copperheadhq/copperhead/manual-tests/real-designs/examples/cm5_minima/render/drawn.png

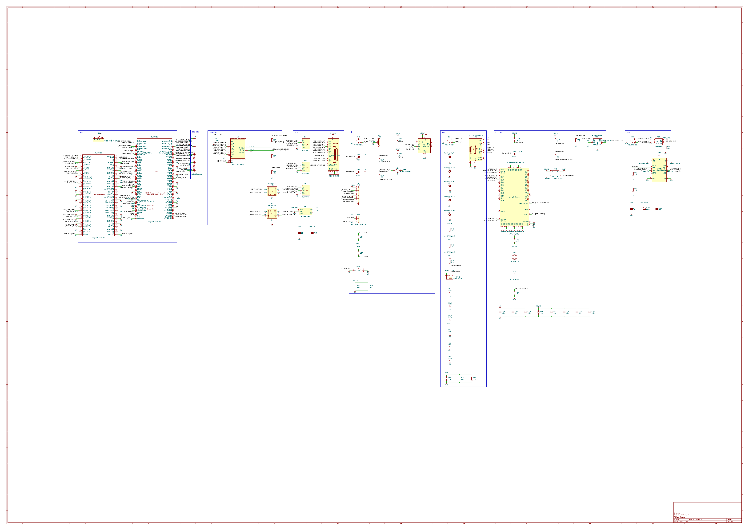
manual-tests/real-designs/examples/cm5_minima/render/drawn.png
