copperheadhq/copperhead/manual-tests/real-designs/examples/cm5_minima/render/original-CM5_MINIMA_3-HDMI.png

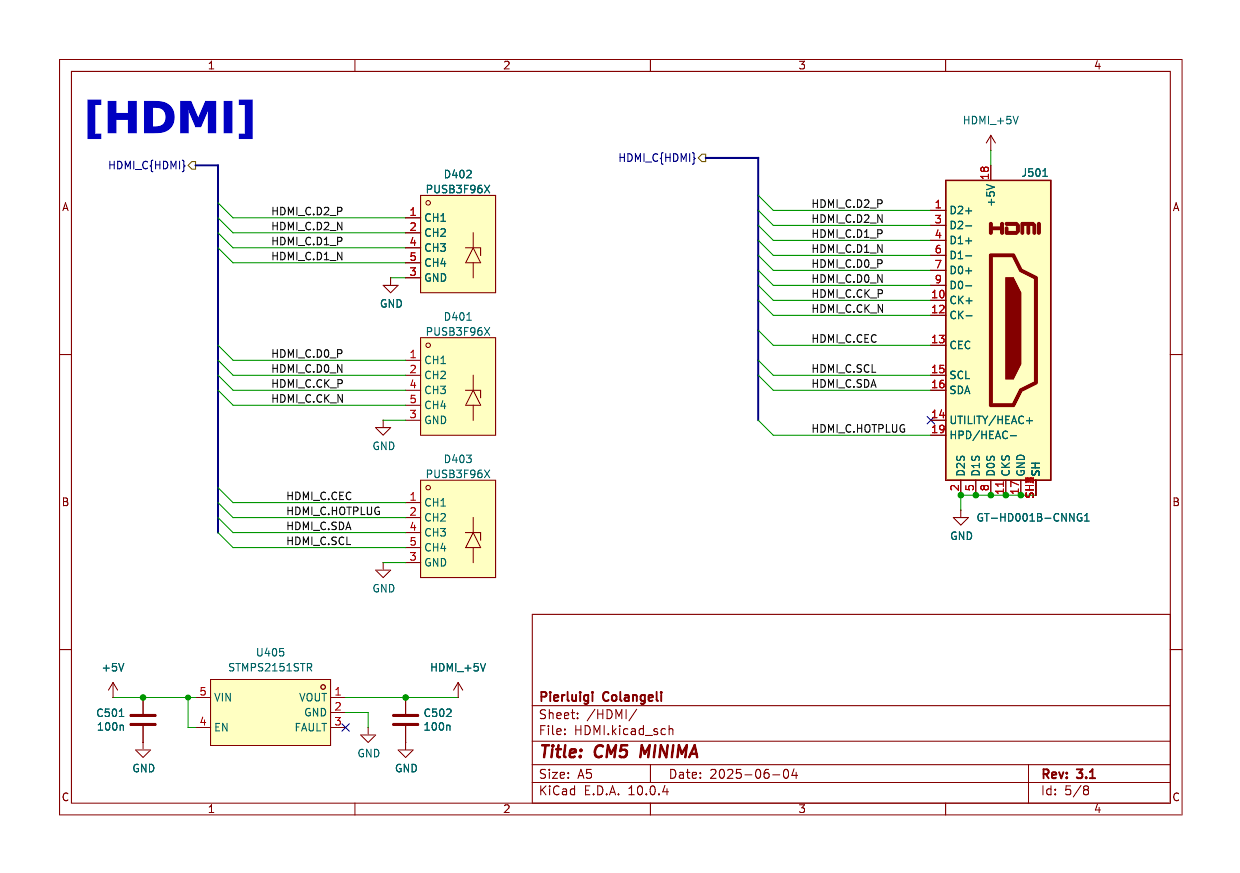
manual-tests/real-designs/examples/cm5_minima/render/original-CM5_MINIMA_3-HDMI.png
