copperheadhq/copperhead/manual-tests/real-designs/examples/complex_hierarchy/render/original-complex_hierarchy-ampli_ht_horizontal.png

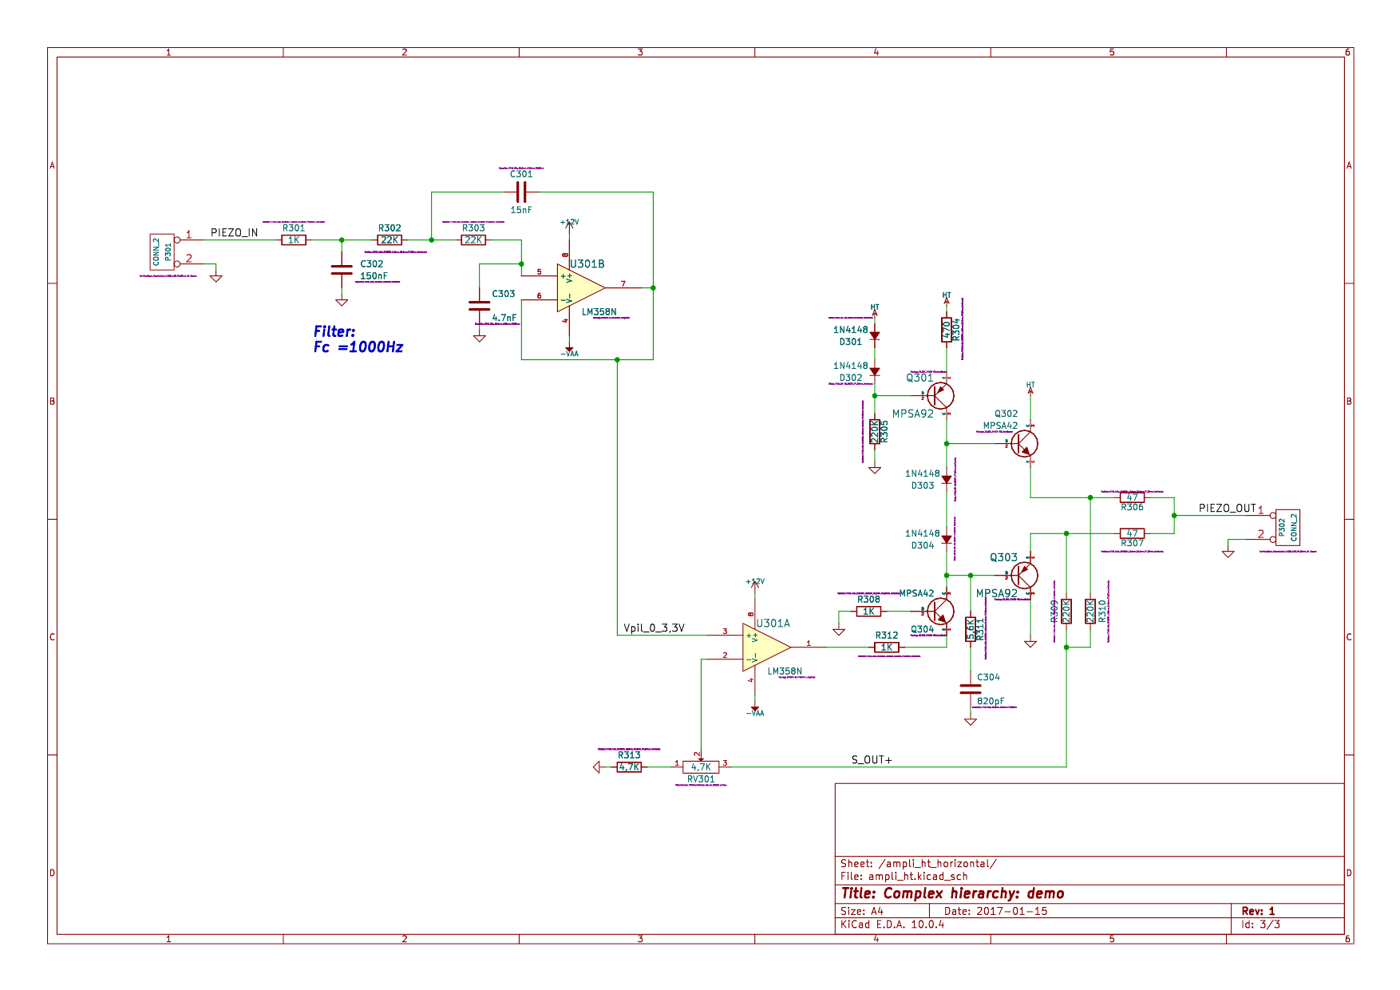
manual-tests/real-designs/examples/complex_hierarchy/render/original-complex_hierarchy-ampli_ht_horizontal.png
