copperheadhq/copperhead/manual-tests/real-designs/examples/complex_hierarchy/render/original-complex_hierarchy.png

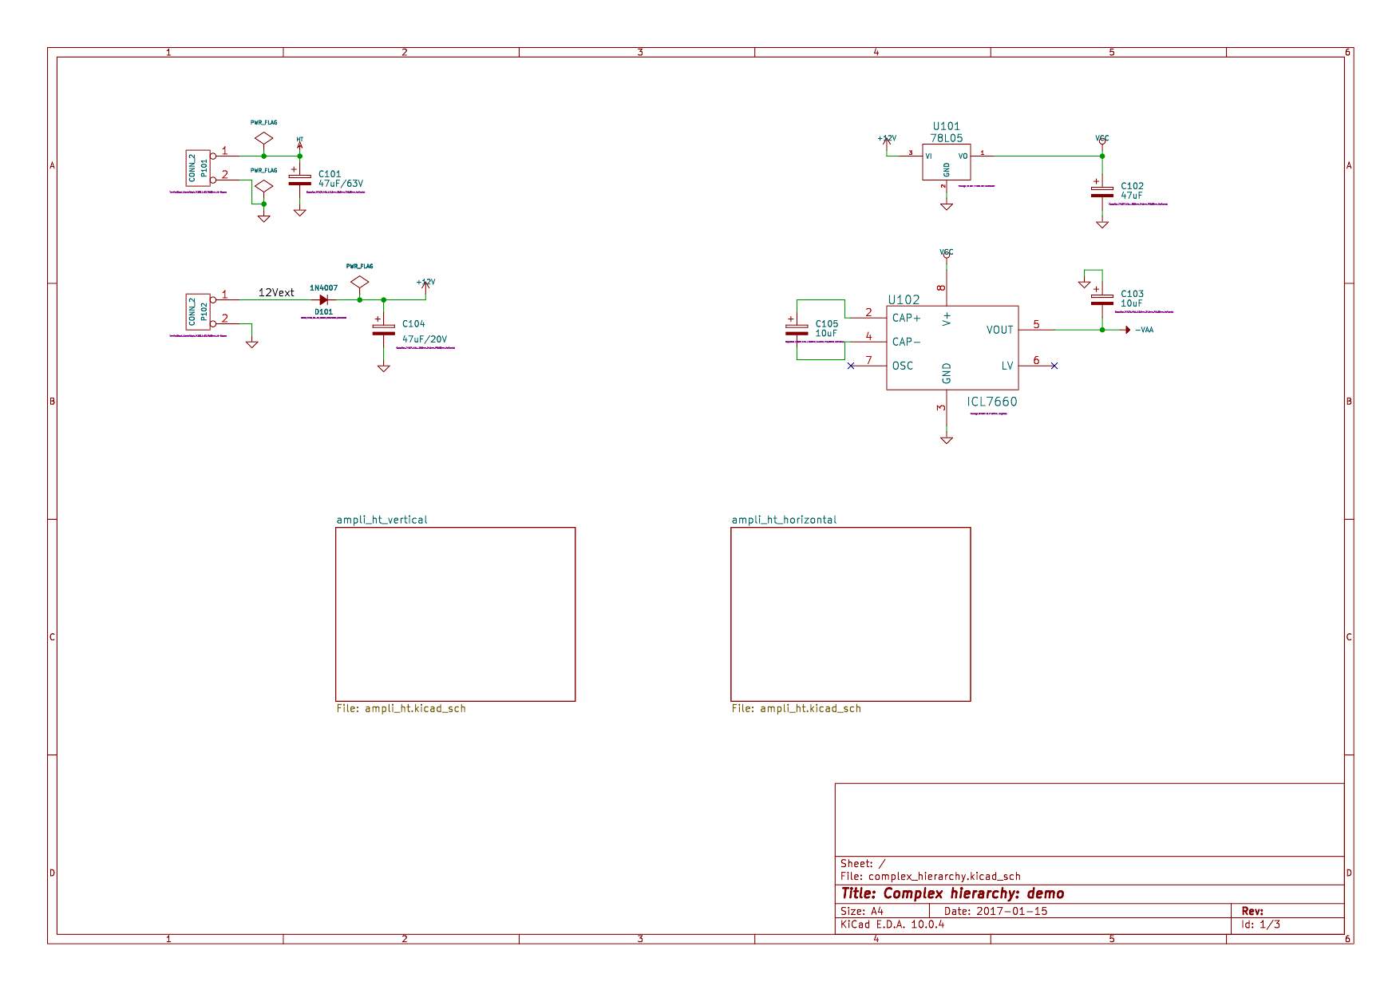
manual-tests/real-designs/examples/complex_hierarchy/render/original-complex_hierarchy.png
