copperheadhq/copperhead/manual-tests/real-designs/examples/ecc83/render/drawn.png

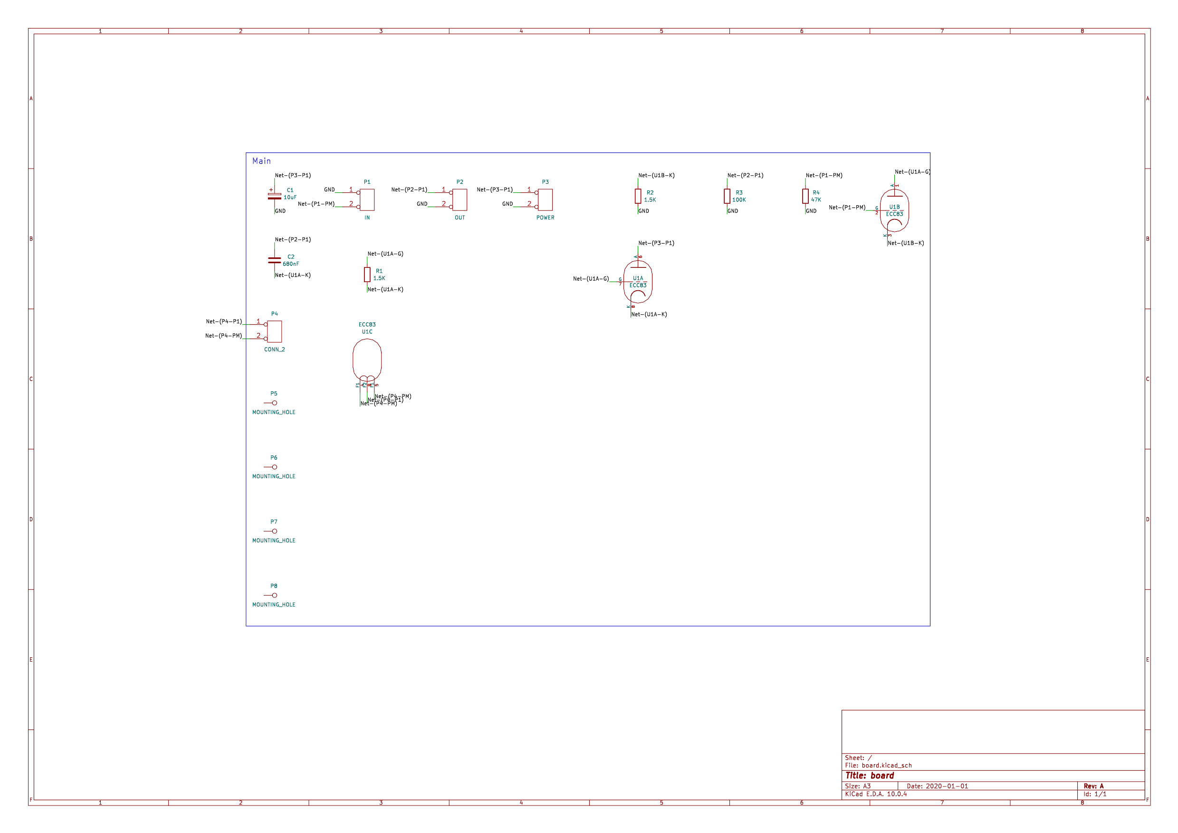
manual-tests/real-designs/examples/ecc83/render/drawn.png
