copperheadhq/copperhead/manual-tests/real-designs/examples/ecc83/render/original.png

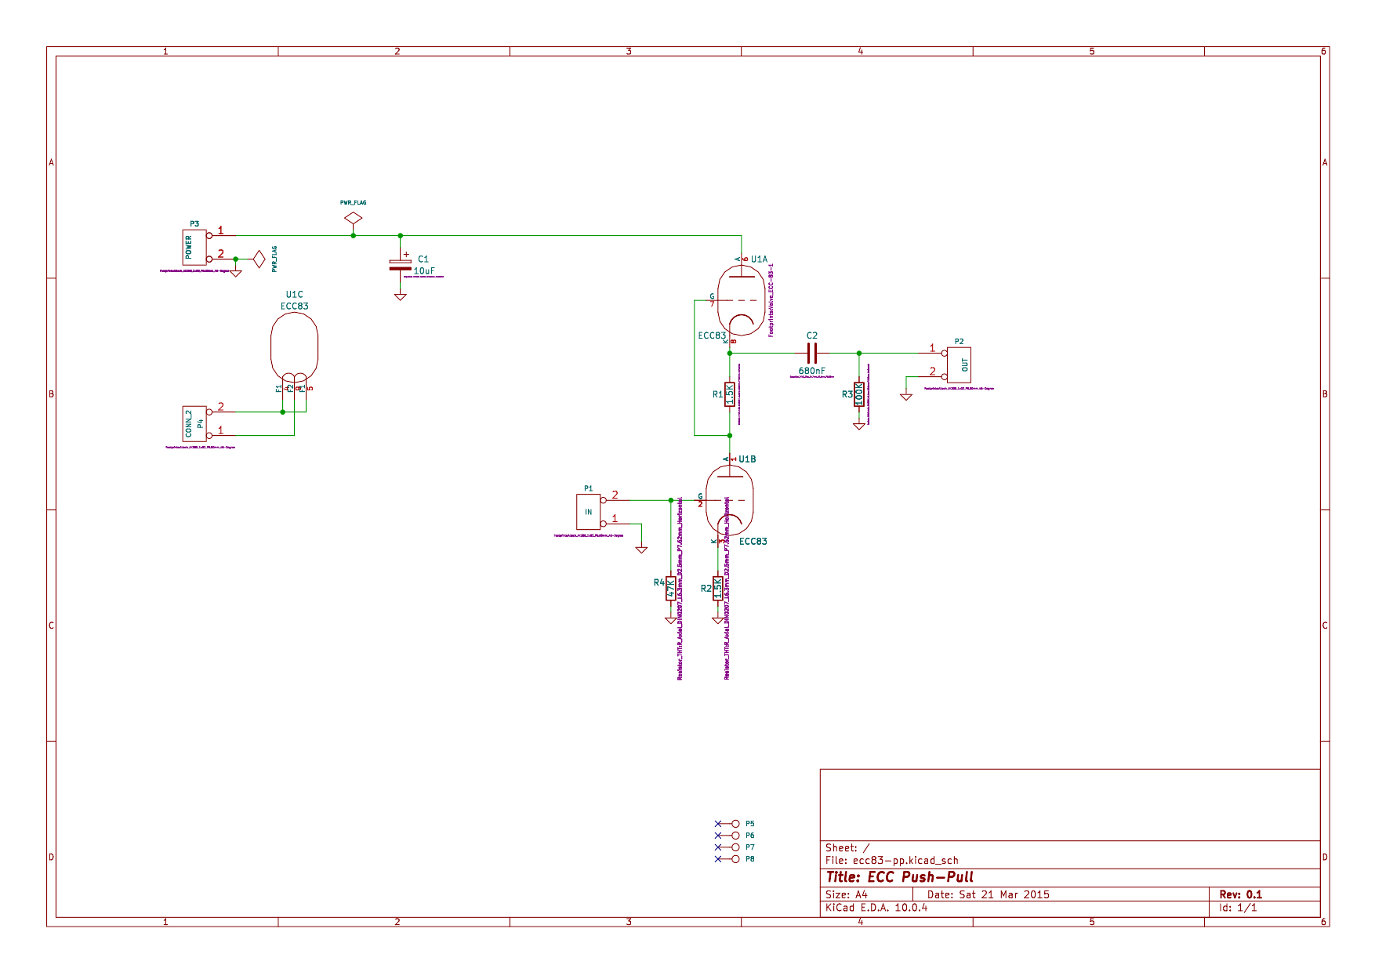
manual-tests/real-designs/examples/ecc83/render/original.png
