copperheadhq/copperhead/manual-tests/real-designs/examples/interf_u/render/drawn.png

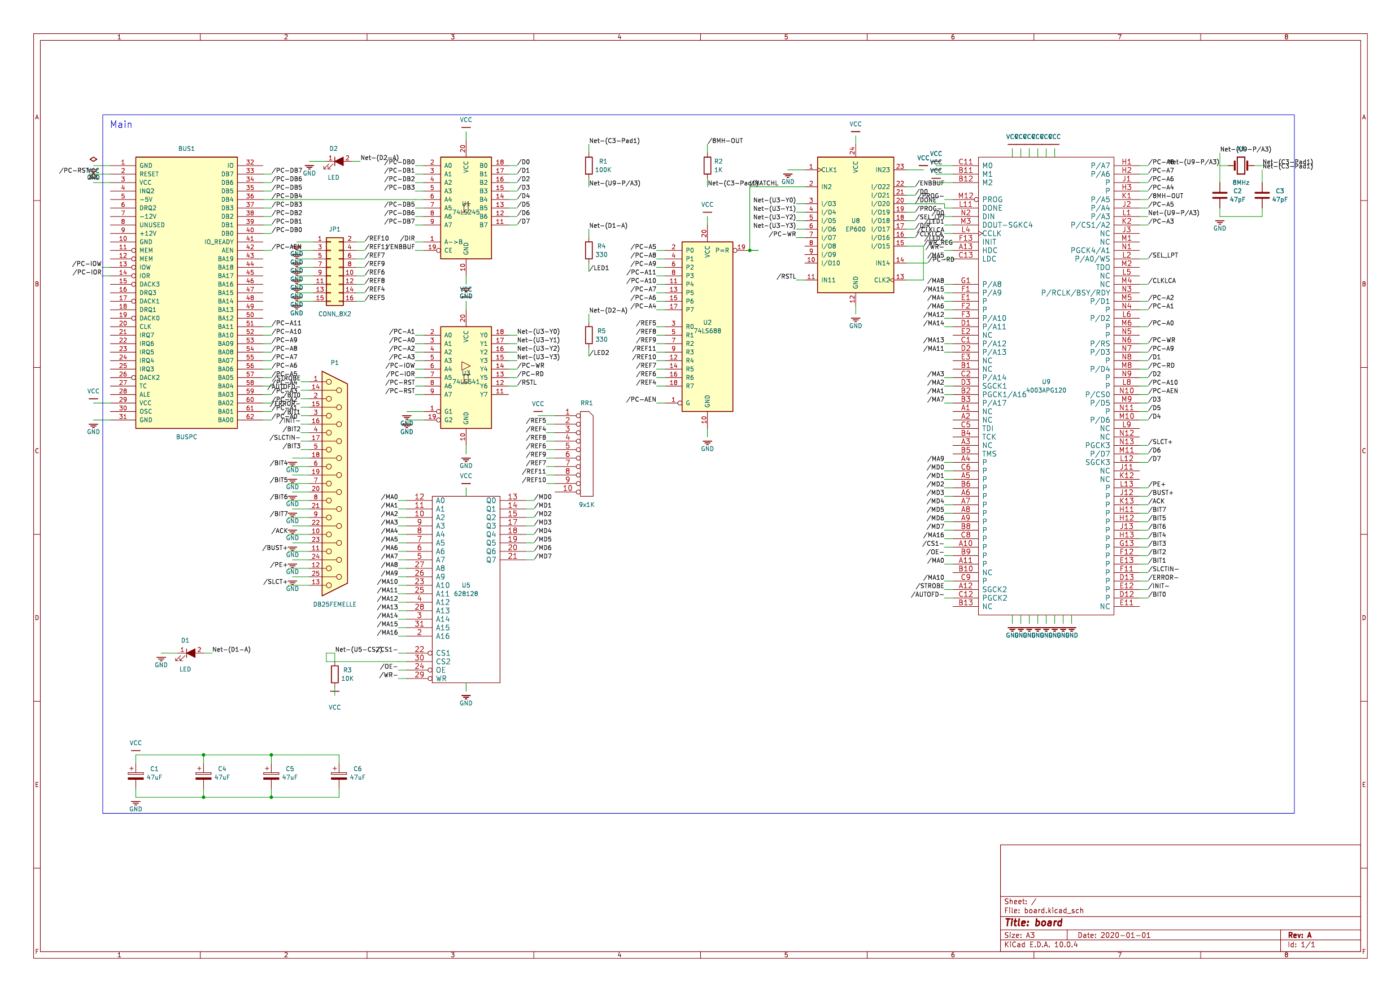
manual-tests/real-designs/examples/interf_u/render/drawn.png
