copperheadhq/copperhead/manual-tests/real-designs/examples/interf_u/render/original.png

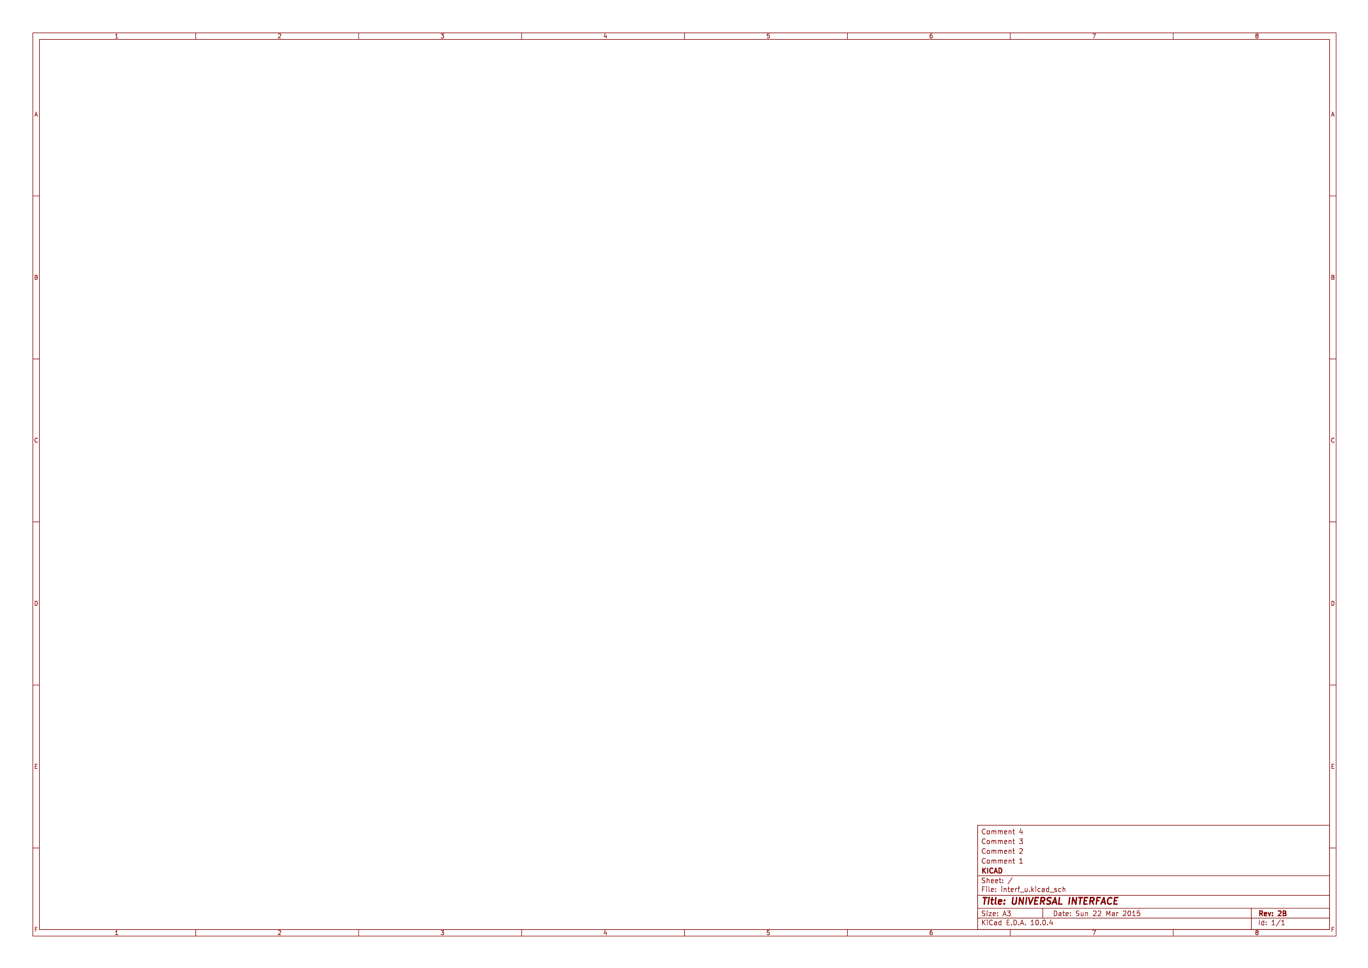
manual-tests/real-designs/examples/interf_u/render/original.png
