copperheadhq/copperhead/manual-tests/real-designs/examples/kit-dev-coldfire-xilinx_5213/render/original-kit-dev-coldfire-xilinx_5213.png

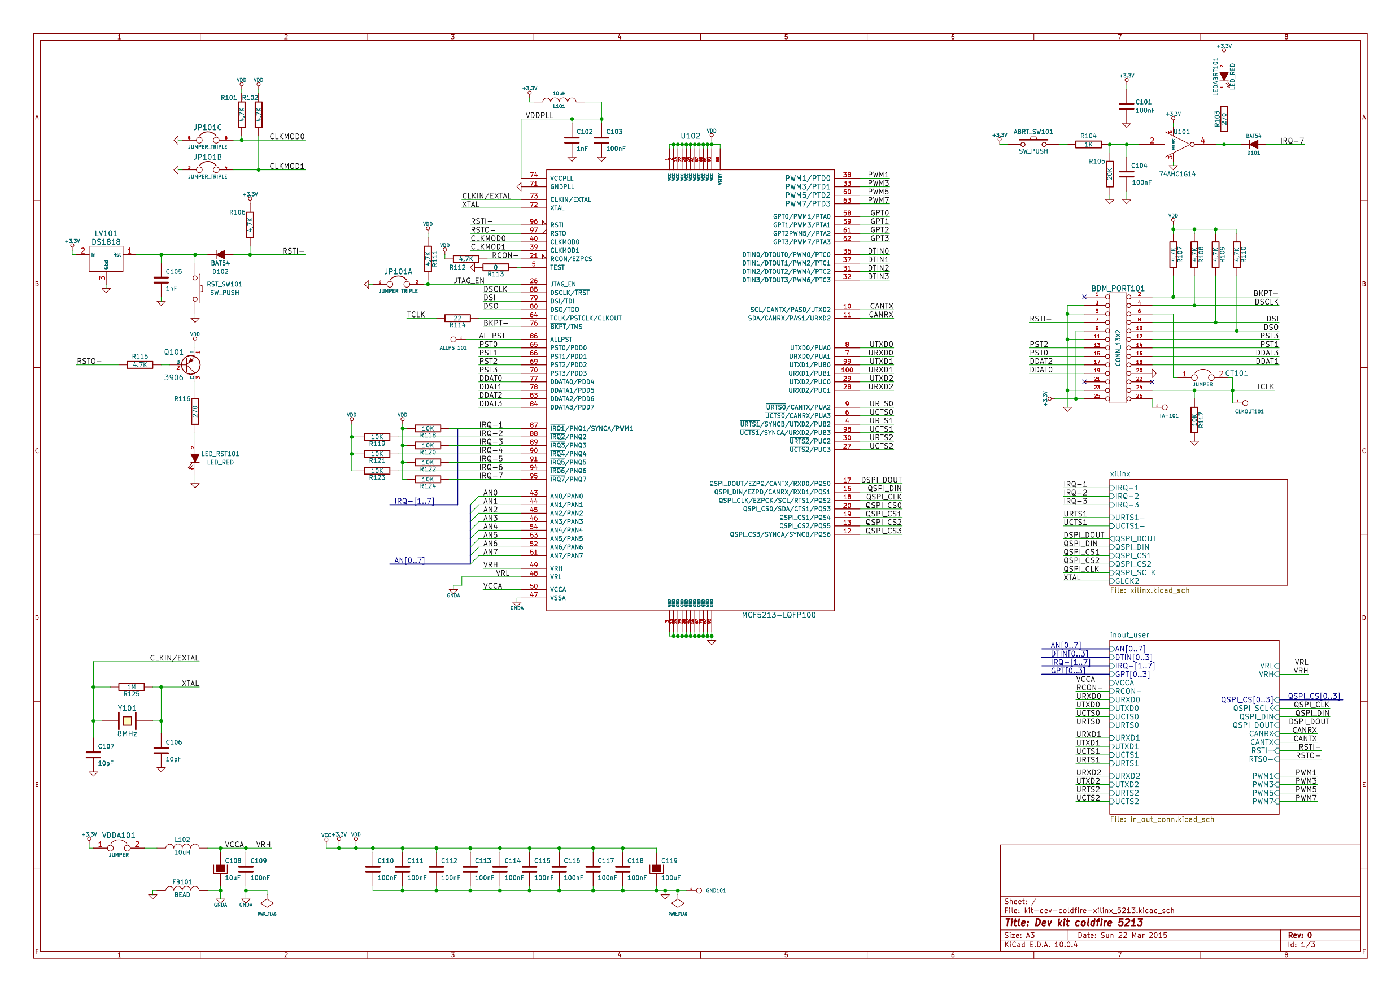
manual-tests/real-designs/examples/kit-dev-coldfire-xilinx_5213/render/original-kit-dev-coldfire-xilinx_5213.png
