copperheadhq/copperhead/manual-tests/real-designs/examples/multichannel/render/original-multichannel_mixer-CH1.png

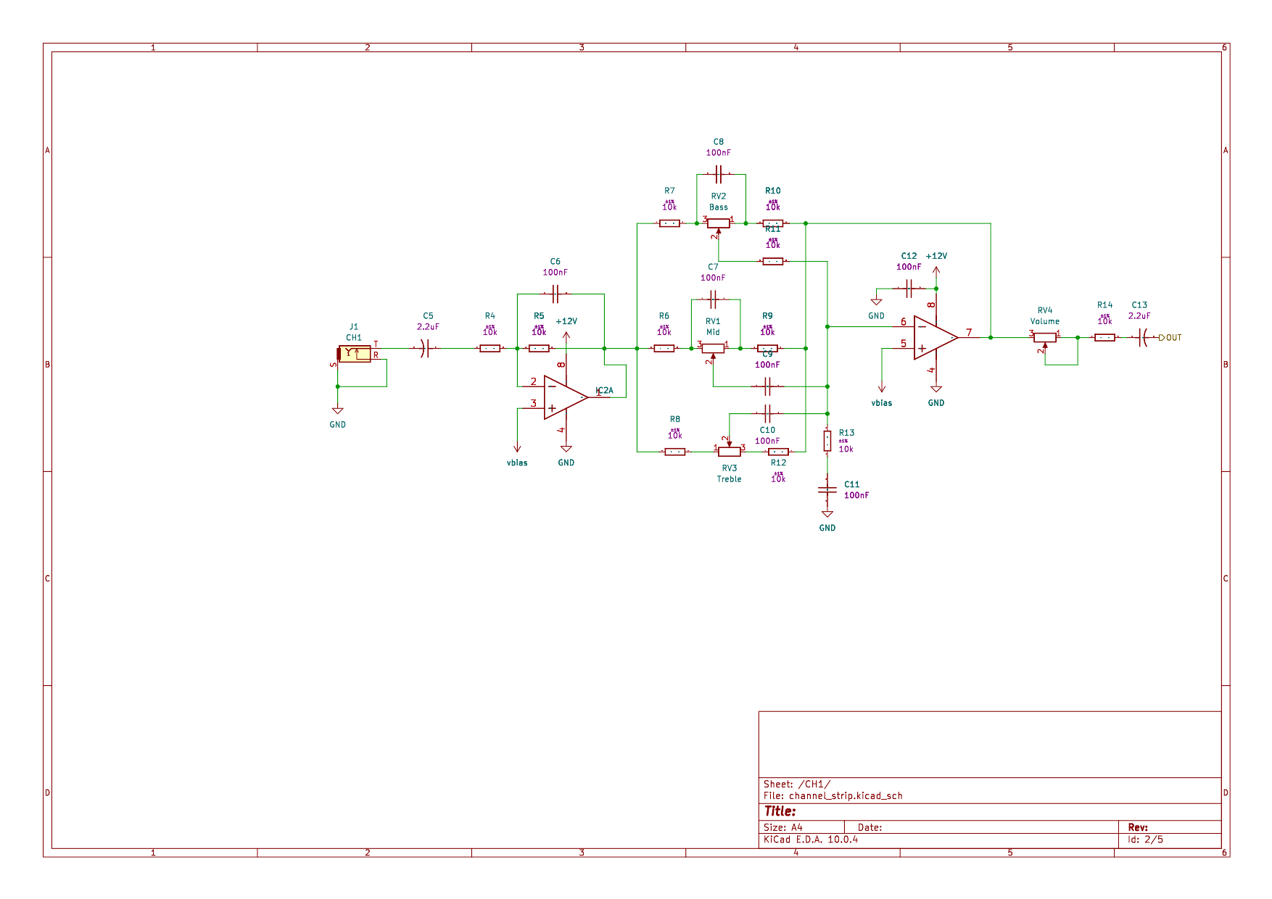
manual-tests/real-designs/examples/multichannel/render/original-multichannel_mixer-CH1.png
