copperheadhq/copperhead/manual-tests/real-designs/examples/multichannel/render/original-multichannel_mixer.png

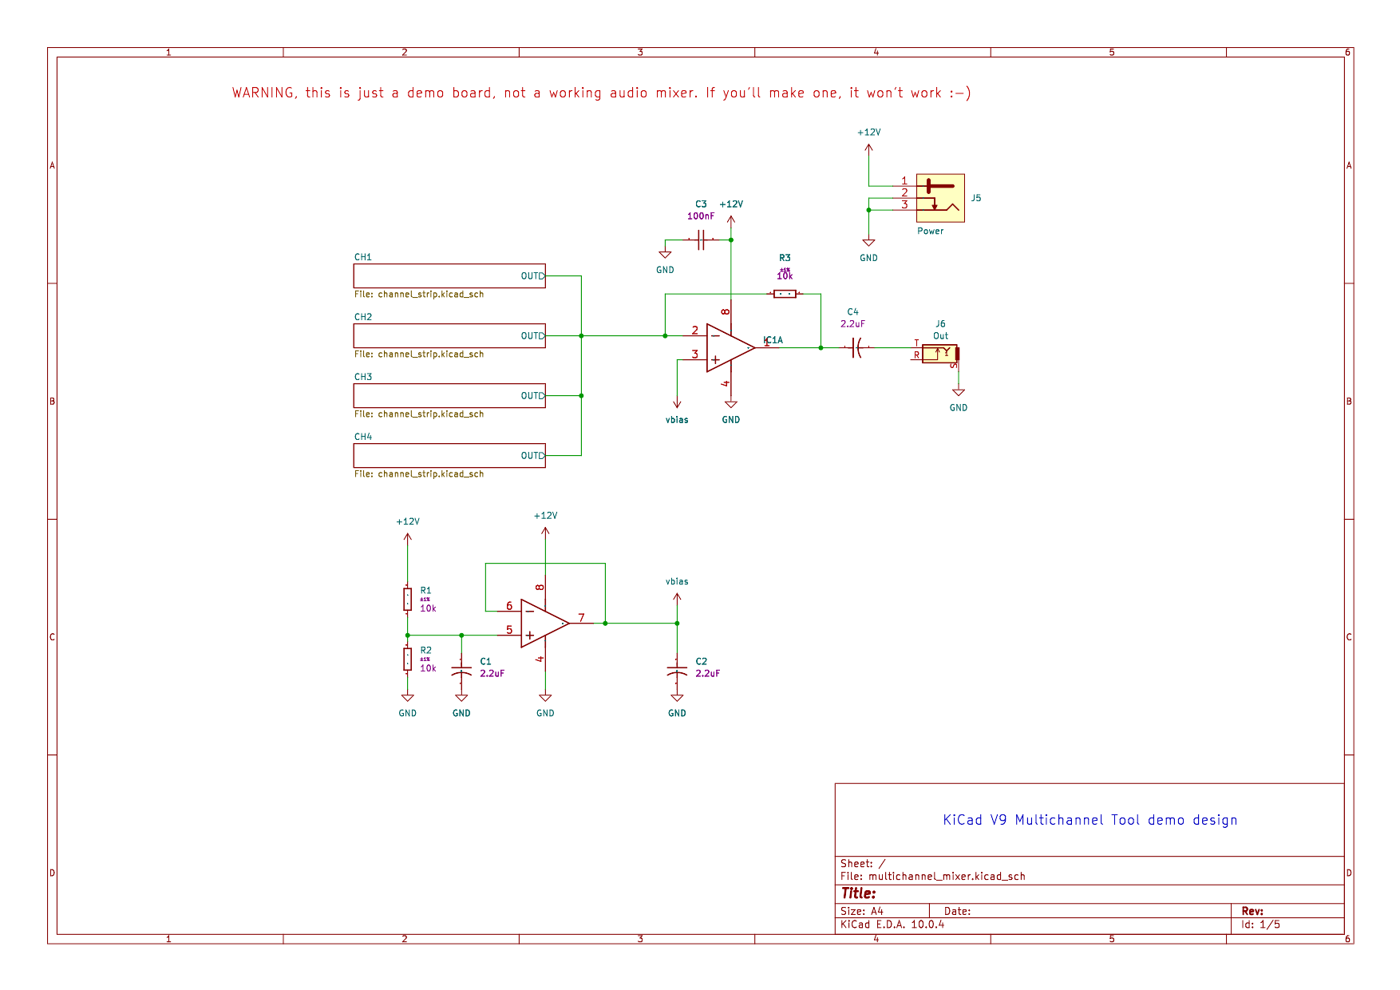
manual-tests/real-designs/examples/multichannel/render/original-multichannel_mixer.png
