copperheadhq/copperhead/manual-tests/real-designs/examples/pic_programmer/render/original-pic_programmer.png

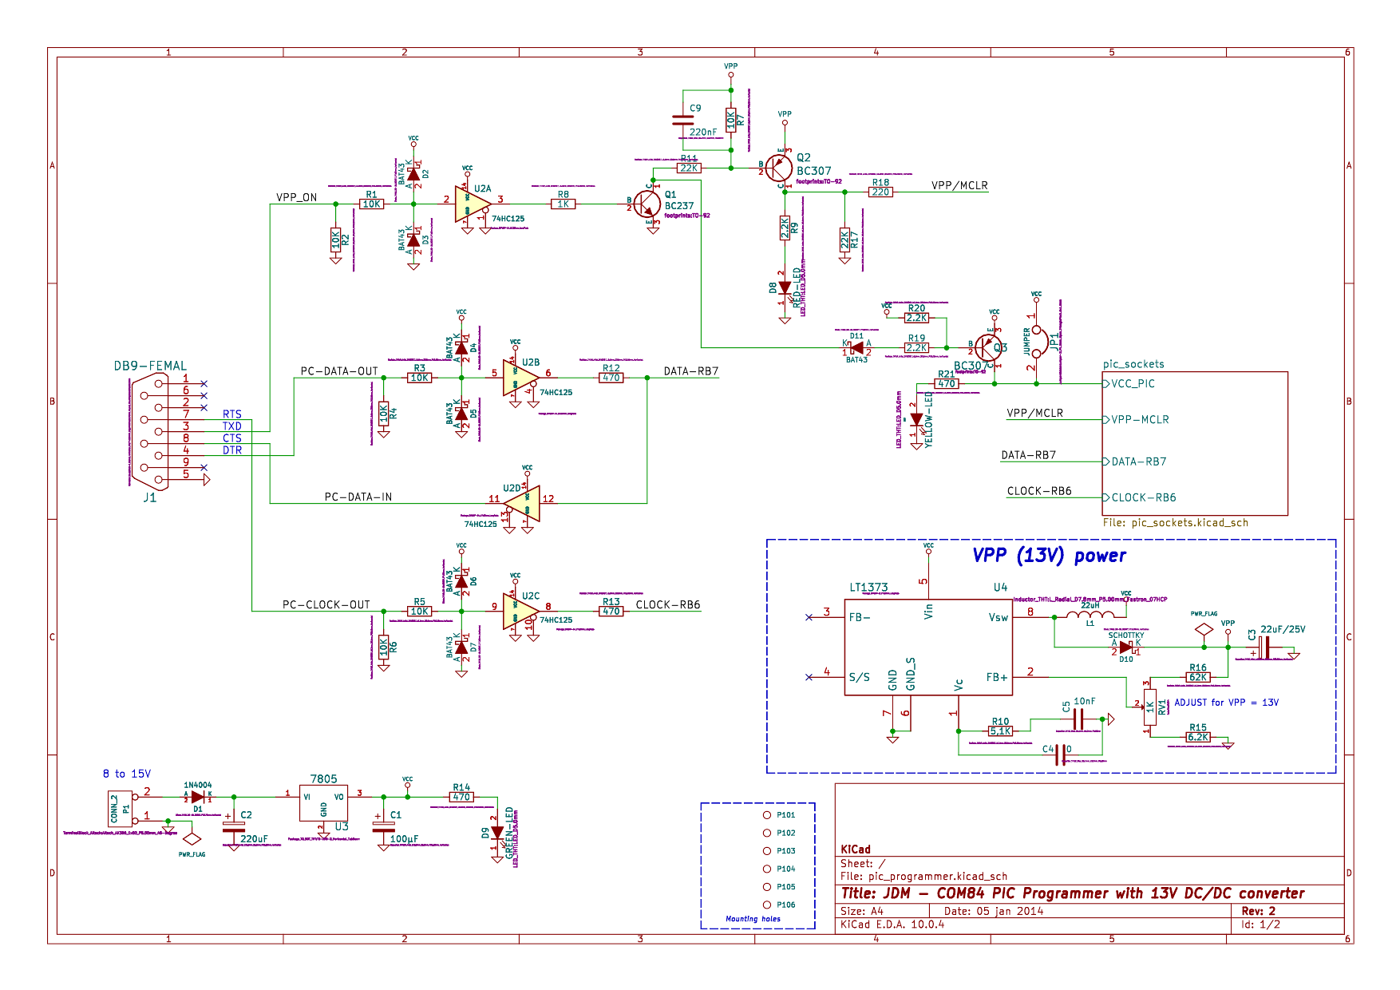
manual-tests/real-designs/examples/pic_programmer/render/original-pic_programmer.png
