copperheadhq/copperhead/manual-tests/real-designs/examples/royalblue54L_feather/render/original-RoyalBlue54L-Feather-nRF54L15.png

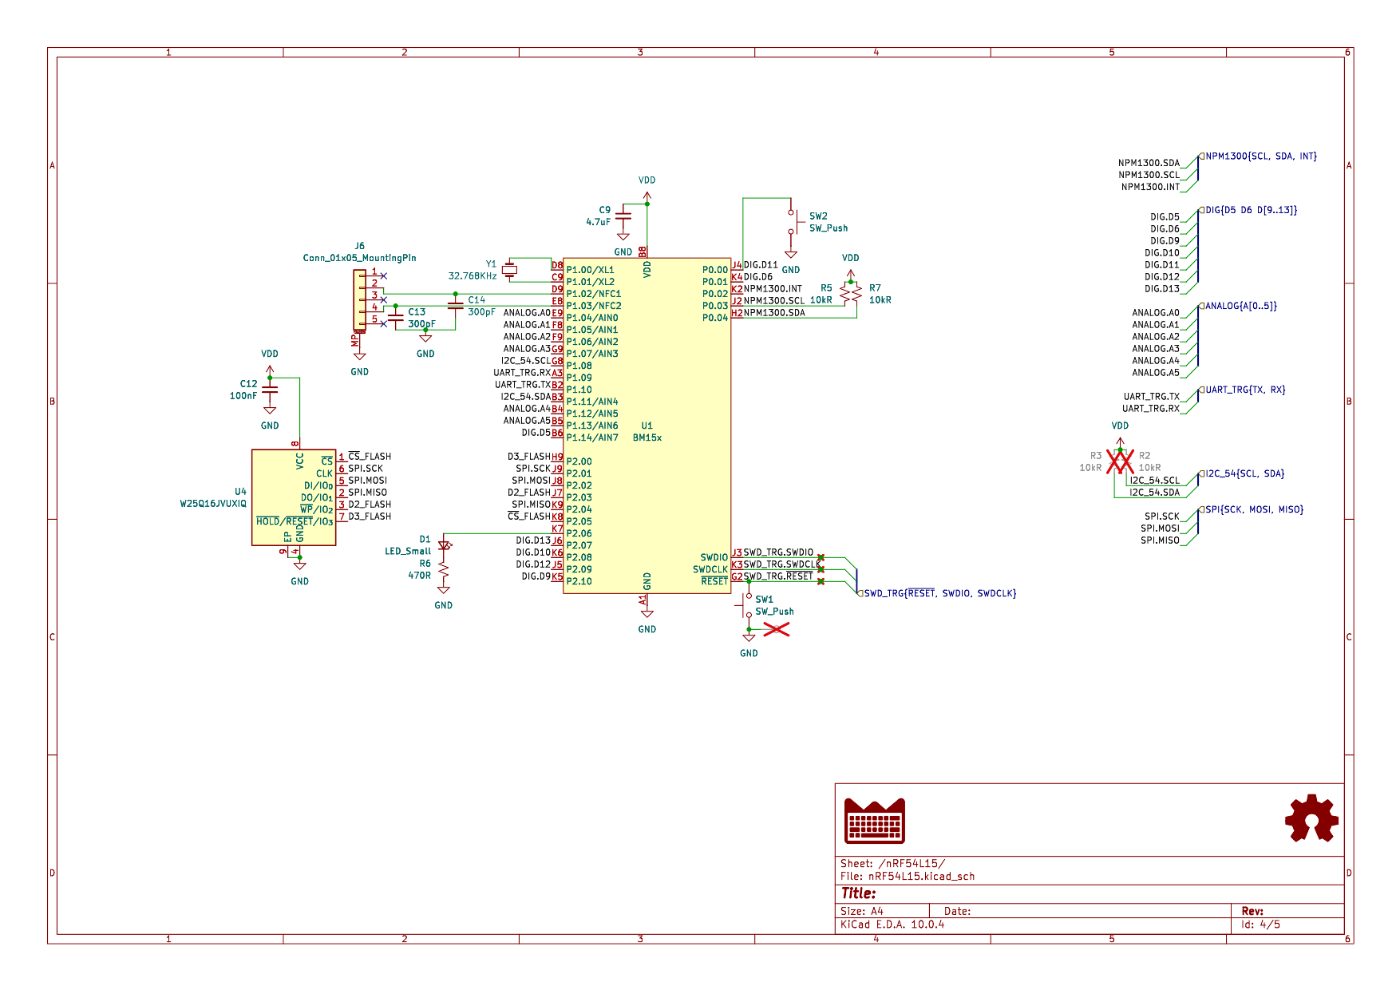
manual-tests/real-designs/examples/royalblue54L_feather/render/original-RoyalBlue54L-Feather-nRF54L15.png
