copperheadhq/copperhead/manual-tests/real-designs/examples/royalblue54L_feather/render/original-RoyalBlue54L-Feather.png

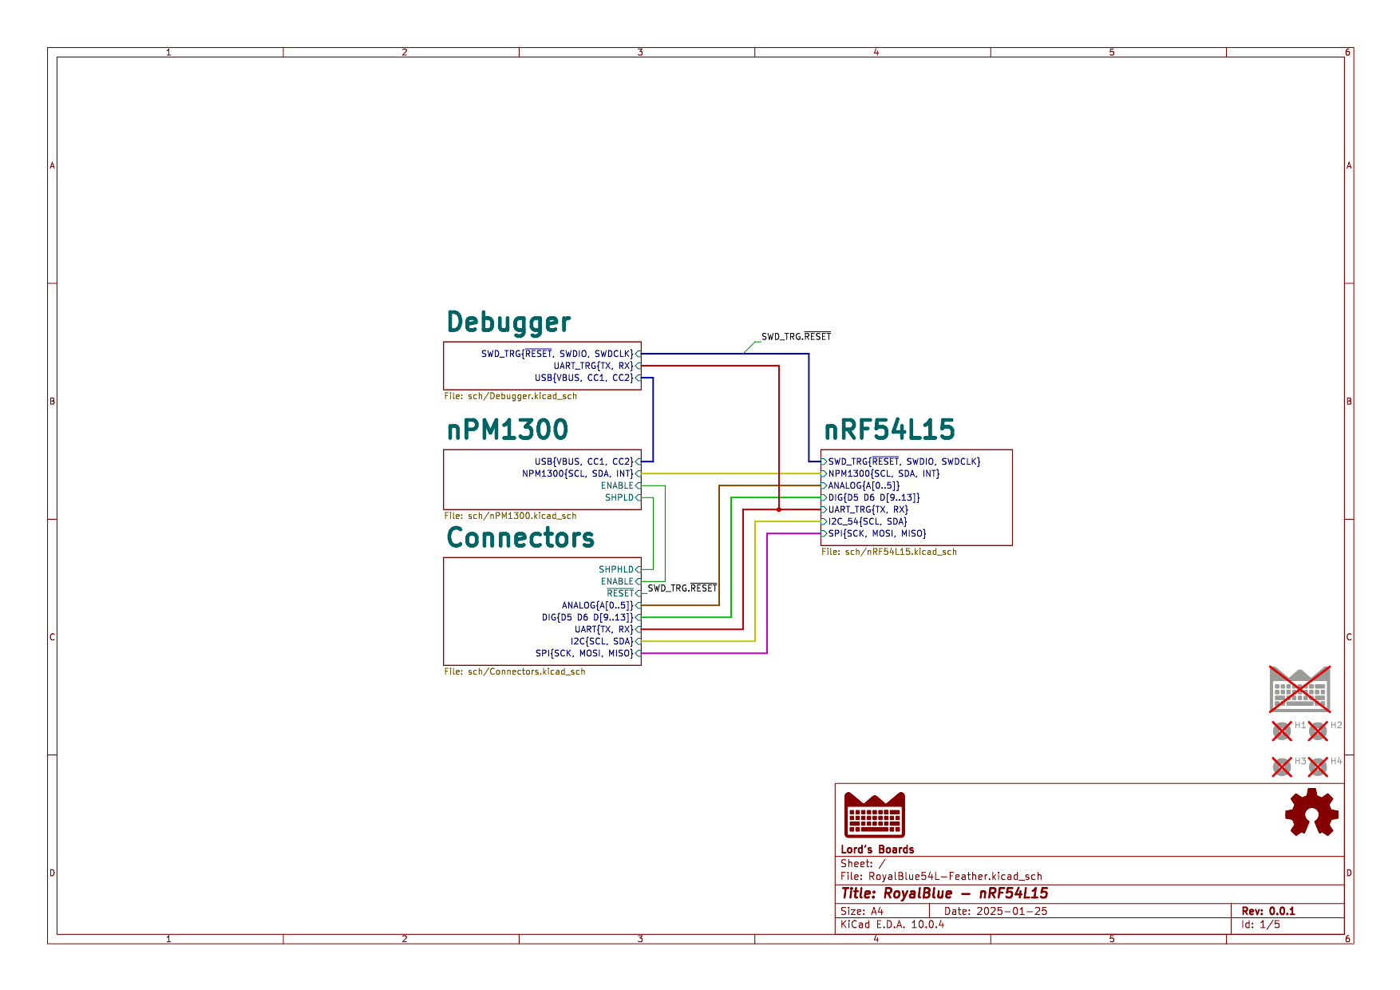
manual-tests/real-designs/examples/royalblue54L_feather/render/original-RoyalBlue54L-Feather.png
