copperheadhq/copperhead/manual-tests/real-designs/examples/sonde xilinx/render/drawn.png

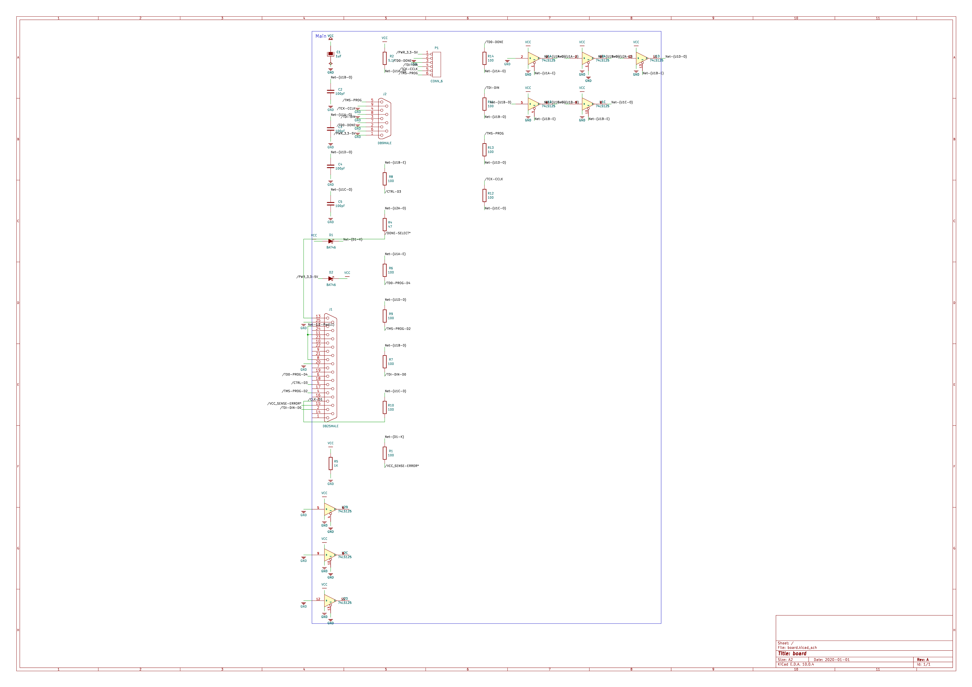
manual-tests/real-designs/examples/sonde xilinx/render/drawn.png
