copperheadhq/copperhead/manual-tests/real-designs/examples/sonde xilinx/render/original.png

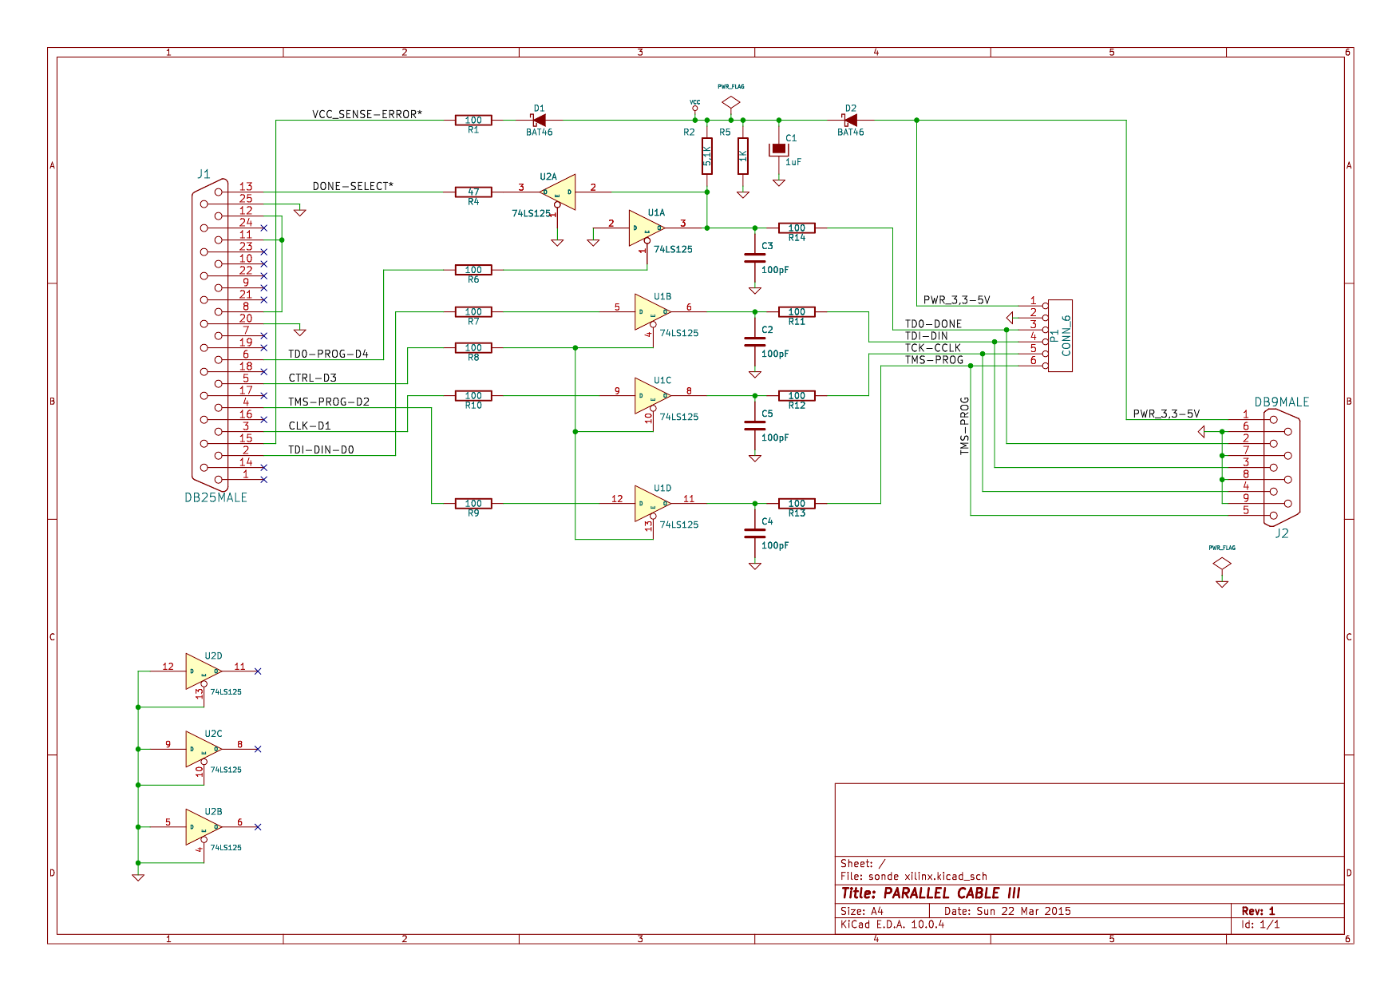
manual-tests/real-designs/examples/sonde xilinx/render/original.png
