copperheadhq/copperhead/manual-tests/real-designs/examples/tiny_tapeout/render/original-tinytapeout-demo-RP2040.png

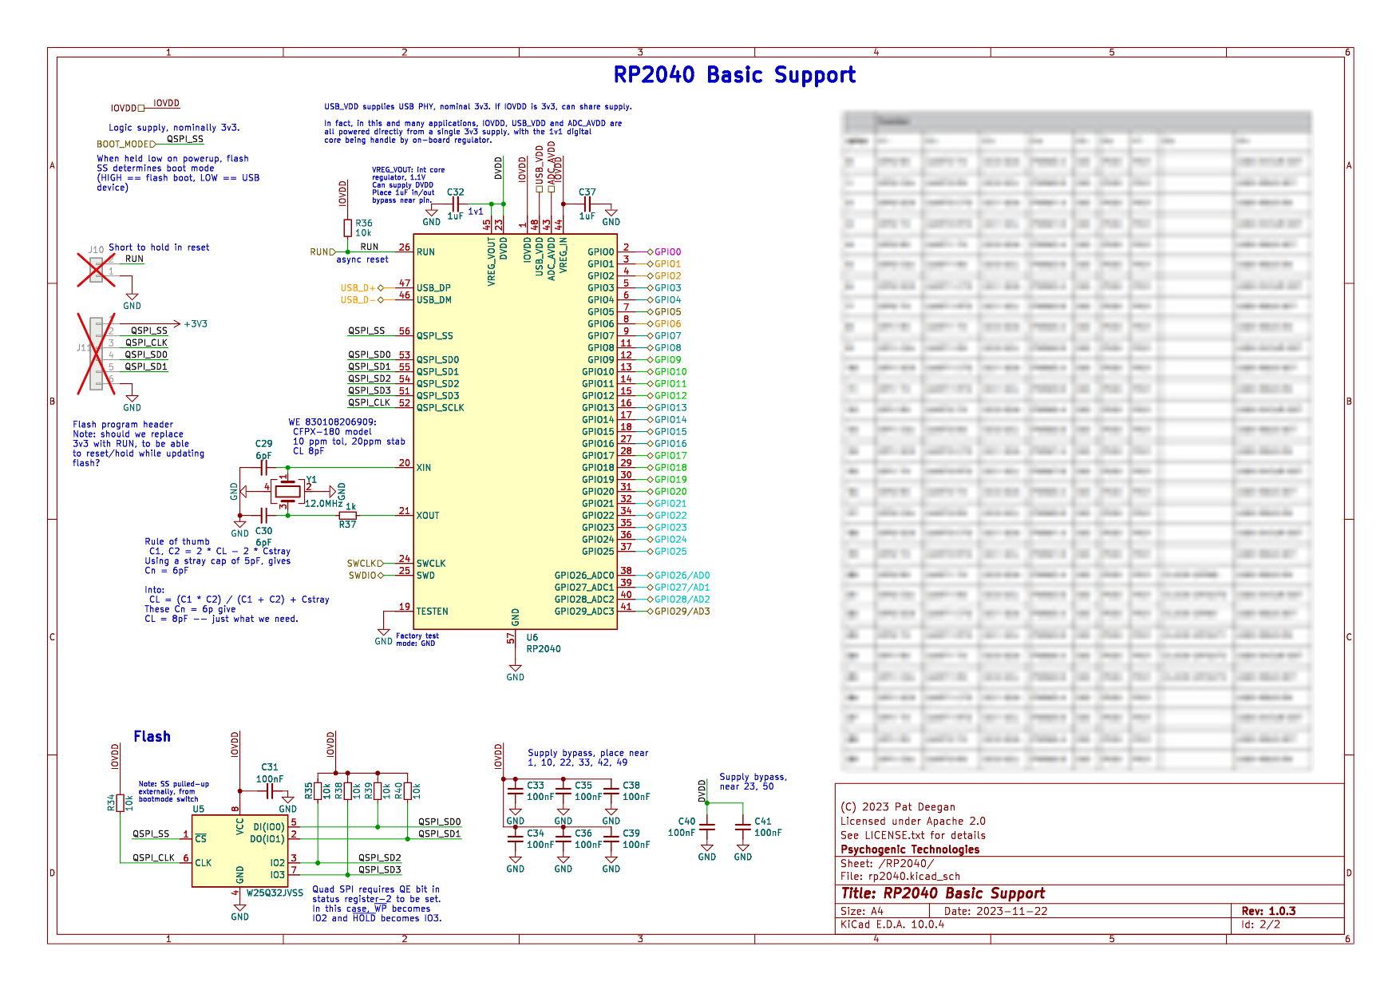
manual-tests/real-designs/examples/tiny_tapeout/render/original-tinytapeout-demo-RP2040.png
