copperheadhq/copperhead/manual-tests/reference-boards/buck-12v-5v/reference/buck-12v-5v.png

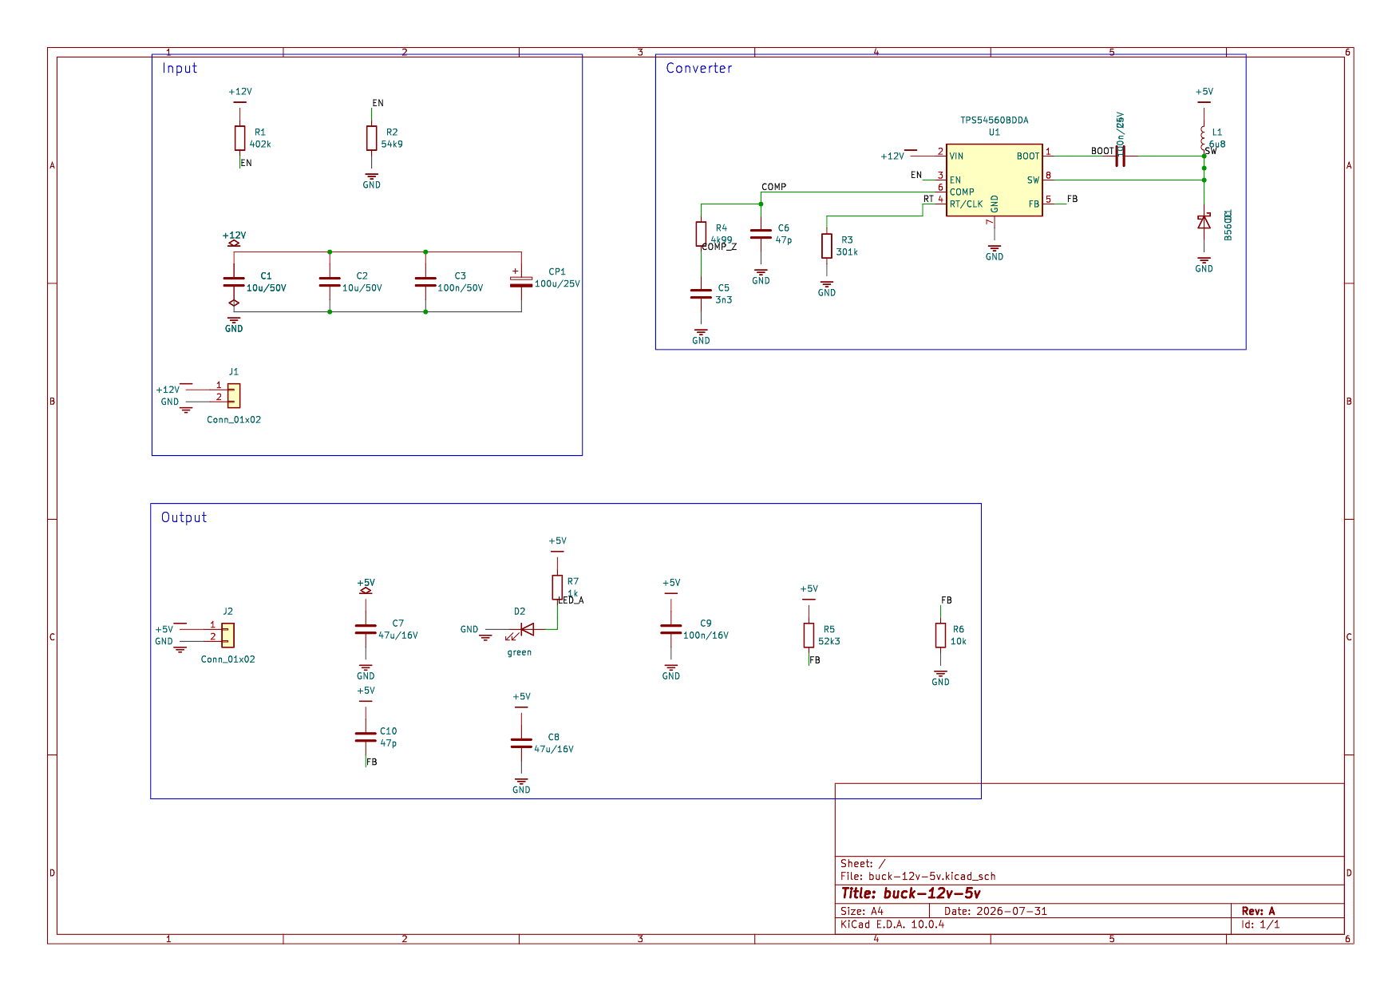
manual-tests/reference-boards/buck-12v-5v/reference/buck-12v-5v.png
