copperheadhq/copperhead/manual-tests/reference-boards/ldo-demo/reference/ldo-demo.png

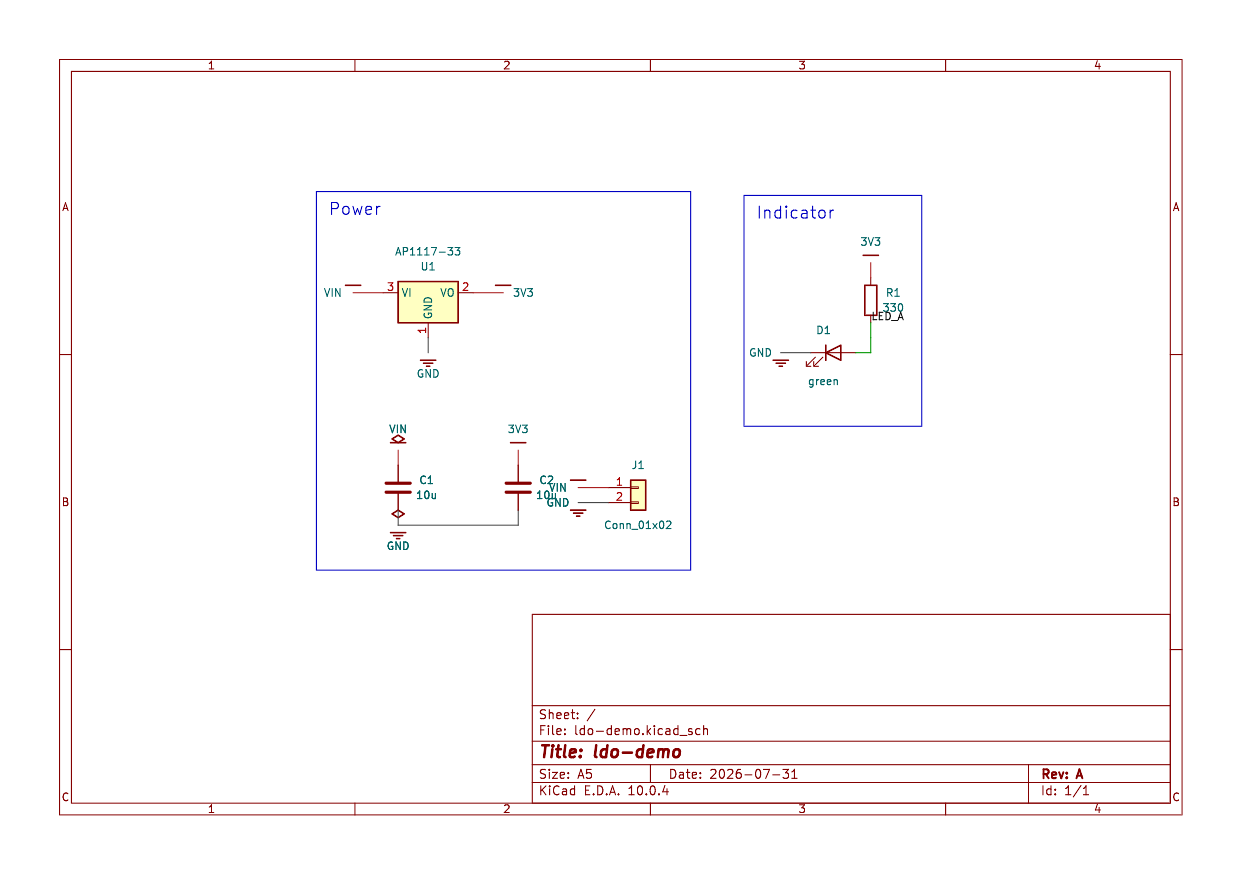
manual-tests/reference-boards/ldo-demo/reference/ldo-demo.png
