copperheadhq/copperhead/manual-tests/reference-boards/npn-switch/reference/npn-switch.png

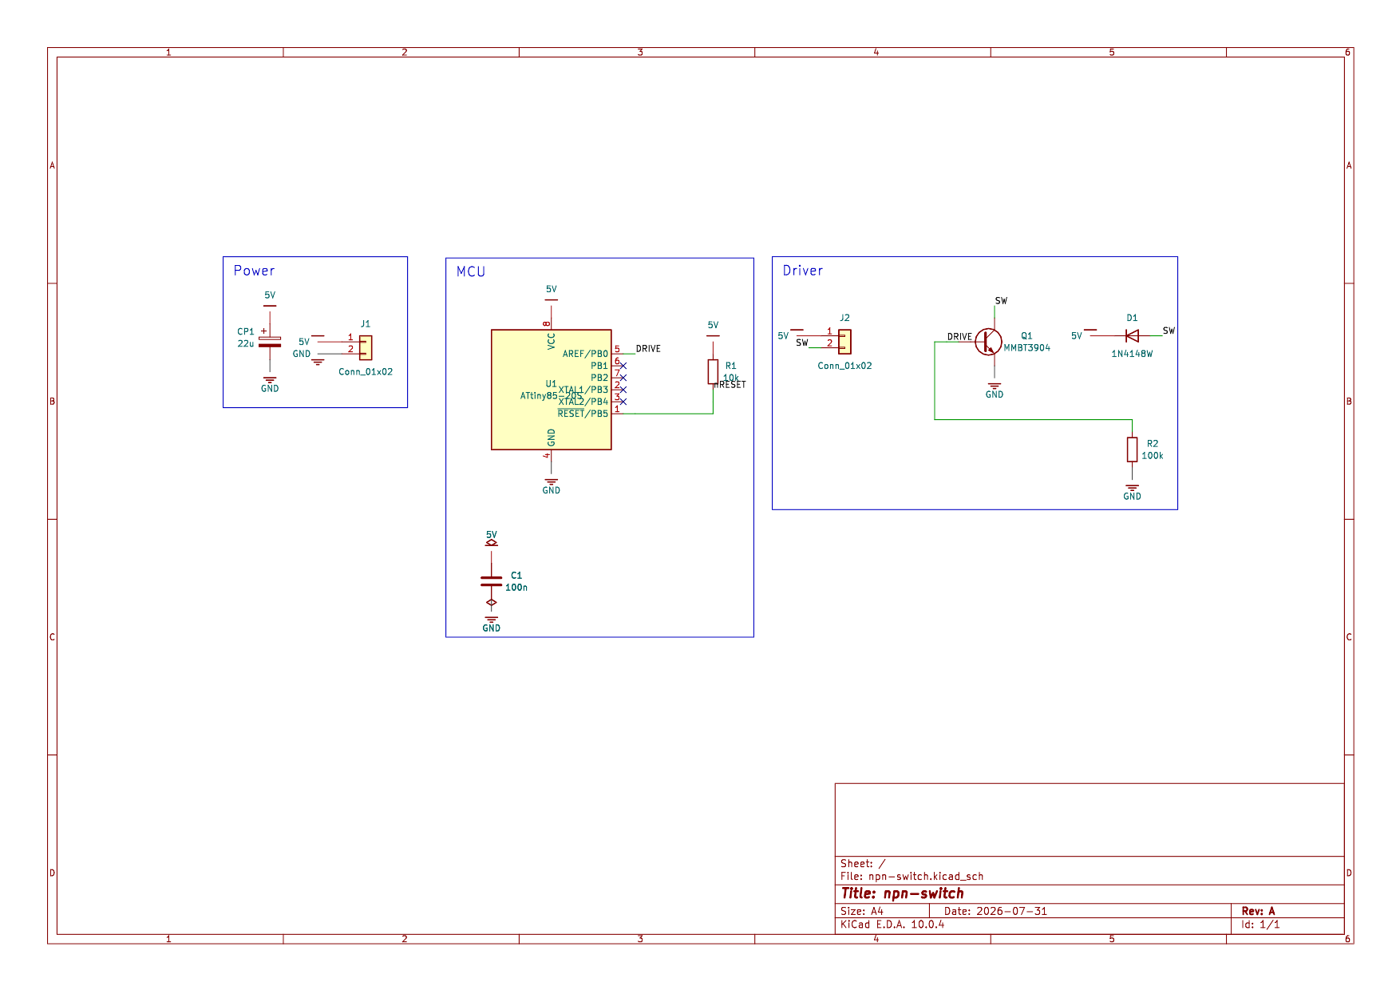
manual-tests/reference-boards/npn-switch/reference/npn-switch.png
