copperheadhq/copperhead/manual-tests/reference-boards/usb-atmega-node/reference/usb-atmega-node.png

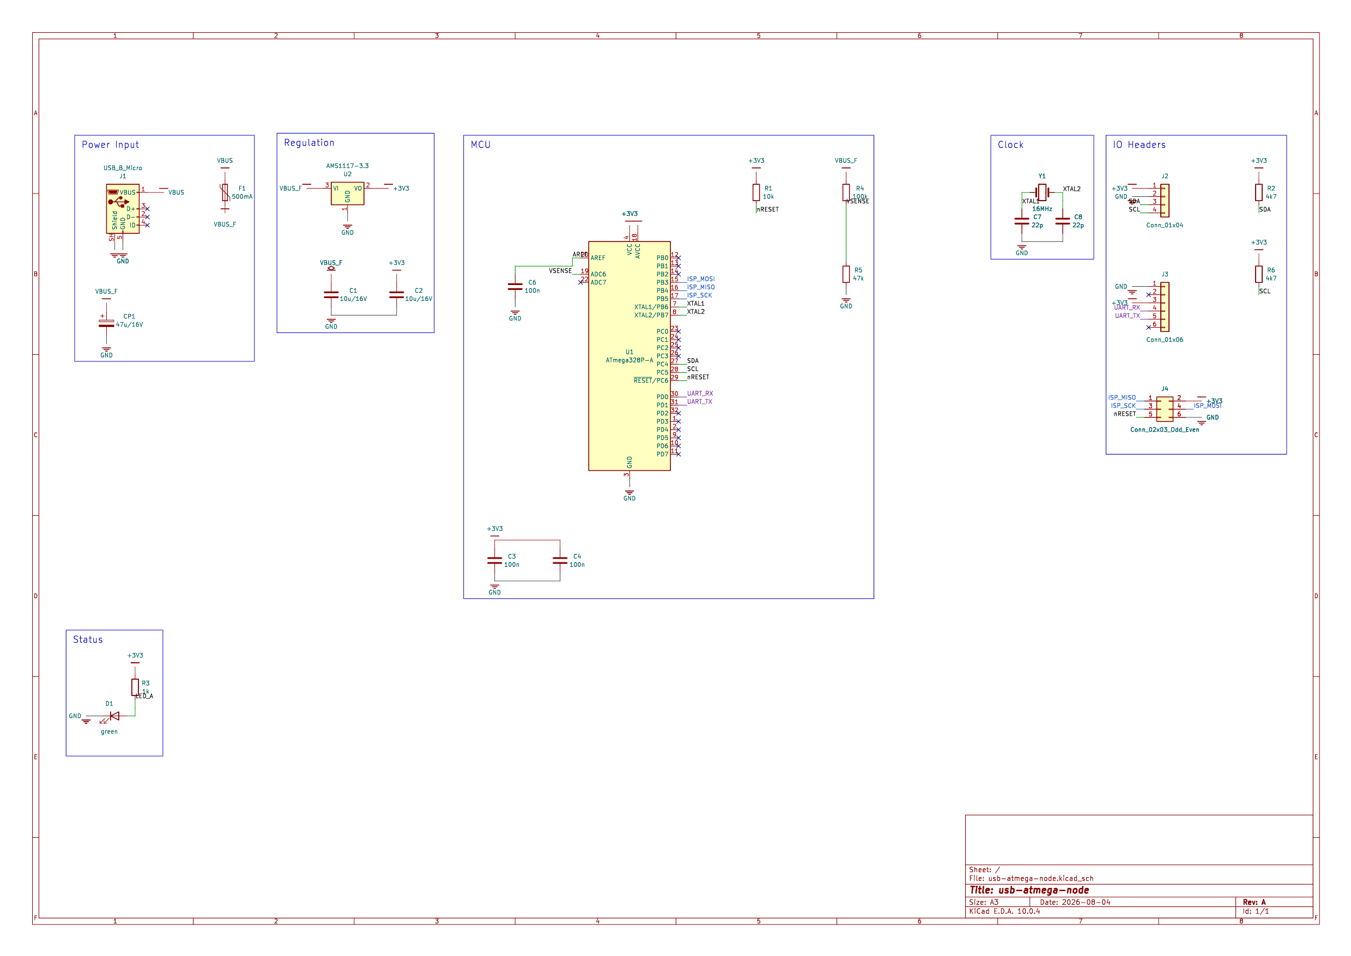
manual-tests/reference-boards/usb-atmega-node/reference/usb-atmega-node.png
