copperheadhq/copperhead/test/fixtures/golden/tierC-board.kicad_sch

## KiCad design test/fixtures/golden/tierC-board.kicad_sch (2026-09-05)

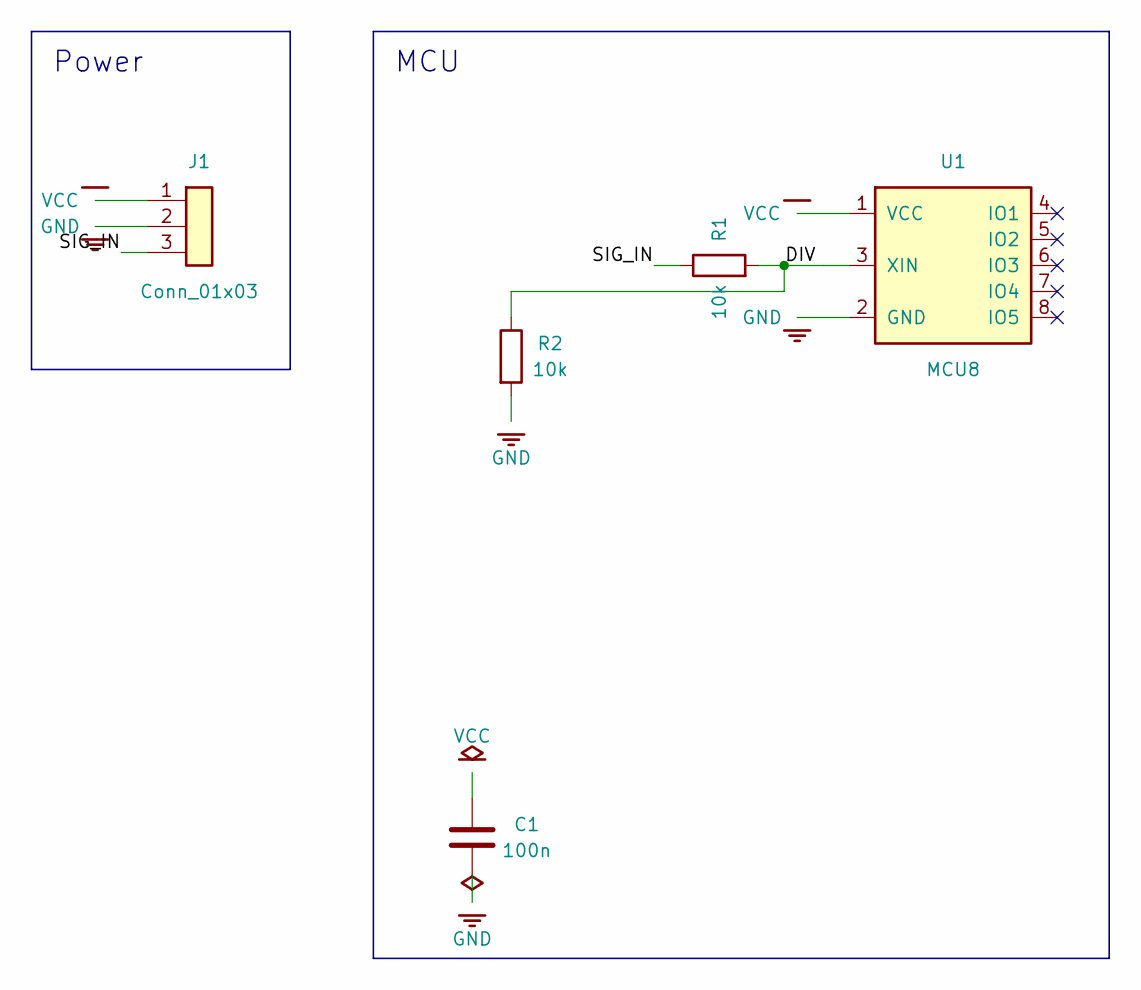
[picture p41: schematic tierC-board.kicad_sch]

Parts:
C1: 100n; C_0402_1005Metric
J1: Conn_01x03; PinHeader_1x03_P2.54mm_Vertical
R1, R2: 10k; R_0603_1608Metric
U1: MCU8; SOIC-8_3.9x4.9mm_P1.27mm

Connections:
DIV: R1.2, R2.1, U1.3 (XIN)
GND: C1.2, J1.2, R2.2, U1.2 (GND)
SIG_IN: J1.3, R1.1
VCC: C1.1, J1.1, U1.1 (VCC)

Notes on the sheet:
MCU
Power
