copperheadhq/copperhead/manual-tests/reference-boards/buck-12v-5v/reference/buck-12v-5v.kicad_sch

## KiCad design manual-tests/reference-boards/buck-12v-5v/reference/buck-12v-5v.kicad_sch (2026-09-05)

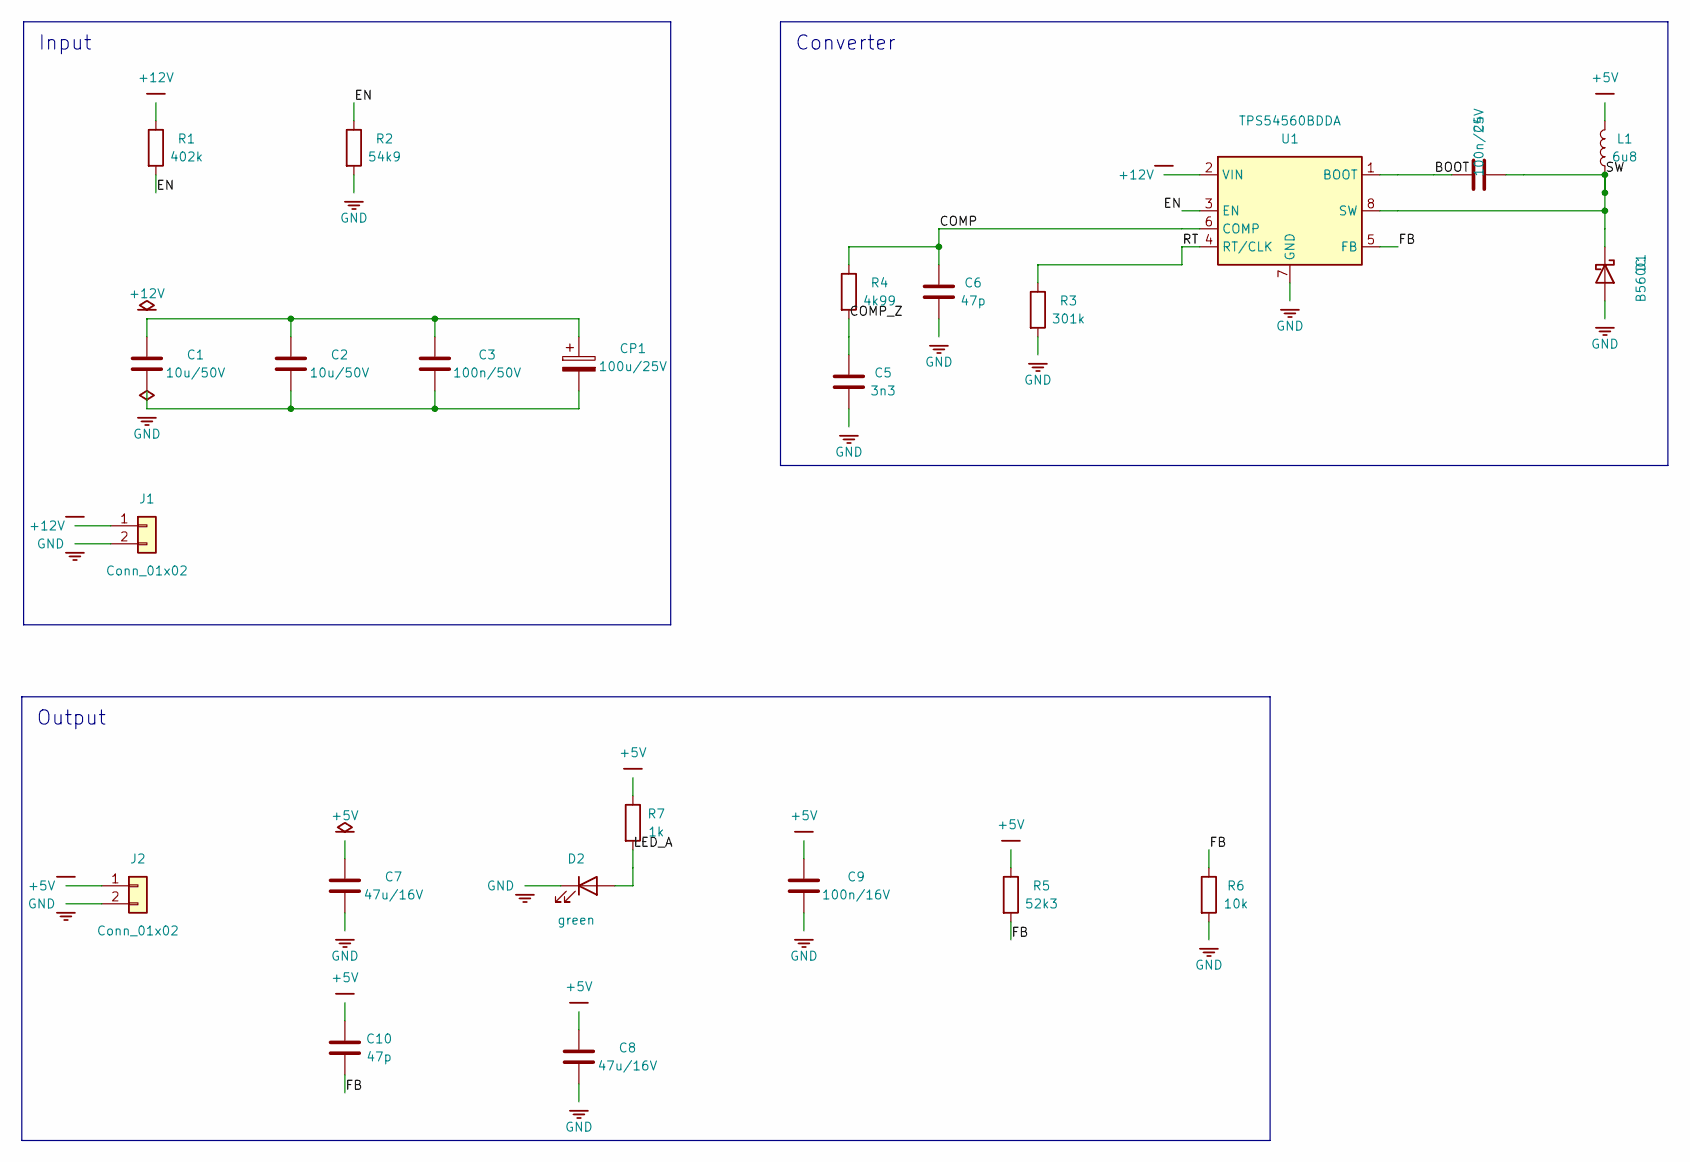
[picture p42: schematic buck-12v-5v.kicad_sch]

Parts:
C1, C2: 10u/50V; C_1210_3225Metric
C3: 100n/50V; C_0603_1608Metric
C4: 100n/25V; C_0603_1608Metric
C5: 3n3; C_0603_1608Metric
C6, C10: 47p; C_0603_1608Metric
C7, C8: 47u/16V; C_1210_3225Metric
C9: 100n/16V; C_0603_1608Metric
CP1: 100u/25V; CP_Elec_8x10.5
D1: B560C; D_SMC
D2: green; LED_0603_1608Metric
J1, J2: Conn_01x02; TerminalBlock_Phoenix_MKDS-1,5-2-5.08_1x02_P5.08mm_Horizont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
L1: 6u8; L_Bourns_SRP1245A
R1: 402k; R_0603_1608Metric
R2: 54k9; R_0603_1608Metric
R3: 301k; R_0603_1608Metric
R4: 4k99; R_0603_1608Metric
R5: 52k3; R_0603_1608Metric
R6: 10k; R_0603_1608Metric
R7: 1k; R_0603_1608Metric
U1: TPS54560BDDA; Texas_R-PDSO-G8_EP2.95x4.9mm_Mask2.4x3.1mm_ThermalVias

Connections:
+5V: C7.1, C8.1, C9.1, C10.1, J2.1, L1.2, R5.1, R7.1
+12V: C1.1, C2.1, C3.1, CP1.1, J1.1, R1.1, U1.2 (VIN)
BOOT: C4.1, U1.1 (BOOT)
COMP: C6.1, R4.1, U1.6 (COMP)
COMP_Z: C5.1, R4.2
EN: R1.2, R2.1, U1.3 (EN)
FB: C10.2, R5.2, R6.1, U1.5 (FB)
GND: C1.2, C2.2, C3.2, C5.2, C6.2, C7.2, C8.2, C9.2, CP1.2, D1.2 (A), D2.1 (K), J1.2, J2.2, R2.2, R3.2, R6.2, U1.7 (GND), U1.9 (GND)
LED_A: D2.2 (A), R7.2
RT: R3.1, U1.4 (RT/CLK)
SW: C4.2, D1.1 (K), L1.1, U1.8 (SW)

Notes on the sheet:
Converter
Input
Output
