copperheadhq/copperhead/manual-tests/reference-boards/ldo-demo/reference/ldo-demo.kicad_sch

## KiCad design manual-tests/reference-boards/ldo-demo/reference/ldo-demo.kicad_sch (2026-09-05)

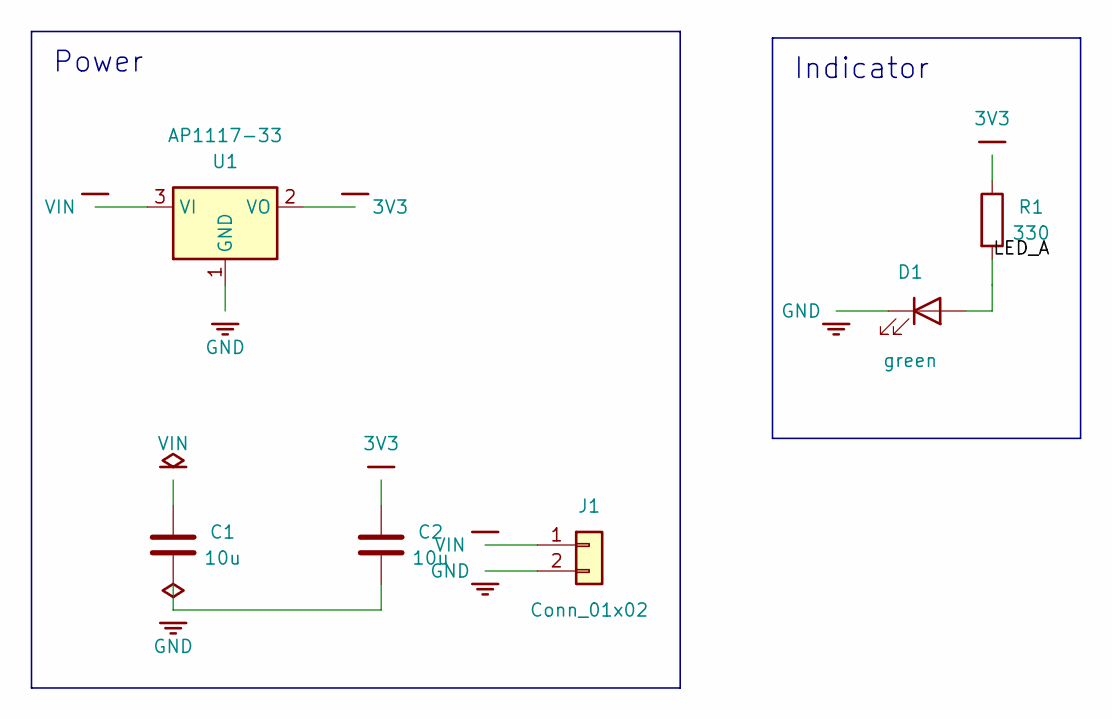
[picture p43: schematic ldo-demo.kicad_sch]

Parts:
C1, C2: 10u; C_0805_2012Metric
D1: green; LED_0603_1608Metric
J1: Conn_01x02; PinHeader_1x02_P2.54mm_Vertical
R1: 330; R_0603_1608Metric
U1: AP1117-33; SOT-223-3_TabPin2

Connections:
3V3: C2.1, R1.1, U1.2 (VO)
GND: C1.2, C2.2, D1.1 (K), J1.2, U1.1 (GND)
LED_A: D1.2 (A), R1.2
VIN: C1.1, J1.1, U1.3 (VI)

Notes on the sheet:
Indicator
Power
