copperheadhq/copperhead/manual-tests/reference-boards/npn-switch/reference/npn-switch.kicad_sch

## KiCad design manual-tests/reference-boards/npn-switch/reference/npn-switch.kicad_sch (2026-09-05)

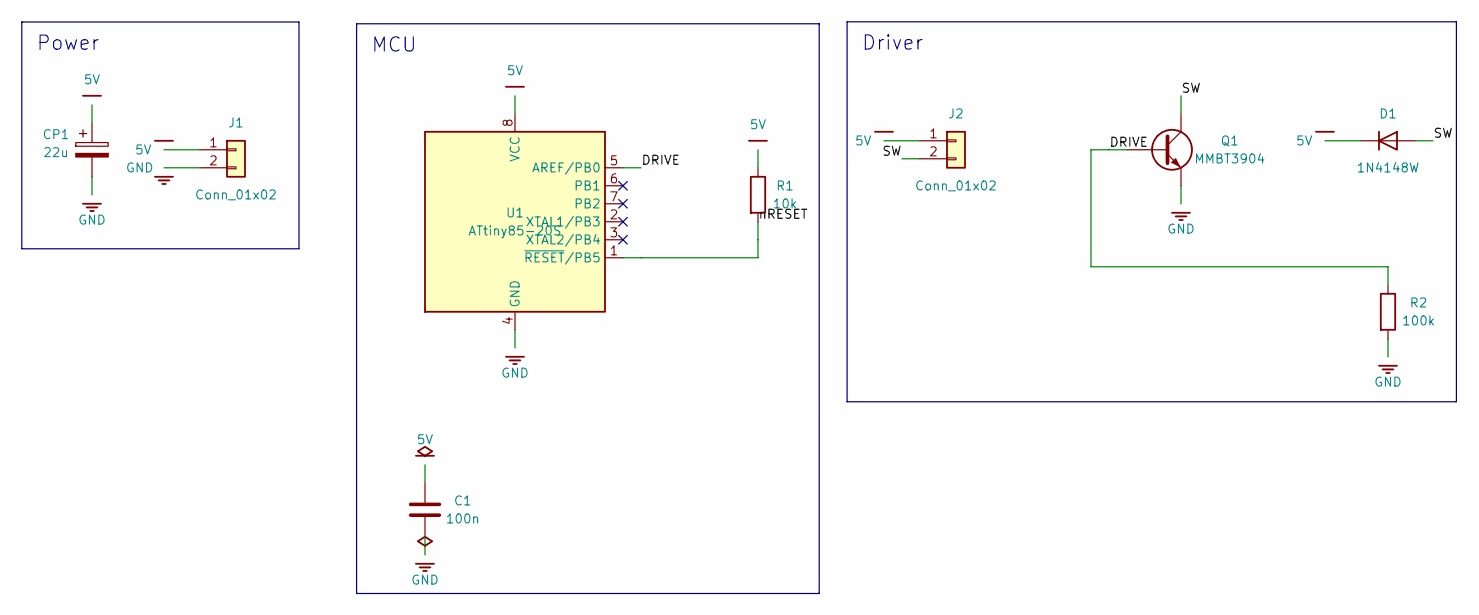
[picture p44: schematic npn-switch.kicad_sch]

Parts:
C1: 100n; C_0603_1608Metric
CP1: 22u; CP_Elec_4x4.5
D1: 1N4148W; D_SOD-123
J1, J2: Conn_01x02; PinHeader_1x02_P2.54mm_Vertical
Q1: MMBT3904; SOT-23
R1: 10k; R_0603_1608Metric
R2: 100k; R_0603_1608Metric
U1: ATtiny85-20S; SOIC-8_3.9x4.9mm_P1.27mm

Connections:
5V: C1.1, CP1.1, D1.1 (K), J1.1, J2.1, R1.1, U1.8 (VCC)
DRIVE: Q1.B, R2.1, U1.5 (AREF/PB0)
GND: C1.2, CP1.2, J1.2, Q1.E, R2.2, U1.4 (GND)
SW: D1.2 (A), J2.2, Q1.C
nRESET: R1.2, U1.1 (~RESET/PB5)

Notes on the sheet:
Driver
MCU
Power
