copperheadhq/copperhead/manual-tests/reference-boards/usb-atmega-node/reference/usb-atmega-node.kicad_sch

## KiCad design manual-tests/reference-boards/usb-atmega-node/reference/usb-atmega-node.kicad_sch (2026-09-05)

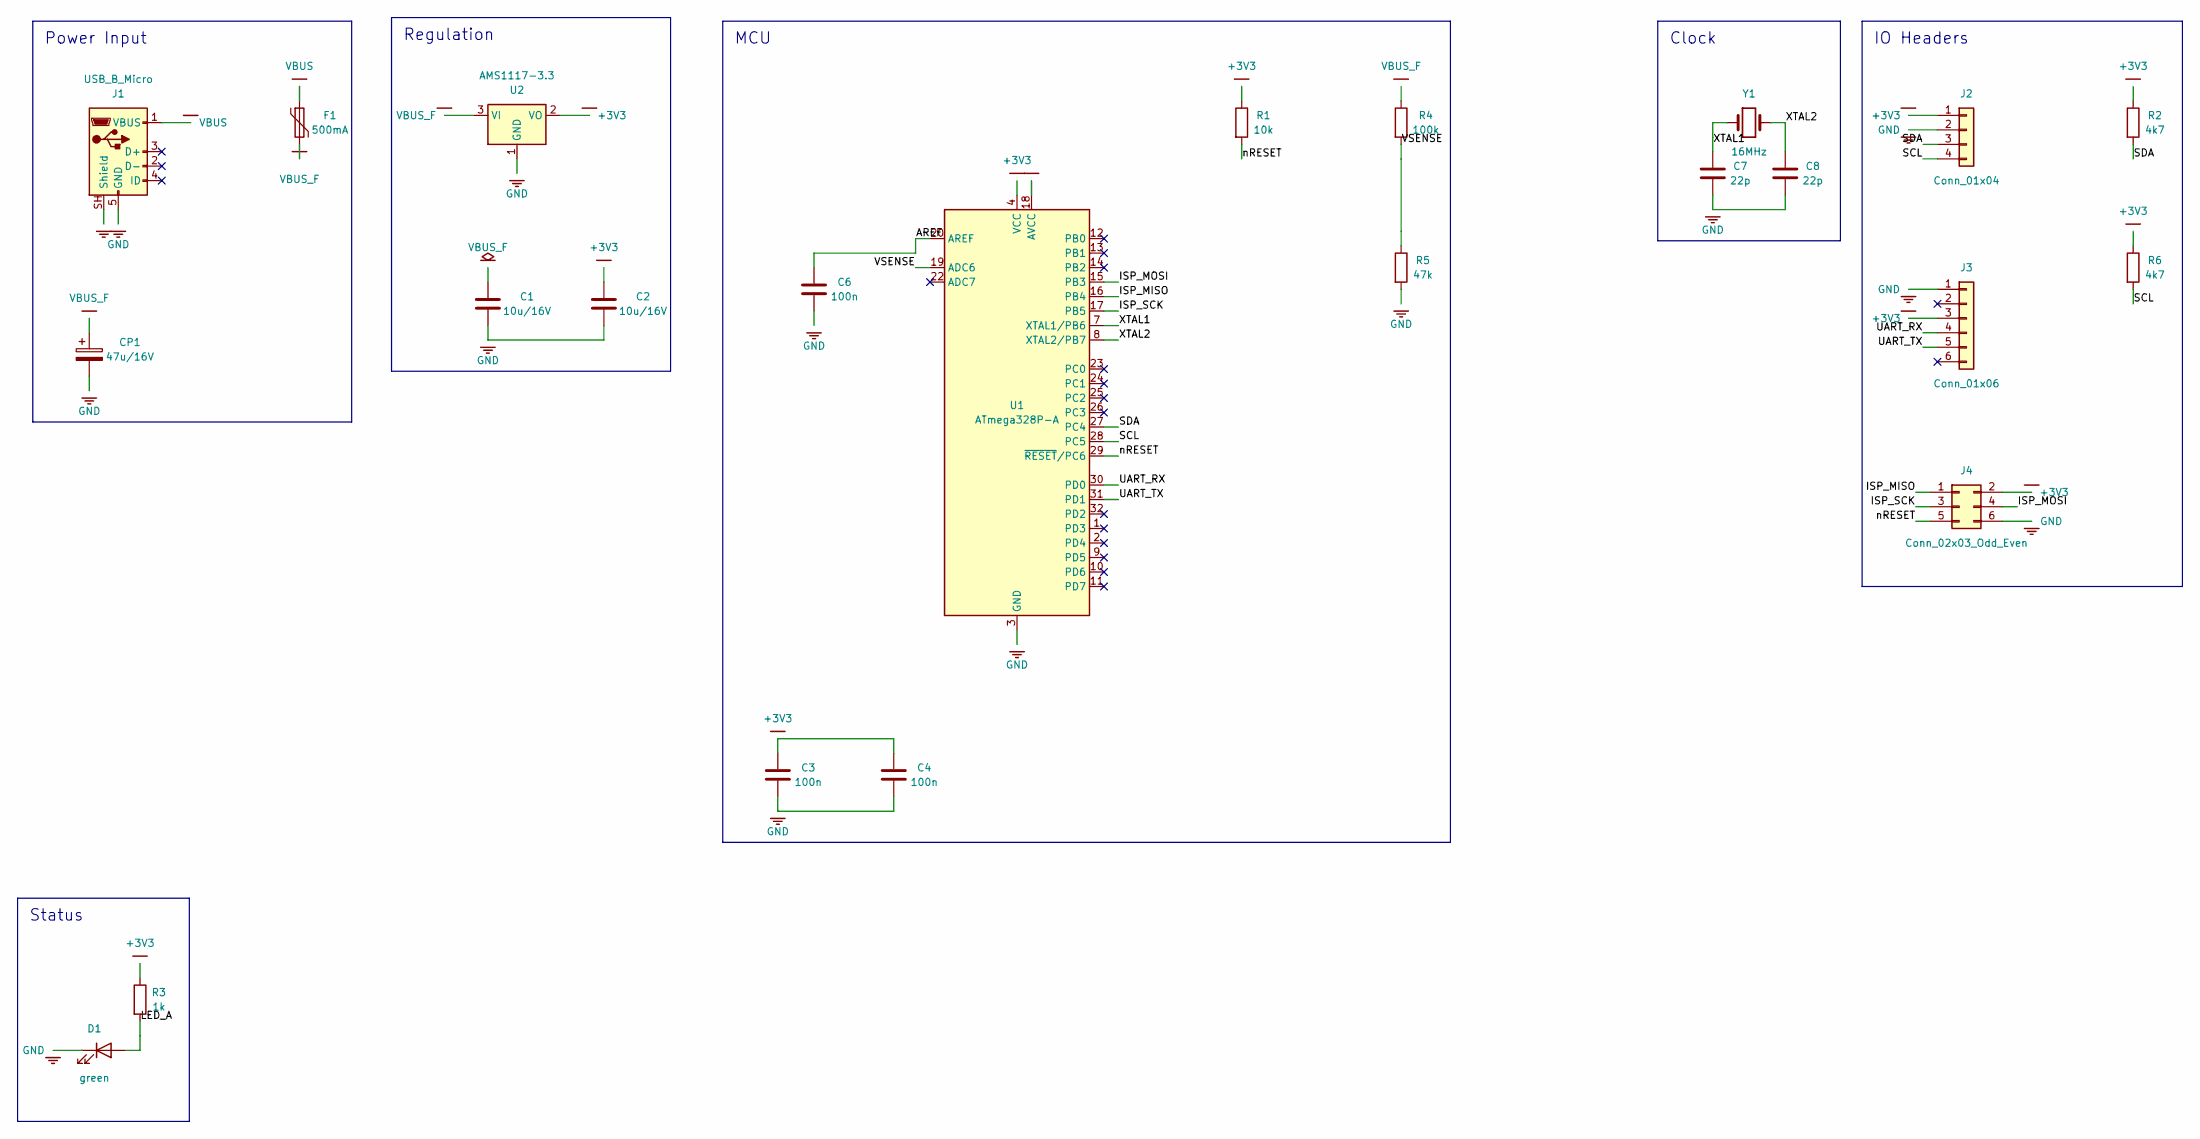
[picture p45: schematic usb-atmega-node.kicad_sch]

Parts:
C1, C2: 10u/16V; C_0805_2012Metric
C3, C4, C6: 100n; C_0603_1608Metric
C7, C8: 22p; C_0603_1608Metric
CP1: 47u/16V; CP_Elec_6.3x7.7
D1: green; LED_0603_1608Metric
F1: 500mA; Fuse_1206_3216Metric
J1: USB_B_Micro; USB_Micro-B_Amphenol_10118193-0001LF_Horizontal
J2: Conn_01x04; PinHeader_1x04_P2.54mm_Vertical
J3: Conn_01x06; PinHeader_1x06_P2.54mm_Vertical
J4: Conn_02x03_Odd_Even; PinHeader_2x03_P2.54mm_Vertical
R1: 10k; R_0603_1608Metric
R2, R6: 4k7; R_0603_1608Metric
R3: 1k; R_0603_1608Metric
R4: 100k; R_0603_1608Metric
R5: 47k; R_0603_1608Metric
U1: ATmega328P-A; TQFP-32_7x7mm_P0.8mm
U2: AMS1117-3.3; SOT-223-3_TabPin2
Y1: 16MHz; Crystal_SMD_HC49-SD

Connections:
+3V3: C2.1, C3.1, C4.1, J2.1, J3.3, J4.2, R1.1, R2.1, R3.1, R6.1, U1.4 (VCC), U1.6 (VCC), U1.18 (AVCC), U2.2 (VO)
AREF: C6.1, U1.20 (AREF)
GND: C1.2, C2.2, C3.2, C4.2, C6.2, C7.2, C8.2, CP1.2, D1.1 (K), J1.5 (GND), J1.SH (Shield), J2.2, J3.1, J4.6, R5.2, U1.3 (GND), U1.5 (GND), U1.21 (GND), U2.1 (GND)
ISP_MISO: J4.1, U1.16 (PB4)
ISP_MOSI: J4.4, U1.15 (PB3)
ISP_SCK: J4.3, U1.17 (PB5)
LED_A: D1.2 (A), R3.2
SCL: J2.4, R6.2, U1.28 (PC5)
SDA: J2.3, R2.2, U1.27 (PC4)
UART_RX: J3.4, U1.30 (PD0)
UART_TX: J3.5, U1.31 (PD1)
VBUS: F1.1, J1.1 (VBUS)
VBUS_F: C1.1, CP1.1, F1.2, R4.1, U2.3 (VI)
VSENSE: R4.2, R5.1, U1.19 (ADC6)
XTAL1: C7.1, U1.7 (XTAL1/PB6), Y1.1
XTAL2: C8.1, U1.8 (XTAL2/PB7), Y1.2
nRESET: J4.5, R1.2, U1.29 (~RESET/PC6)

Notes on the sheet:
Clock
IO Headers
MCU
Power Input
Regulation
Status
