copperheadhq/copperhead/manual-tests/real-designs/examples/cm5_minima/drawn/board.kicad_sch

## KiCad design manual-tests/real-designs/examples/cm5_minima/drawn/board.kicad_sch (2026-08-09)

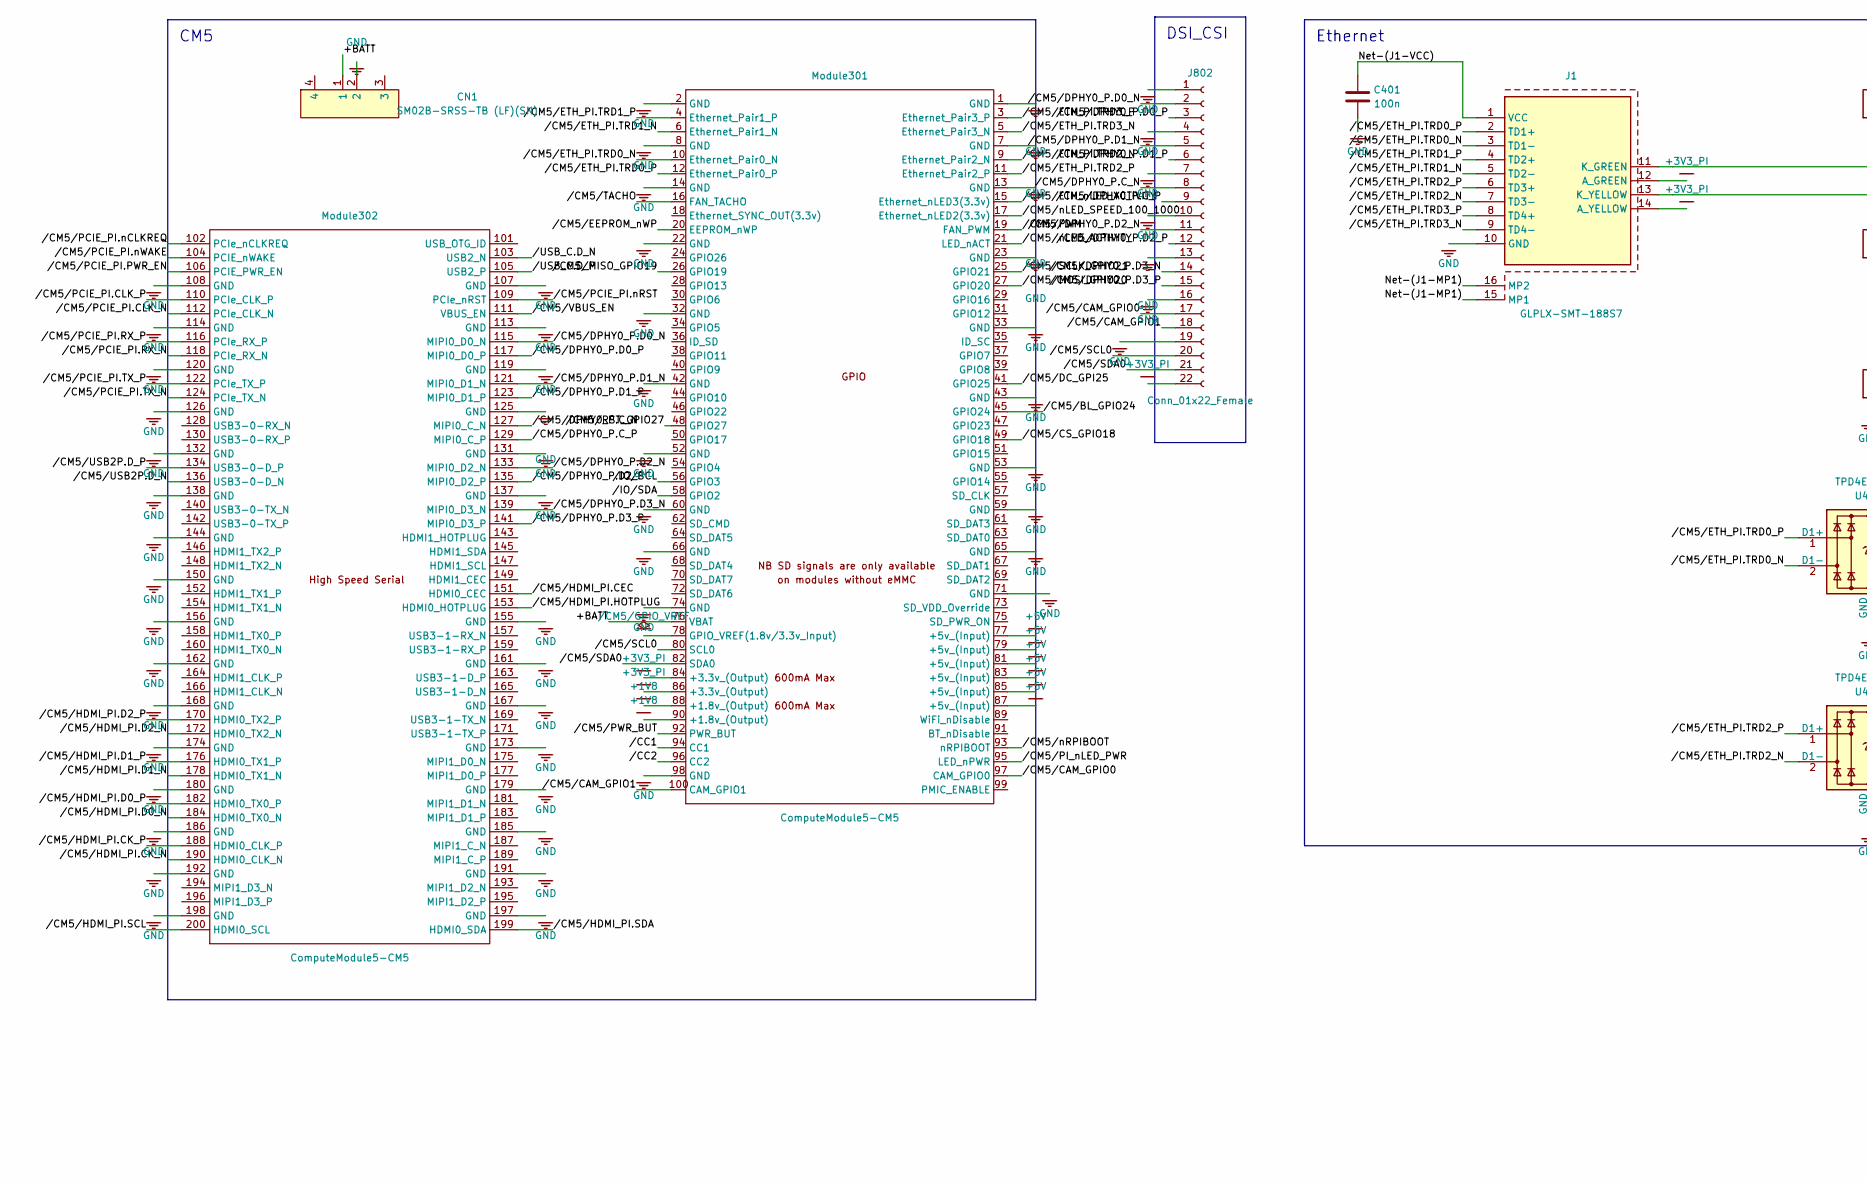
[picture p46: schematic board.kicad_sch, part in row 1, column 1]

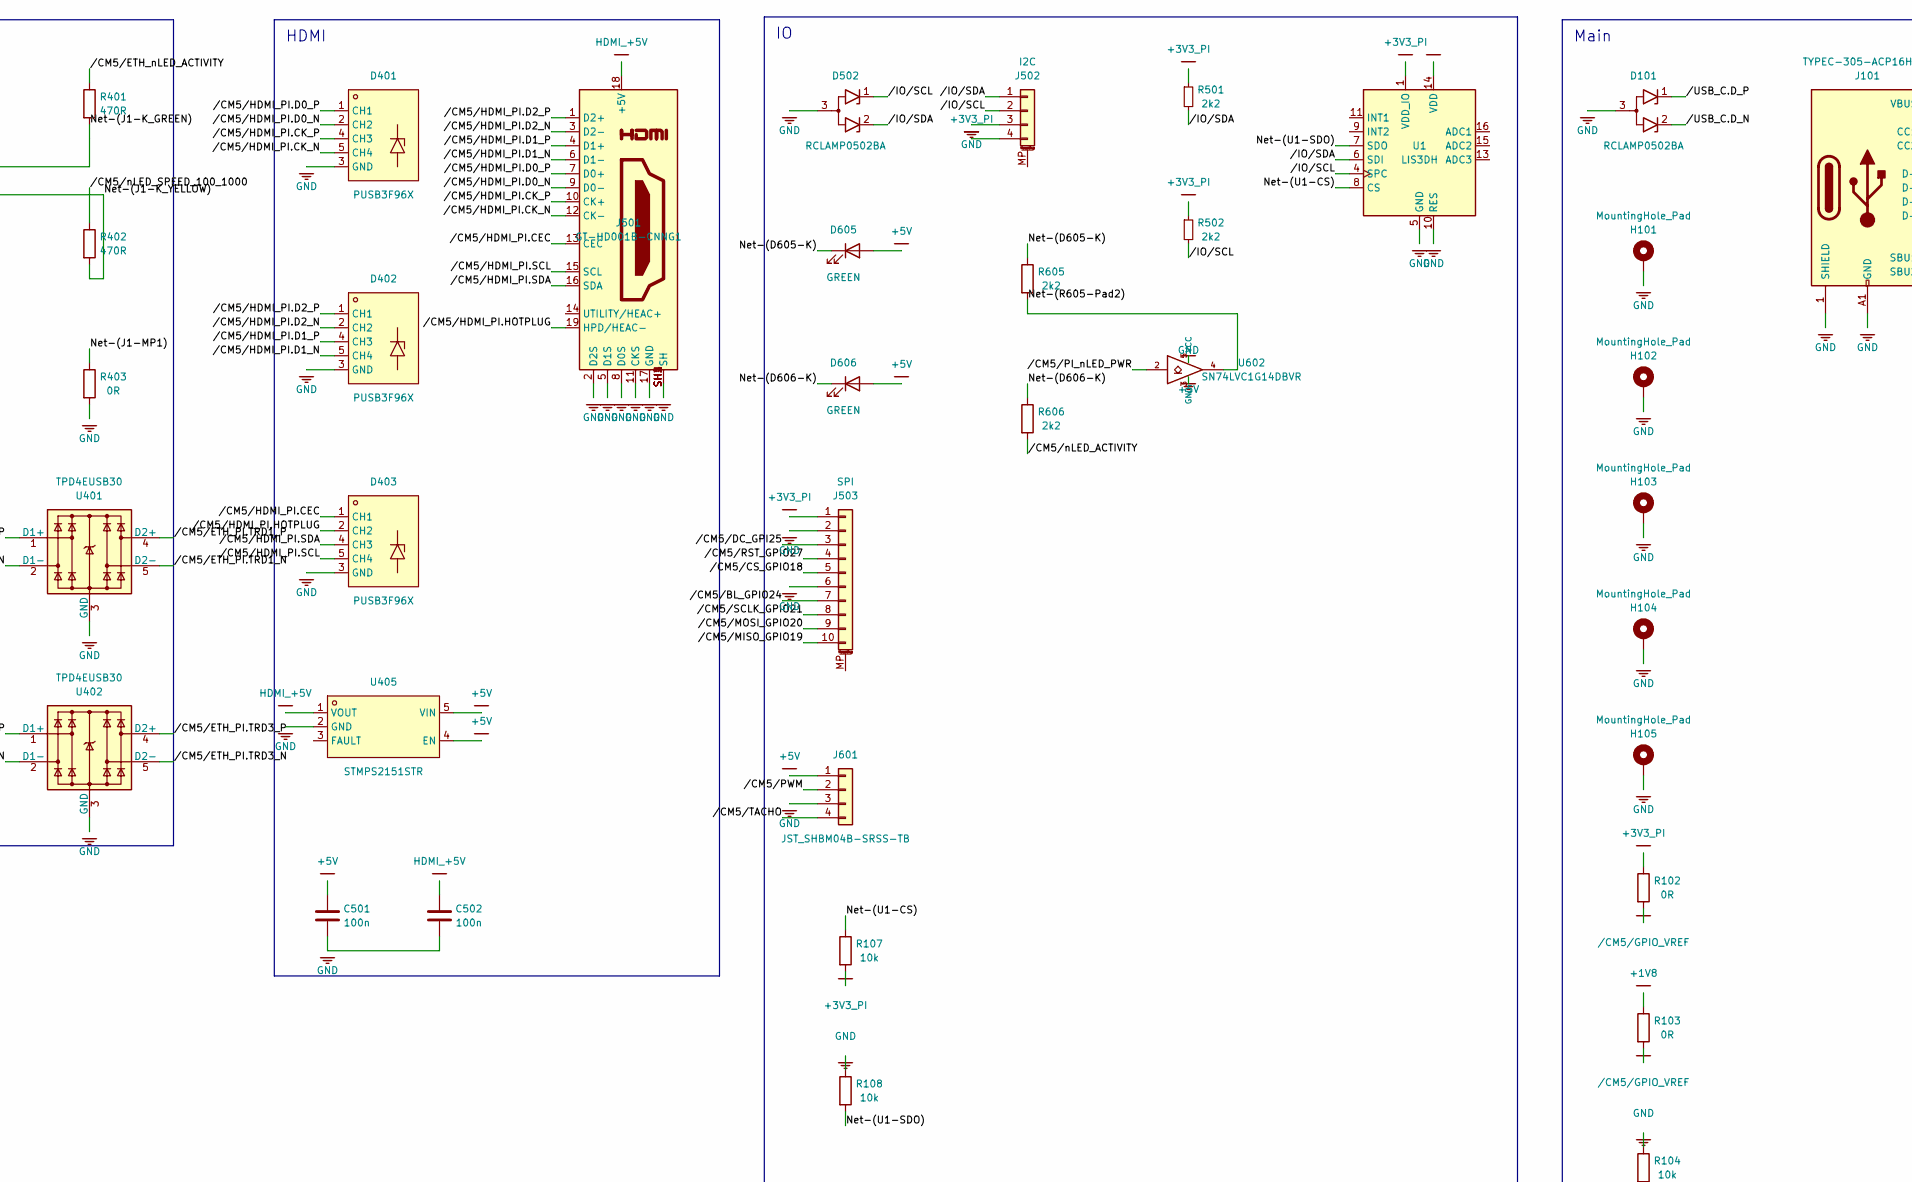
[picture p47: schematic board.kicad_sch, part in row 1, column 2]

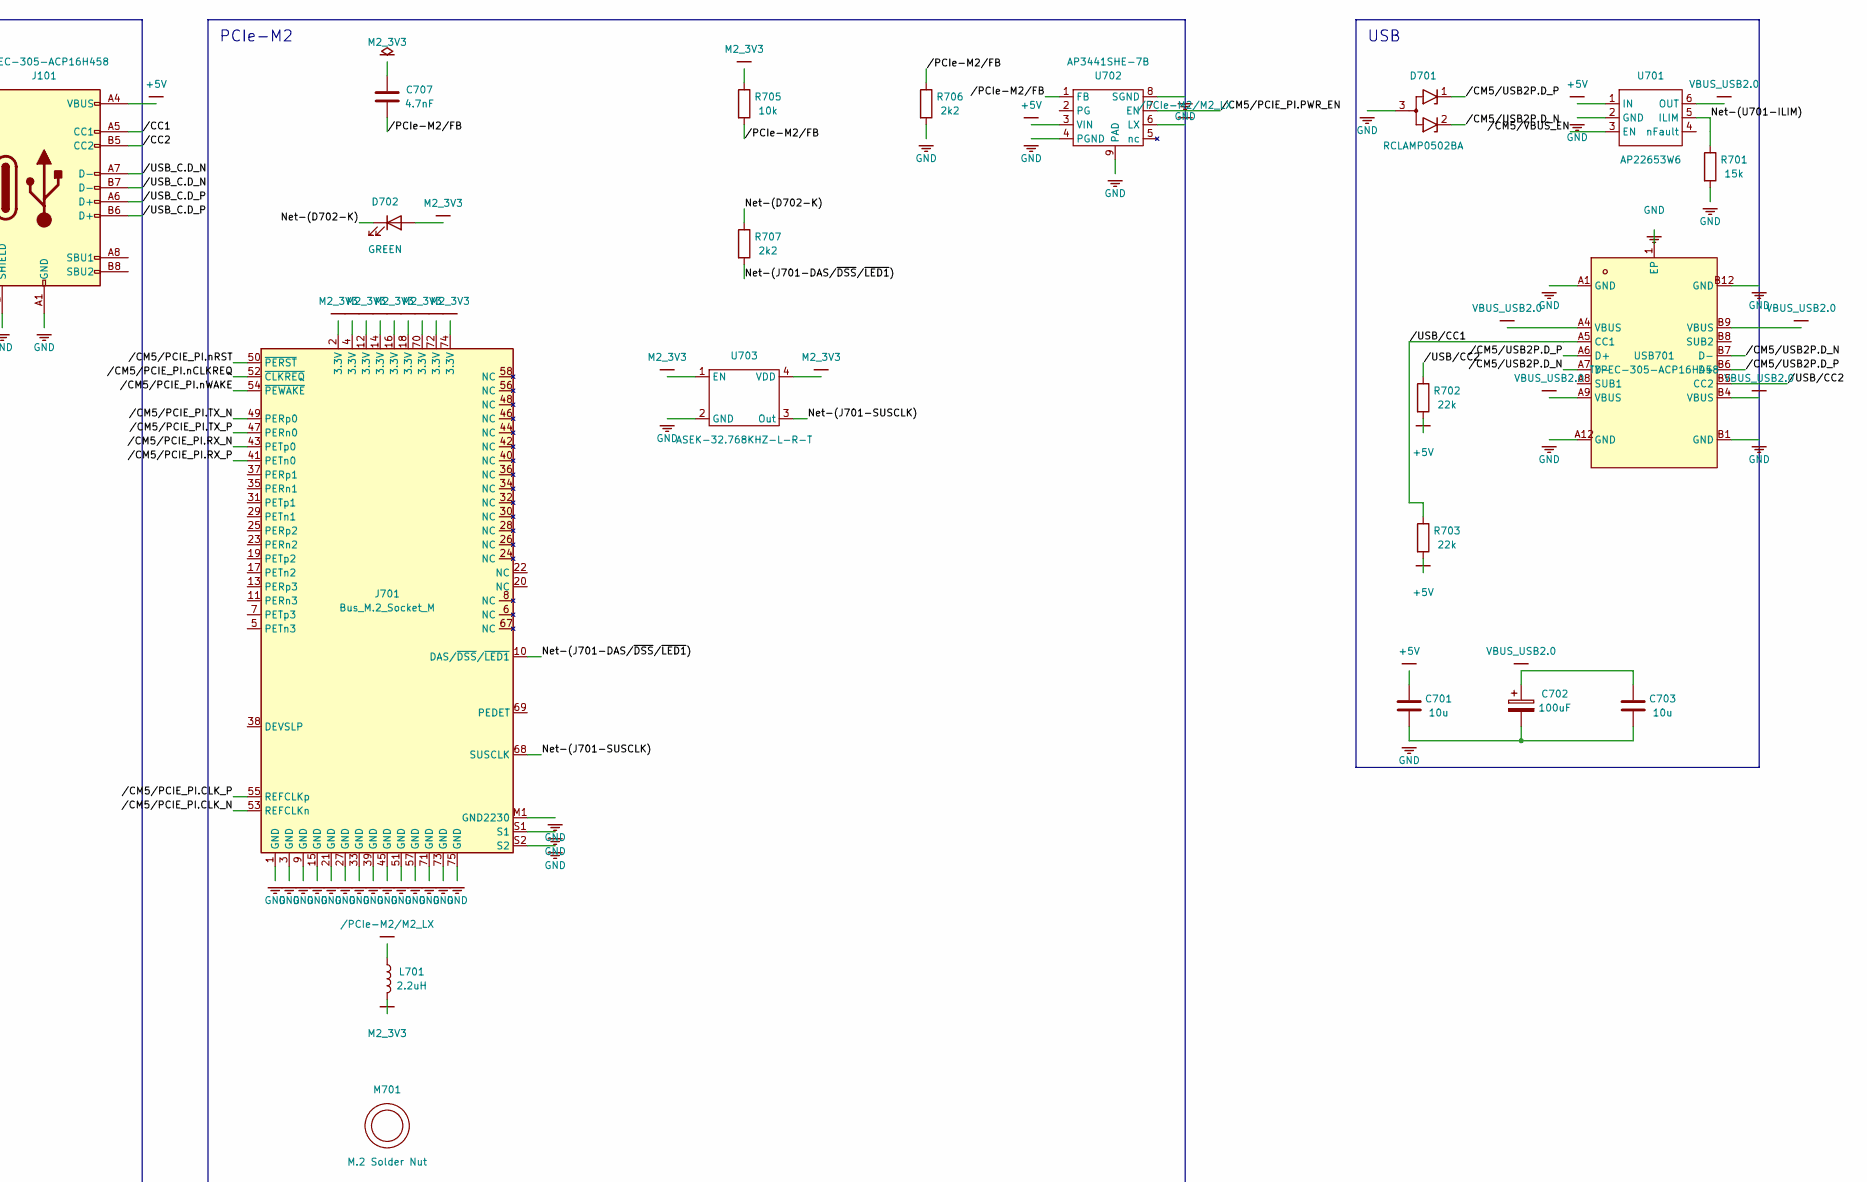
[picture p48: schematic board.kicad_sch, part in row 1, column 3]

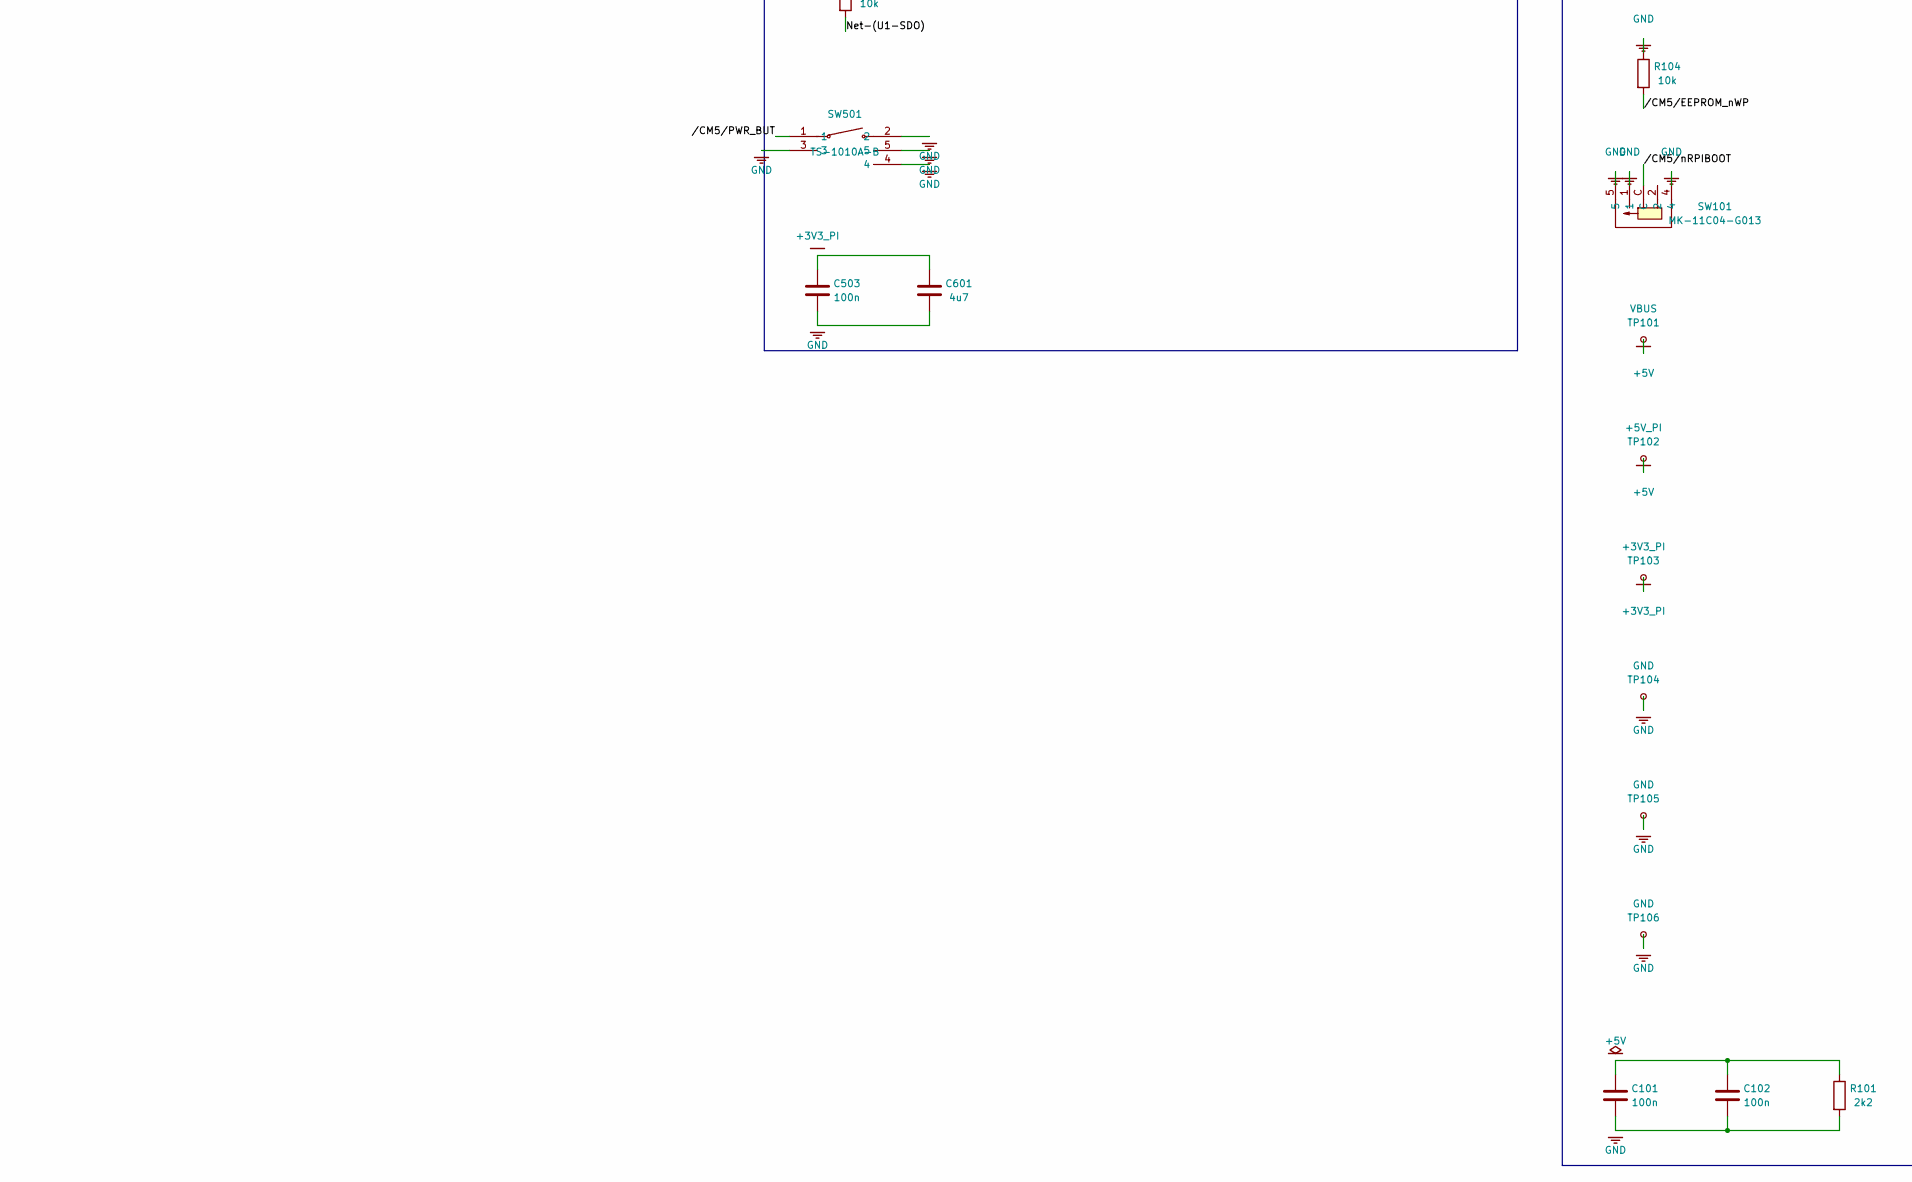
[picture p49: schematic board.kicad_sch, part in row 2, column 2]

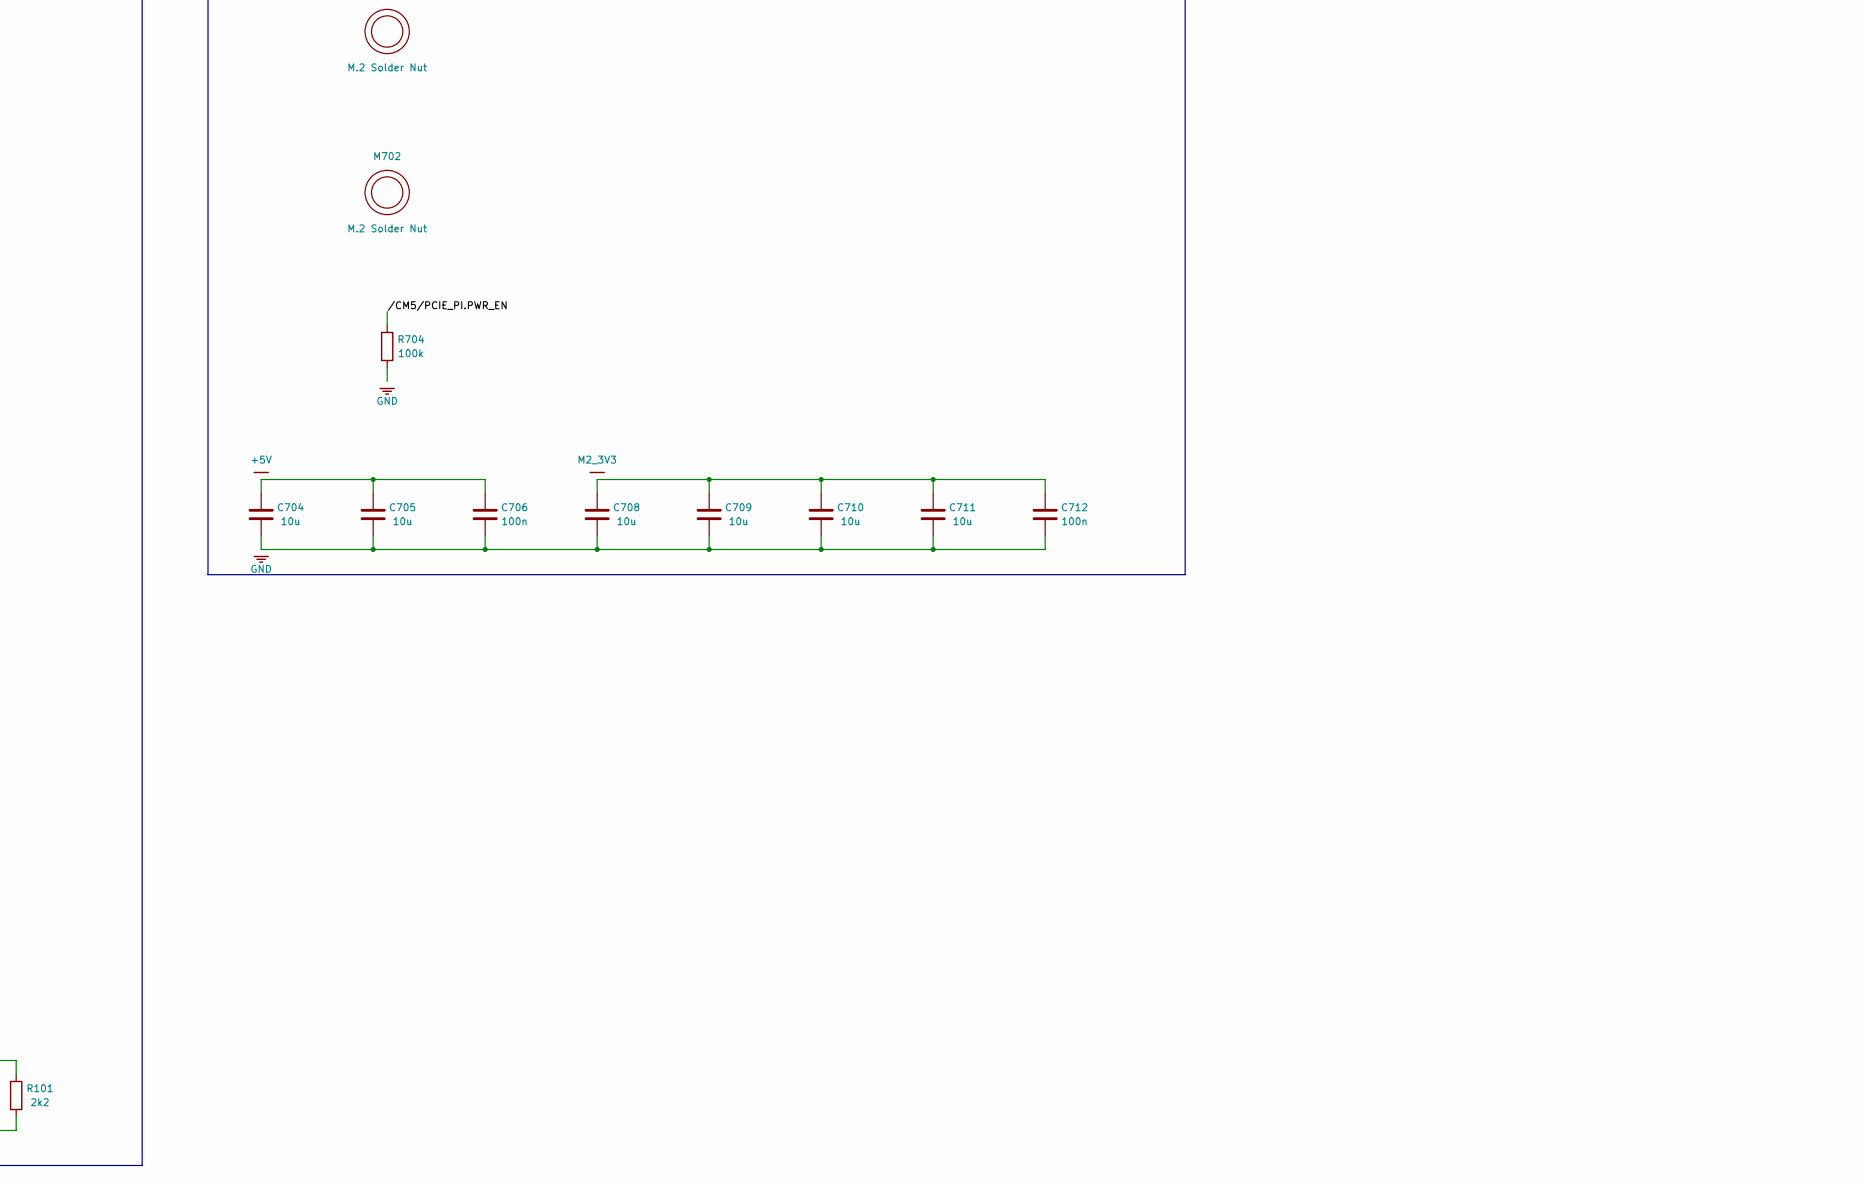
[picture p50: schematic board.kicad_sch, part in row 2, column 3]

Parts:
C101, C102, C401, C501, C502, C503, C706, C712: 100n; C_0402_1005Metric
C601: 4u7; C_0805_2012Metric
C701, C703, C704, C705, C708, C709, C710, C711: 10u; C_0805_2012Metric
C702: 100uF; CP_EIA-3528-21_Kemet-B
C707: 4.7nF; C_0402_1005Metric
CN1: SM02B-SRSS-TB (LF)(SN); CONN-SMD_2P-P1.00_SM02B-SRSS-TB-LF-SN
D101, D502, D701: RCLAMP0502BA; SOT-416
D401, D402, D403: PUSB3F96X; DFN2510A-10_L2.5-W1.0-P0.50-BL
D605, D606, D702: GREEN; LED-SMD_L1.7-W0.6-RD
H101: MountingHole_Pad; MountingHole_2.2mm_M2_DIN965_Pad_TopBottom
H102, H103, H104, H105: MountingHole_Pad; MountingHole_2.7mm_Pad
J1: GLPLX-SMT-188S7; GLPLXSMT188S7QQYG
J101: TYPEC-305-ACP16H458; USB-C-SMD_TYPEC-305-ACP16H458
J501: GT-HD001B-CNNG1; EDAC 690-019-298-412
J502: I2C; JST_SH_BM04B-SRSS-TB_1x04-1MP_P1.00mm_Vertical
J503: SPI; JST_SUR_BM10B-SURS-TF_1x10-1MP_P0.80mm_Vertical
J601: JST_SHBM04B-SRSS-TB; JST_SH_BM04B-SRSS-TB_1x04-1MP_P1.00mm_Vertical
J701: Bus_M.2_Socket_M; M.2 M Key socket_2230_2242
J802: Conn_01x22_Female; Hirose_FH12-22S-0.5SH_1x22-1MP_P0.50mm_Horizontal
L701: 2.2uH; L_Coilcraft_XAL5030-XXX
M701, M702: M.2 Solder Nut; MountingHole_3mm_Pad
Module301: ComputeModule5-CM5; Raspberry-Pi-5-Compute-Module_GPIO
Module302: ComputeModule5-CM5; Raspberry-Pi-5-Compute-Module_HSS
R101, R501, R502, R605, R606, R706, R707: 2k2; R_0402_1005Metric
R102, R103, R403: 0R; R_0402_1005Metric
R104, R107, R108, R705: 10k; R_0402_1005Metric
R401, R402: 470R; R_0402_1005Metric
R701: 15k; R_0402_1005Metric
R702, R703: 22k; R_0402_1005Metric
R704: 100k; R_0402_1005Metric
SW101: MK-11C04-G013; SW-SMD_MK-11C04-G013
SW501: TS-1010A-B; SW-SMD_TS-1010A-B
TP101: VBUS; TestPoint_Pad_D1.0mm
TP102: +5V_PI; TestPoint_Pad_D1.0mm
TP103: +3V3_PI; TestPoint_Pad_D1.0mm
TP104, TP105, TP106: GND; TestPoint_THTPad_D1.0mm_Drill0.5mm
U1: LIS3DH; LGA-16_3x3mm_P0.5mm_LayoutBorder3x5y
U401, U402: TPD4EUSB30; USON-10_2.5x1.0mm_P0.5mm
U405: STMPS2151STR; SOT-23-5
U602: SN74LVC1G14DBVR; SOT-353_SC-70-5
U701: AP22653W6; SOT-23-6
U702: AP3441SHE-7B; DFN-8-1EP_2x2mm_P0.5mm_EP1.05x1.75mm
U703: ASEK-32.768KHZ-L-R-T; Crystal_SMD_3225-4Pin_3.2x2.5mm
USB701: TYPEC-305-ACP16H458; USB-C-SMD_TYPEC-305-ACP16H458

Connections:
+1V8: Module301.88 (+1.8v_(Output)), Module301.90 (+1.8v_(Output)), R103.1
+3V3_PI: C503.1, C601.1, J1.12 (A_GREEN), J1.14 (A_YELLOW), J502.4, J503.1, J802.22, Module301.84 (+3.3v_(Output)), Module301.86 (+3.3v_(Output)), R102.1, R107.2, R501.1, R502.1, TP103.1, U1.1 (VDD_IO), U1.14 (VDD)
+5V: C101.1, C102.1, C501.1, C701.1, C704.1, C705.1, C706.1, D605.2 (A), D606.2 (A), J101.A4 (VBUS), J101.A9 (VBUS), J101.B4 (VBUS), J101.B9 (VBUS), J601.1, Module301.77 (+5v_(Input)), Module301.79 (+5v_(Input)), Module301.81 (+5v_(Input)), Module301.83 (+5v_(Input)), Module301.85 (+5v_(Input)), Module301.87 (+5v_(Input)), R101.1, R702.2, R703.2, TP101.1, TP102.1, U405.4 (EN), U405.5 (VIN), U602.5 (VCC), U701.1 (IN), U702.3 (VIN)
+BATT: CN1.1, Module301.76 (VBAT)
/CC1: J101.A5 (CC1), Module301.94 (CC1)
/CC2: J101.B5 (CC2), Module301.96 (CC2)
/CM5/BL_GPIO24: J503.7, Module301.45 (GPIO24)
/CM5/CAM_GPIO0: J802.17, Module301.97 (CAM_GPIO0)
/CM5/CAM_GPIO1: J802.18, Module301.100 (CAM_GPIO1)
/CM5/CS_GPIO18: J503.5, Module301.49 (GPIO18)
/CM5/DC_GPI25: J503.3, Module301.41 (GPIO25)
/CM5/DPHY0_P.C_N: J802.8, Module302.127 (MIPI0_C_N)
/CM5/DPHY0_P.C_P: J802.9, Module302.129 (MIPI0_C_P)
/CM5/DPHY0_P.D0_N: J802.2, Module302.115 (MIPI0_D0_N)
/CM5/DPHY0_P.D0_P: J802.3, Module302.117 (MIPI0_D0_P)
/CM5/DPHY0_P.D1_N: J802.5, Module302.121 (MIPI0_D1_N)
/CM5/DPHY0_P.D1_P: J802.6, Module302.123 (MIPI0_D1_P)
/CM5/DPHY0_P.D2_N: J802.11, Module302.133 (MIPI0_D2_N)
/CM5/DPHY0_P.D2_P: J802.12, Module302.135 (MIPI0_D2_P)
/CM5/DPHY0_P.D3_N: J802.14, Module302.139 (MIPI0_D3_N)
/CM5/DPHY0_P.D3_P: J802.15, Module302.141 (MIPI0_D3_P)
/CM5/EEPROM_nWP: Module301.20 (EEPROM_nWP), R104.2
/CM5/ETH_PI.TRD0_N: J1.3 (TD1-), Module301.10 (Ethernet_Pair0_N), U401.2 (D1-), U401.9
/CM5/ETH_PI.TRD0_P: J1.2 (TD1+), Module301.12 (Ethernet_Pair0_P), U401.1 (D1+), U401.10
/CM5/ETH_PI.TRD1_N: J1.5 (TD2-), Module301.6 (Ethernet_Pair1_N), U401.5 (D2-), U401.6
/CM5/ETH_PI.TRD1_P: J1.4 (TD2+), Module301.4 (Ethernet_Pair1_P), U401.4 (D2+), U401.7
/CM5/ETH_PI.TRD2_N: J1.7 (TD3-), Module301.9 (Ethernet_Pair2_N), U402.2 (D1-), U402.9
/CM5/ETH_PI.TRD2_P: J1.6 (TD3+), Module301.11 (Ethernet_Pair2_P), U402.1 (D1+), U402.10
/CM5/ETH_PI.TRD3_N: J1.9 (TD4-), Module301.5 (Ethernet_Pair3_N), U402.5 (D2-), U402.6
/CM5/ETH_PI.TRD3_P: J1.8 (TD4+), Module301.3 (Ethernet_Pair3_P), U402.4 (D2+), U402.7
/CM5/ETH_nLED_ACTIVITY: Module301.15 (Ethernet_nLED3(3.3v)), R401.1
/CM5/GPIO_VREF: Module301.78 (GPIO_VREF(1.8v/3.3v_Input)), R102.2, R103.2
/CM5/HDMI_PI.CEC: D403.1 (CH1), D403.10 (NC), J501.13 (CEC), Module302.151 (HDMI0_CEC)
/CM5/HDMI_PI.CK_N: D401.5 (CH4), D401.6 (NC), J501.12 (CK-), Module302.190 (HDMI0_CLK_N)
/CM5/HDMI_PI.CK_P: D401.4 (CH3), D401.7 (NC), J501.10 (CK+), Module302.188 (HDMI0_CLK_P)
/CM5/HDMI_PI.D0_N: D401.2 (CH2), D401.9 (NC), J501.9 (D0-), Module302.184 (HDMI0_TX0_N)
/CM5/HDMI_PI.D0_P: D401.1 (CH1), D401.10 (NC), J501.7 (D0+), Module302.182 (HDMI0_TX0_P)
/CM5/HDMI_PI.D1_N: D402.5 (CH4), D402.6 (NC), J501.6 (D1-), Module302.178 (HDMI0_TX1_N)
/CM5/HDMI_PI.D1_P: D402.4 (CH3), D402.7 (NC), J501.4 (D1+), Module302.176 (HDMI0_TX1_P)
/CM5/HDMI_PI.D2_N: D402.2 (CH2), D402.9 (NC), J501.3 (D2-), Module302.172 (HDMI0_TX2_N)
/CM5/HDMI_PI.D2_P: D402.1 (CH1), D402.10 (NC), J501.1 (D2+), Module302.170 (HDMI0_TX2_P)
/CM5/HDMI_PI.HOTPLUG: D403.2 (CH2), D403.9 (NC), J501.19 (HPD/HEAC-), Module302.153 (HDMI0_HOTPLUG)
/CM5/HDMI_PI.SCL: D403.5 (CH4), D403.6 (NC), J501.15 (SCL), Module302.200 (HDMI0_SCL)
/CM5/HDMI_PI.SDA: D403.4 (CH3), D403.7 (NC), J501.16 (SDA), Module302.199 (HDMI0_SDA)
/CM5/MISO_GPIO19: J503.10, Module301.26 (GPIO19)
/CM5/MOSI_GPIO20: J503.9, Module301.27 (GPIO20)
/CM5/PCIE_PI.CLK_N: J701.53 (REFCLKn), Module302.112 (PCIe_CLK_N)
/CM5/PCIE_PI.CLK_P: J701.55 (REFCLKp), Module302.110 (PCIe_CLK_P)
/CM5/PCIE_PI.PWR_EN: Module302.106 (PCIE_PWR_EN), R704.1, U702.7 (EN)
/CM5/PCIE_PI.RX_N: J701.43 (PETp0), Module302.118 (PCIe_RX_N)
/CM5/PCIE_PI.RX_P: J701.41 (PETn0), Module302.116 (PCIe_RX_P)
/CM5/PCIE_PI.TX_N: J701.49 (PERp0), Module302.124 (PCIe_TX_N)
/CM5/PCIE_PI.TX_P: J701.47 (PERn0), Module302.122 (PCIe_TX_P)
/CM5/PCIE_PI.nCLKREQ: J701.52 (~CLKREQ), Module302.102 (PCIe_nCLKREQ)
/CM5/PCIE_PI.nRST: J701.50 (~PERST), Module302.109 (PCIe_nRST)
/CM5/PCIE_PI.nWAKE: J701.54 (~PEWAKE), Module302.104 (PCIE_nWAKE)
/CM5/PI_nLED_PWR: Module301.95 (LED_nPWR), U602.2
/CM5/PWM: J601.2, Module301.19 (FAN_PWM)
/CM5/PWR_BUT: Module301.92 (PWR_BUT), SW501.1
/CM5/RST_GPIO27: J503.4, Module301.48 (GPIO27)
/CM5/SCL0: J802.20, Module301.80 (SCL0)
/CM5/SCLK_GPIO21: J503.8, Module301.25 (GPIO21)
/CM5/SDA0: J802.21, Module301.82 (SDA0)
/CM5/TACHO: J601.4, Module301.16 (FAN_TACHO)
/CM5/USB2P.D_N: D701.2 (K2), Module302.136 (USB3-0-D_N), USB701.A7 (D-), USB701.B7 (D-)
/CM5/USB2P.D_P: D701.1 (K1), Module302.134 (USB3-0-D_P), USB701.A6 (D+), USB701.B6 (D+)
/CM5/VBUS_EN: Module302.111 (VBUS_EN), U701.3 (EN)
/CM5/nLED_ACTIVITY: Module301.21 (LED_nACT), R606.2
/CM5/nLED_SPEED_100_1000: Module301.17 (Ethernet_nLED2(3.3v)), R402.1
/CM5/nRPIBOOT: Module301.93 (nRPIBOOT), SW101.C
/IO/SCL: D502.1 (K1), J502.2, Module301.56 (GPIO3), R502.2, U1.4 (SPC)
/IO/SDA: D502.2 (K2), J502.1, Module301.58 (GPIO2), R501.2, U1.6 (SDI)
/PCIe-M2/FB: C707.2, R705.2, R706.1, U702.1 (FB)
/PCIe-M2/M2_LX: L701.1, U702.6 (LX)
/USB/CC1: R703.1, USB701.A5 (CC1)
/USB/CC2: R702.1, USB701.B5 (CC2)
/USB_C.D_N: D101.2 (K2), J101.A7 (D-), J101.B7 (D-), Module302.103 (USB2_N)
/USB_C.D_P: D101.1 (K1), J101.A6 (D+), J101.B6 (D+), Module302.105 (USB2_P)
GND: C101.2, C102.2, C401.2, C501.2, C502.2, C503.2, C601.2, C701.2, C702.2, C703.2, C704.2, C705.2, C706.2, C708.2, C709.2, C710.2, C711.2, C712.2, CN1.2, D101.3 (A), D401.3 (GND), D401.8 (GND), D402.3 (GND), D402.8 (GND), D403.3 (GND), D403.8 (GND), D502.3 (A), D701.3 (A), H101.1, H102.1, H103.1, H104.1, H105.1, J1.10 (GND), J101.1 (SHIELD), J101.A1 (GND), J101.A12 (GND), J101.B1 (GND), J101.B12 (GND), J501.2 (D2S), J501.5 (D1S), J501.8 (D0S), J501.11 (CKS), J501.17 (GND), J501.SH1 (SH), J501.SH2 (SH), J501.SH3 (SH), J501.SH4 (SH), J502.3, J503.2, J503.6, J601.3, J701.1 (GND), J701.3 (GND), J701.9 (GND), J701.15 (GND), J701.21 (GND), J701.27 (GND), J701.33 (GND), J701.39 (GND), J701.45 (GND), J701.51 (GND), J701.57 (GND), J701.71 (GND), J701.73 (GND), J701.75 (GND), J701.M1 (GND2230), J701.S1, J701.S2, J802.1, J802.4, J802.7, J802.10, J802.13, J802.16, J802.19, Module301.1 (GND), Module301.2 (GND), Module301.7 (GND), Module301.8 (GND), Module301.13 (GND), Module301.14 (GND), Module301.22 (GND), Module301.23 (GND), Module301.32 (GND), Module301.33 (GND), Module301.42 (GND), Module301.43 (GND), Module301.52 (GND), Module301.53 (GND), Module301.59 (GND), Module301.60 (GND), Module301.65 (GND), Module301.66 (GND), Module301.71 (GND), Module301.74 (GND), Module301.98 (GND), Module302.107 (GND), Module302.108 (GND), Module302.113 (GND), Module302.114 (GND), Module302.119 (GND), Module302.120 (GND), Module302.125 (GND), Module302.126 (GND), Module302.131 (GND), Module302.132 (GND), Module302.137 (GND), Module302.138 (GND), Module302.144 (GND), Module302.150 (GND), Module302.155 (GND), Module302.156 (GND), Module302.161 (GND), Module302.162 (GND), Module302.167 (GND), Module302.168 (GND), Module302.173 (GND), Module302.174 (GND), Module302.179 (GND), Module302.180 (GND), Module302.185 (GND), Module302.186 (GND), Module302.191 (GND), Module302.192 (GND), Module302.197 (GND), Module302.198 (GND), R101.2, R104.1, R108.1, R403.2, R701.2, R704.2, R706.2, SW101.1, SW101.4, SW101.5, SW501.2, SW501.3, SW501.4, SW501.5, TP104.1, TP105.1, TP106.1, U1.5 (GND), U1.10 (RES), U1.12 (GND), U401.3 (GND), U401.8 (GND), U402.3 (GND), U402.8 (GND), U405.2 (GND), U602.3 (GND), U701.2 (GND), U702.4 (PGND), U702.8 (SGND), U702.9 (PAD), U703.2 (GND), USB701.1 (EP), USB701.A1 (GND), USB701.A12 (GND), USB701.B1 (GND), USB701.B12 (GND)
HDMI_+5V: C502.1, J501.18 (+5V), U405.1 (VOUT)
M2_3V3: C707.1, C708.1, C709.1, C710.1, C711.1, C712.1, D702.2 (A), J701.2 (3.3V), J701.4 (3.3V), J701.12 (3.3V), J701.14 (3.3V), J701.16 (3.3V), J701.18 (3.3V), J701.70 (3.3V), J701.72 (3.3V), J701.74 (3.3V), L701.2, R705.1, U703.1 (EN), U703.4 (VDD)
unnamed: D605.1 (K), R605.1
unnamed: D606.1 (K), R606.1
unnamed: D702.1 (K), R707.1
unnamed: J1.11 (K_GREEN), R401.2
unnamed: J1.13 (K_YELLOW), R402.2
unnamed: J1.15 (MP1), J1.16 (MP2), R403.1
unnamed: C401.1, J1.1 (VCC)
unnamed: J701.10 (DAS/~DSS/~LED1), R707.2
unnamed: J701.68 (SUSCLK), U703.3 (Out)
unnamed: R605.2, U602.4
unnamed: R107.1, U1.8 (CS)
unnamed: R108.2, U1.7 (SDO)
unnamed: R701.1, U701.5 (ILIM)
VBUS_USB2.0: C702.1, C703.1, U701.6 (OUT), USB701.A4 (VBUS), USB701.A9 (VBUS), USB701.B4 (VBUS), USB701.B9 (VBUS)

Notes on the sheet:
CM5
DSI_CSI
Ethernet
HDMI
Main
PCIe-M2
USB
