copperheadhq/copperhead/manual-tests/real-designs/examples/complex_hierarchy/drawn/board.kicad_sch

## KiCad design manual-tests/real-designs/examples/complex_hierarchy/drawn/board.kicad_sch (2026-08-26)

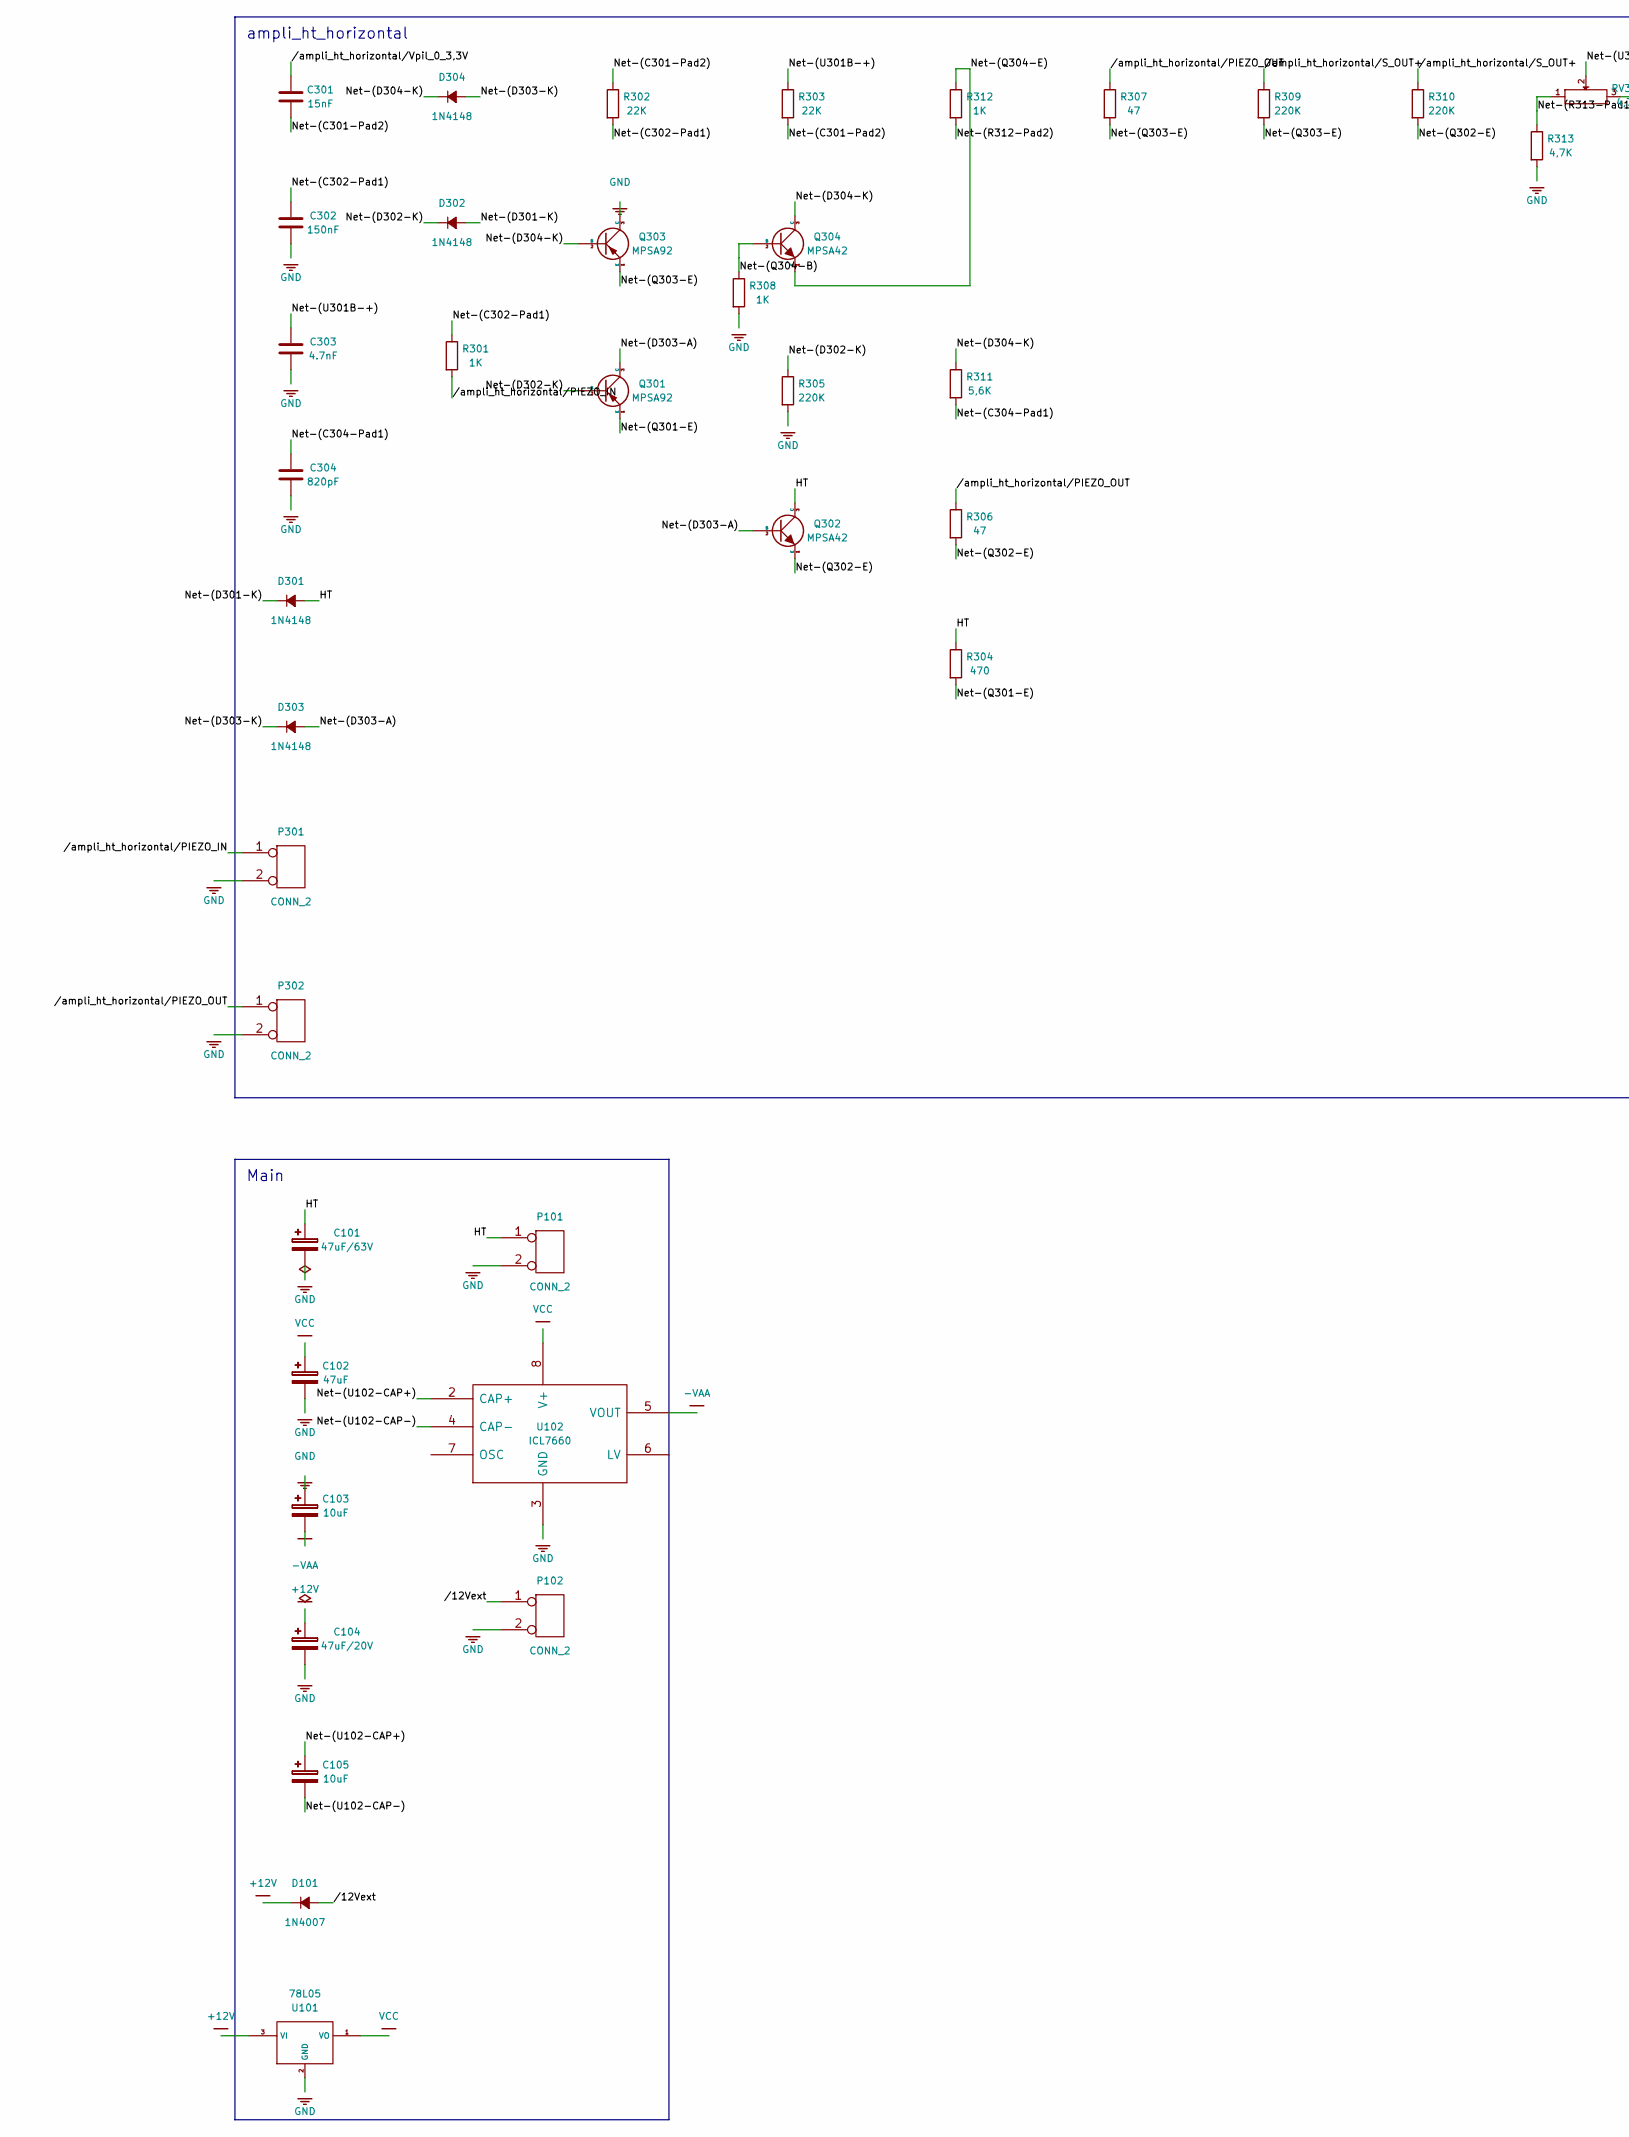
[picture p51: schematic board.kicad_sch, part in row 1, column 1]

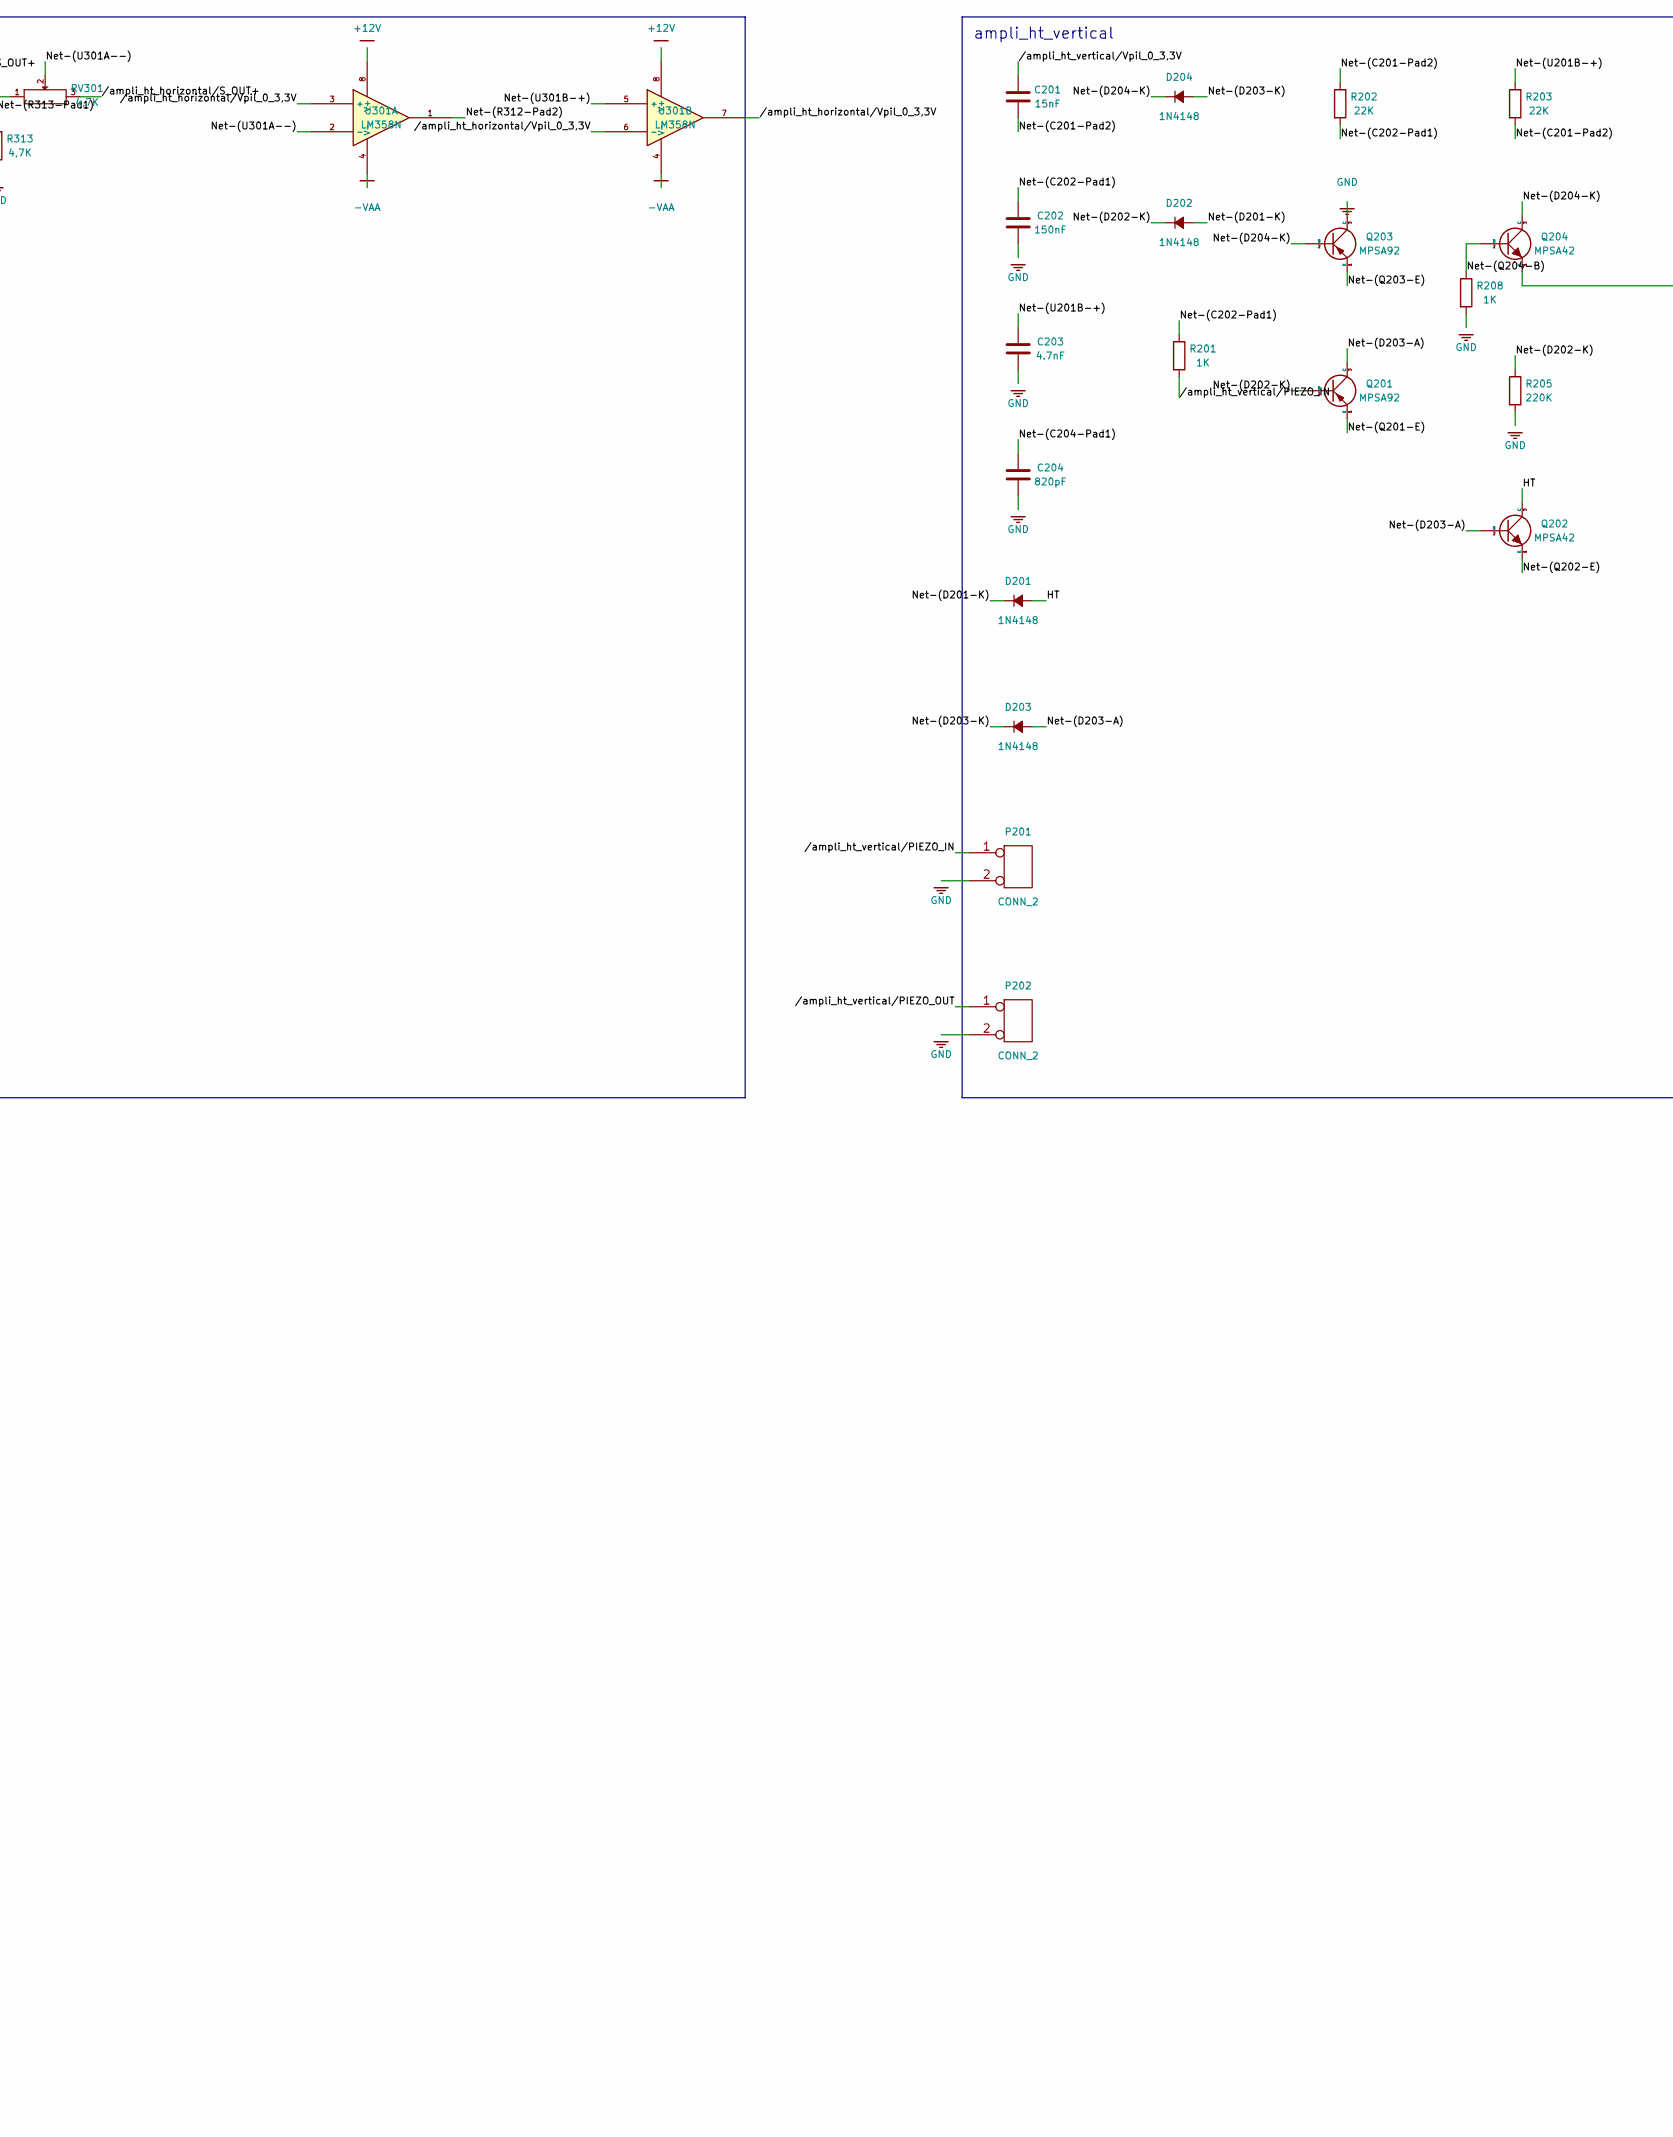
[picture p52: schematic board.kicad_sch, part in row 1, column 2]

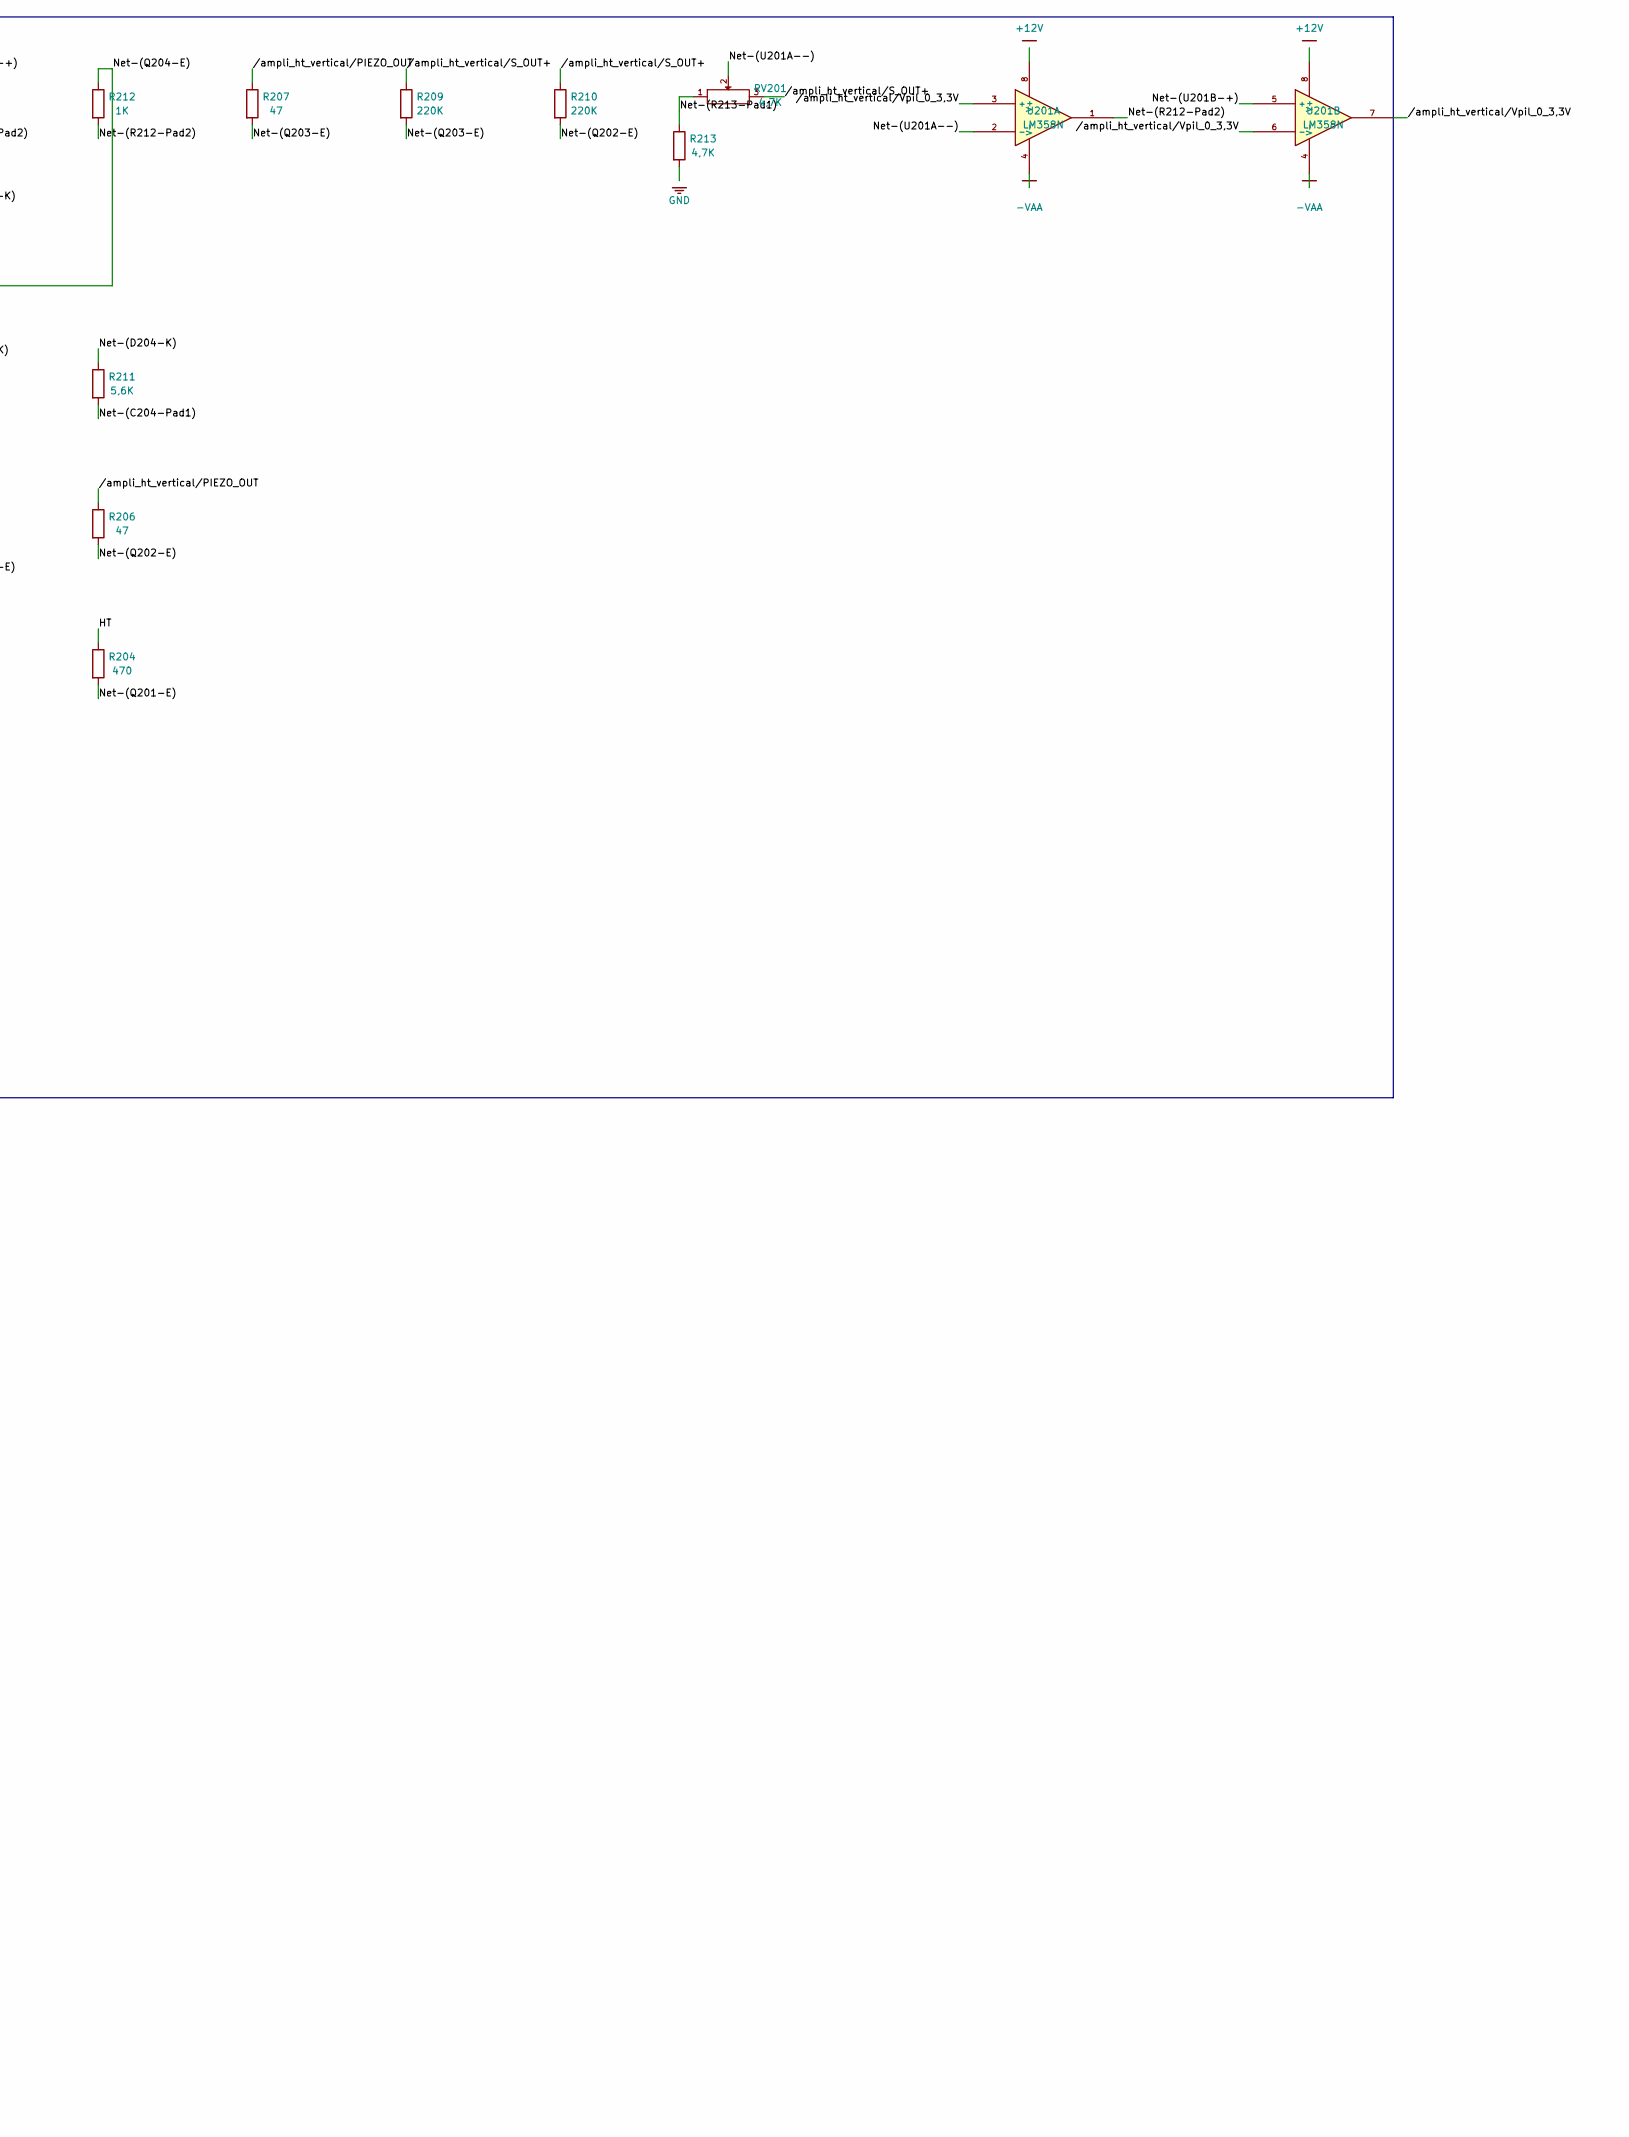
[picture p53: schematic board.kicad_sch, part in row 1, column 3]

Parts:
C101: 47uF/63V; CP_Axial_L11.0mm_D6.0mm_P18.00mm_Horizontal
C102: 47uF; CP_Axial_L10.0mm_D4.5mm_P15.00mm_Horizontal
C103, C105: 10uF; CP_Axial_L10.0mm_D4.5mm_P15.00mm_Horizontal
C104: 47uF/20V; CP_Axial_L10.0mm_D4.5mm_P15.00mm_Horizontal
C201, C301: 15nF; C_Disc_D5.0mm_W2.5mm_P5.00mm
C202, C302: 150nF; C_Disc_D5.0mm_W2.5mm_P5.00mm
C203, C303: 4.7nF; C_Disc_D5.0mm_W2.5mm_P5.00mm
C204, C304: 820pF; C_Disc_D5.0mm_W2.5mm_P5.00mm
D101: 1N4007; D_DO-41_SOD81_P12.70mm_Horizontal
D201, D202, D203, D204, D301, D302, D303, D304: 1N4148; D_DO-35_SOD27_P7.62mm_Horizontal
P101, P102, P201, P202, P301, P302: CONN_2; Altech_AK300_1x02_P5.00mm_45-Degree
Q201, Q203, Q301, Q303: MPSA92; TO-92_HandSolder
Q202, Q204, Q302, Q304: MPSA42; TO-92_HandSolder
R201, R208, R212, R301, R308, R312: 1K; R_Axial_DIN0204_L3.6mm_D1.6mm_P7.62mm_Horizontal
R202, R203, R302, R303: 22K; R_Axial_DIN0204_L3.6mm_D1.6mm_P7.62mm_Horizontal
R204, R304: 470; R_Axial_DIN0204_L3.6mm_D1.6mm_P7.62mm_Horizontal
R205, R209, R210, R305, R309, R310: 220K; R_Axial_DIN0204_L3.6mm_D1.6mm_P7.62mm_Horizontal
R206, R207, R306, R307: 47; R_Axial_DIN0204_L3.6mm_D1.6mm_P7.62mm_Horizontal
R211, R311: 5,6K; R_Axial_DIN0204_L3.6mm_D1.6mm_P7.62mm_Horizontal
R213, R313: 4,7K; R_Axial_DIN0204_L3.6mm_D1.6mm_P7.62mm_Horizontal
RV201, RV301: 4,7K; Potentiometer_Bourns_3266W_Vertical
U101: 78L05; TO-92_HandSolder
U102: ICL7660; DIP-8_W7.62mm_LongPads
U201, U301: LM358N; DIP-8_W7.62mm_LongPads

Connections:
+12V: C104.1, D101.1 (K), U101.3 (VI), U201.8 (V+), U301.8 (V+)
-VAA: C103.2, U102.5 (VOUT), U201.4 (V-), U301.4 (V-)
/12Vext: D101.2 (A), P102.1
/ampli_ht_horizontal/PIEZO_IN: P301.1, R301.2
/ampli_ht_horizontal/PIEZO_OUT: P302.1, R306.1, R307.1
/ampli_ht_horizontal/S_OUT+: R309.1, R310.1, RV301.3
/ampli_ht_horizontal/Vpil_0_3,3V: C301.1, U301.3 (+), U301.6 (-), U301.7
/ampli_ht_vertical/PIEZO_IN: P201.1, R201.2
/ampli_ht_vertical/PIEZO_OUT: P202.1, R206.1, R207.1
/ampli_ht_vertical/S_OUT+: R209.1, R210.1, RV201.3
/ampli_ht_vertical/Vpil_0_3,3V: C201.1, U201.3 (+), U201.6 (-), U201.7
GND: C101.2, C102.2, C103.1, C104.2, C202.2, C203.2, C204.2, C302.2, C303.2, C304.2, P101.2 (PM), P102.2 (PM), P201.2 (PM), P202.2 (PM), P301.2 (PM), P302.2 (PM), Q203.3 (C), Q303.3 (C), R205.2, R208.2, R213.2, R305.2, R308.2, R313.2, U101.2 (GND), U102.3 (GND)
HT: C101.1, D201.2 (A), D301.2 (A), P101.1, Q202.3 (C), Q302.3 (C), R204.1, R304.1
unnamed: C201.2, R202.1, R203.2
unnamed: C202.1, R201.1, R202.2
unnamed: C204.1, R211.2
unnamed: C301.2, R302.1, R303.2
unnamed: C302.1, R301.1, R302.2
unnamed: C304.1, R311.2
unnamed: D201.1 (K), D202.2 (A)
unnamed: D202.1 (K), Q201.2 (B), R205.1
unnamed: D203.2 (A), Q201.3 (C), Q202.2 (B)
unnamed: D203.1 (K), D204.2 (A)
unnamed: D204.1 (K), Q203.2 (B), Q204.3 (C), R211.1
unnamed: D301.1 (K), D302.2 (A)
unnamed: D302.1 (K), Q301.2 (B), R305.1
unnamed: D303.2 (A), Q301.3 (C), Q302.2 (B)
unnamed: D303.1 (K), D304.2 (A)
unnamed: D304.1 (K), Q303.2 (B), Q304.3 (C), R311.1
unnamed: Q201.1 (E), R204.2
unnamed: Q202.1 (E), R206.2, R210.2
unnamed: Q203.1 (E), R207.2, R209.2
unnamed: Q204.2 (B), R208.1
unnamed: Q204.1 (E), R212.1
unnamed: Q301.1 (E), R304.2
unnamed: Q302.1 (E), R306.2, R310.2
unnamed: Q303.1 (E), R307.2, R309.2
unnamed: Q304.2 (B), R308.1
unnamed: Q304.1 (E), R312.1
unnamed: R212.2, U201.1
unnamed: R213.1, RV201.1
unnamed: R312.2, U301.1
unnamed: R313.1, RV301.1
unnamed: C105.1, U102.2 (CAP+)
unnamed: C105.2, U102.4 (CAP-)
unnamed: RV201.2, U201.2 (-)
unnamed: C203.1, R203.1, U201.5 (+)
unnamed: RV301.2, U301.2 (-)
unnamed: C303.1, R303.1, U301.5 (+)
VCC: C102.1, U101.1 (VO), U102.8 (V+)

Notes on the sheet:
ampli_ht_horizontal
ampli_ht_vertical
Main
