copperheadhq/copperhead/manual-tests/real-designs/examples/ecc83/drawn/board.kicad_sch

## KiCad design manual-tests/real-designs/examples/ecc83/drawn/board.kicad_sch (2026-08-26)

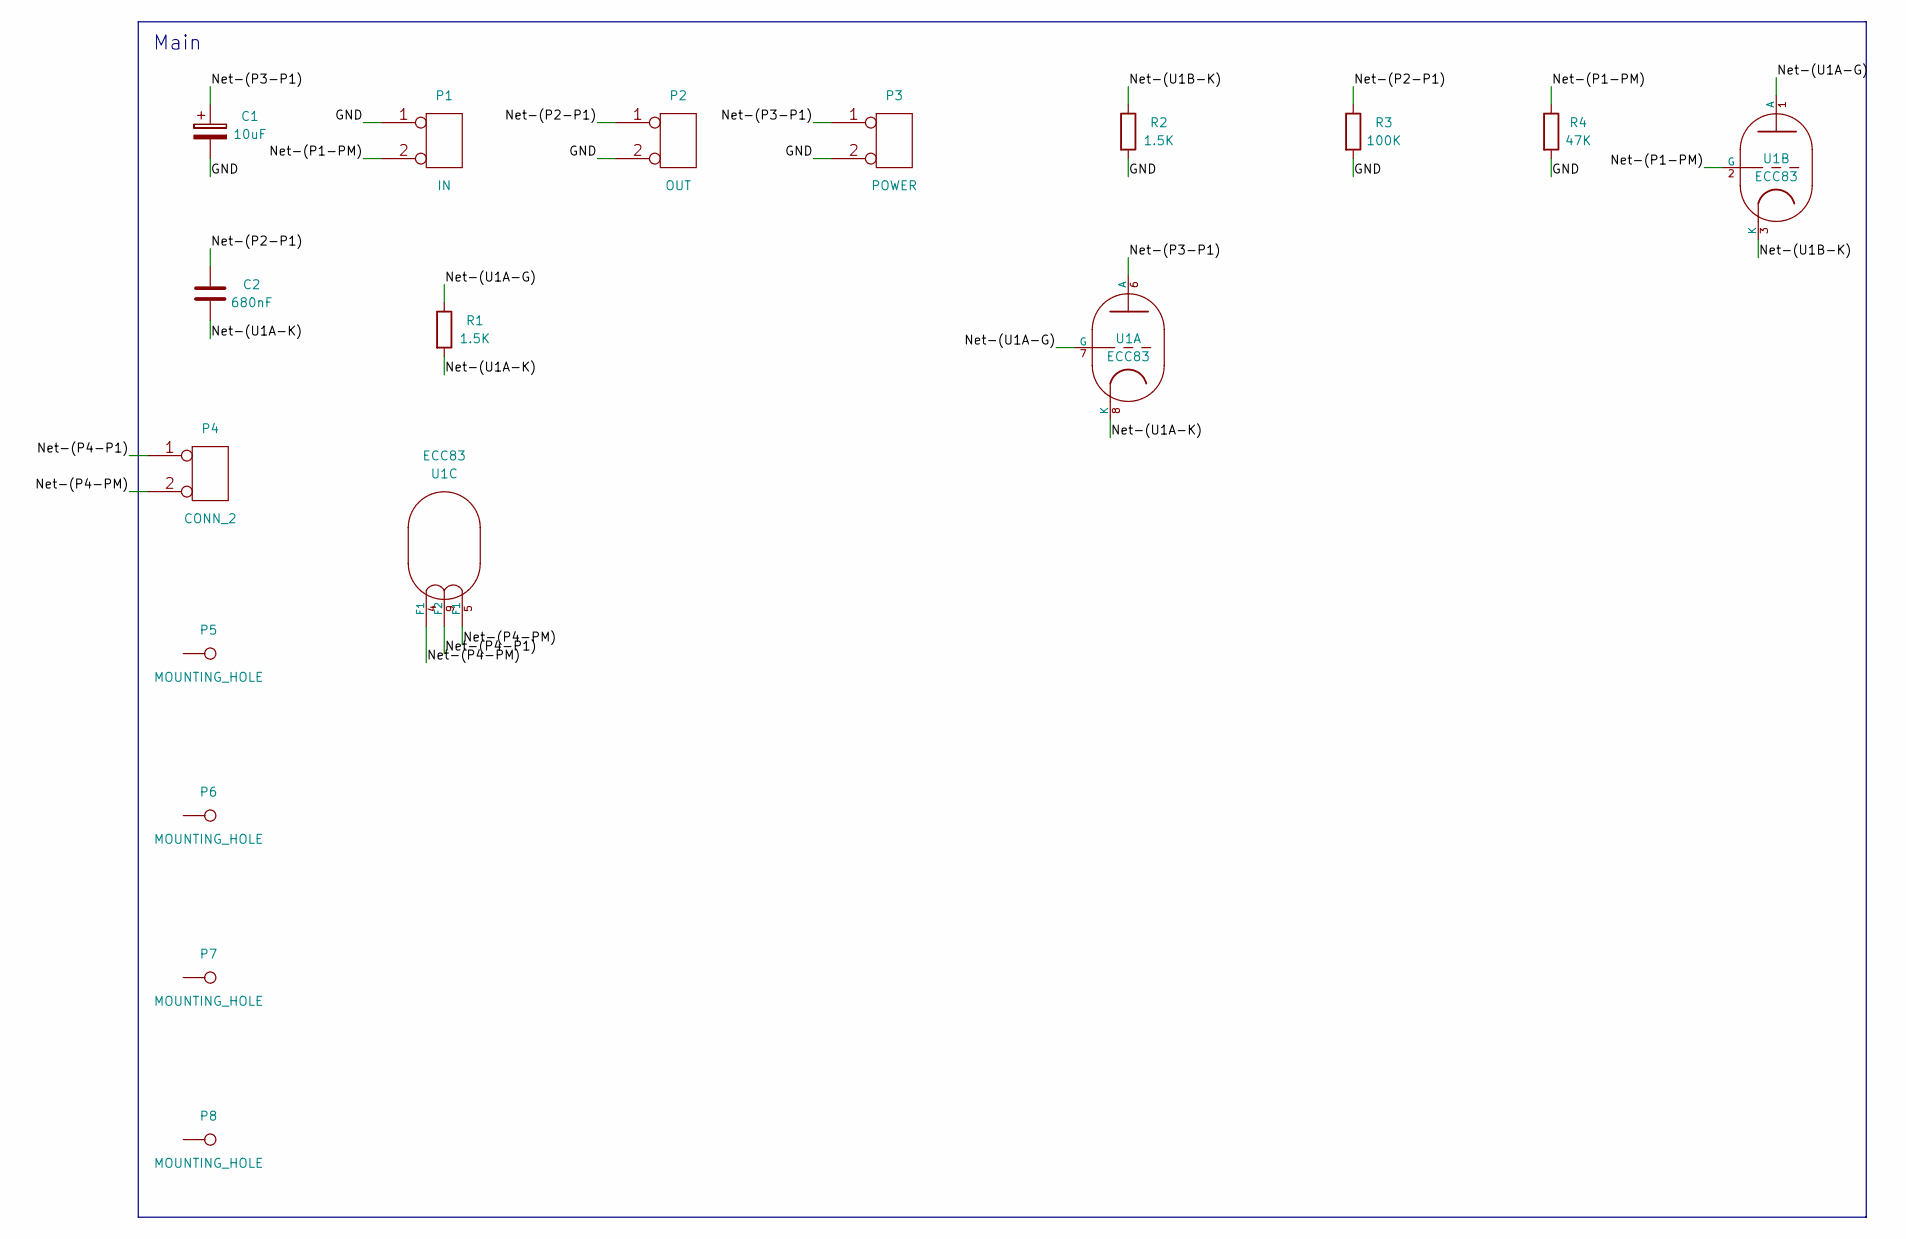
[picture p54: schematic board.kicad_sch]

Parts:
C1: 10uF; CP_Radial_D10.0mm_P5.00mm
C2: 680nF; C_Disc_D4.7mm_W2.5mm_P5.00mm
P1: IN; Altech_AK300_1x02_P5.00mm_45-Degree
P2: OUT; Altech_AK300_1x02_P5.00mm_45-Degree
P3: POWER; Altech_AK300_1x02_P5.00mm_45-Degree
P4: CONN_2; Altech_AK300_1x02_P5.00mm_45-Degree
P5, P6, P7, P8: MOUNTING_HOLE; MountingHole_3.2mm_M3_DIN965_Pad
R1, R2: 1.5K; R_Axial_DIN0207_L6.3mm_D2.5mm_P7.62mm_Horizontal
R3: 100K; R_Axial_DIN0207_L6.3mm_D2.5mm_P7.62mm_Horizontal
R4: 47K; R_Axial_DIN0207_L6.3mm_D2.5mm_P7.62mm_Horizontal
U1: ECC83; Valve_ECC-83-1

Connections:
GND: C1.2, P1.1, P2.2 (PM), P3.2 (PM), R2.2, R3.2, R4.2
unnamed: P1.2 (PM), R4.1, U1.2 (G)
unnamed: C2.1, P2.1, R3.1
unnamed: C1.1, P3.1, U1.6 (A)
unnamed: P4.1, U1.9 (F2)
unnamed: P4.2 (PM), U1.4 (F1), U1.5 (F1)
unnamed: R1.1, U1.1 (A), U1.7 (G)
unnamed: C2.2, R1.2, U1.8 (K)
unnamed: R2.1, U1.3 (K)

Notes on the sheet:
Main
