copperheadhq/copperhead/manual-tests/real-designs/examples/interf_u/drawn/board.kicad_sch

## KiCad design manual-tests/real-designs/examples/interf_u/drawn/board.kicad_sch (2026-08-09)

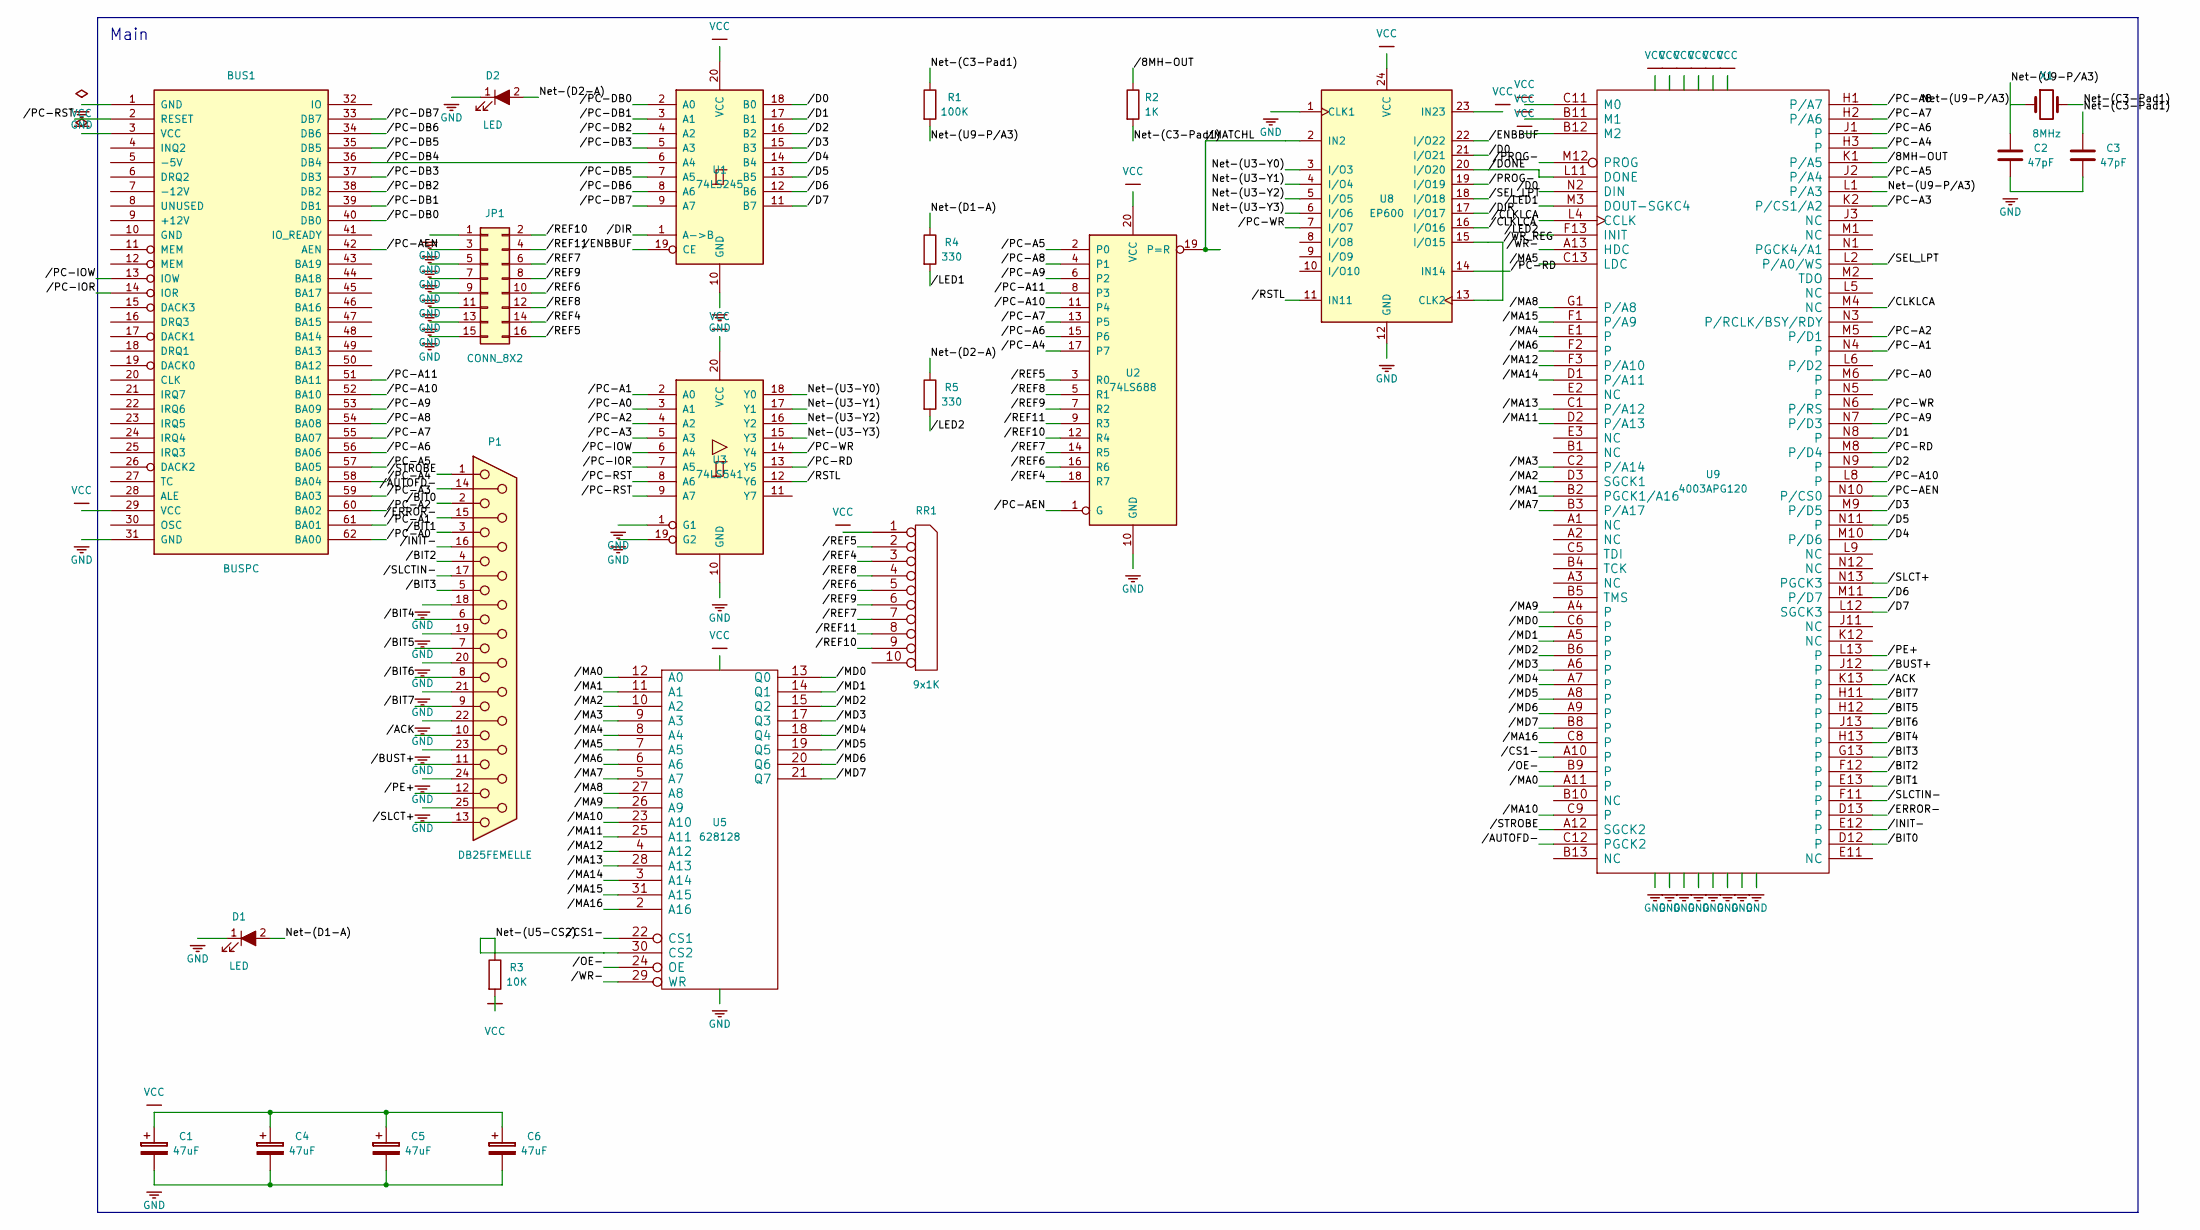
[picture p55: schematic board.kicad_sch]

Parts:
BUS1: BUSPC; BUS_PC
C1, C4, C5, C6: 47uF; CP_Axial_L10.0mm_D4.5mm_P15.00mm_Horizontal
C2, C3: 47pF; C_Disc_D3.0mm_W2.0mm_P2.50mm
D1, D2: LED; LED_D5.0mm
JP1: CONN_8X2; PinHeader_2x08_P2.54mm_Vertical
P1: DB25FEMELLE; DSUB-25_Female_Horizontal_P2.77x2.84mm_EdgePinOffset9.90mm_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
R1: 100K; R_Axial_DIN0207_L6.3mm_D2.5mm_P7.62mm_Horizontal
R2: 1K; R_Axial_DIN0207_L6.3mm_D2.5mm_P7.62mm_Horizontal
R3: 10K; R_Axial_DIN0207_L6.3mm_D2.5mm_P7.62mm_Horizontal
R4, R5: 330; R_Axial_DIN0207_L6.3mm_D2.5mm_P7.62mm_Horizontal
RR1: 9x1K; R_Array_SIP10
U1: 74LS245; DIP-20_W7.62mm
U2: 74LS688; DIP-20_W7.62mm
U3: 74LS541; DIP-20_W7.62mm
U5: 628128; DIP-32_W15.24mm
U8: EP600; DIP-24_W7.62mm
U9: 4003APG120; PGA120
X1: 8MHz; Crystal_HC18-U_Horizontal

Connections:
/8MH-OUT: R2.1, U9.K1 (P/A5)
/ACK: P1.10, U9.K13
/AUTOFD-: P1.14, U9.C12 (PGCK2)
/BIT0: P1.2, U9.D12
/BIT1: P1.3, U9.E13
/BIT2: P1.4, U9.F12
/BIT3: P1.5, U9.G13
/BIT4: P1.6, U9.H13
/BIT5: P1.7, U9.H12
/BIT6: P1.8, U9.J13
/BIT7: P1.9, U9.H11
/BUST+: P1.11, U9.J12
/CLKLCA: U8.16 (I/O16), U9.L4 (CCLK), U9.M4 (NC)
/CS1-: U5.22 (CS1), U9.A10
/D0: U1.18 (B0), U8.21 (I/O21), U9.N2 (DIN)
/D1: U1.17 (B1), U9.N8
/D2: U1.16 (B2), U9.N9
/D3: U1.15 (B3), U9.M9 (P/D5)
/D4: U1.14 (B4), U9.M10 (P/D6)
/D5: U1.13 (B5), U9.N11
/D6: U1.12 (B6), U9.M11 (P/D7)
/D7: U1.11 (B7), U9.L12 (SGCK3)
/DIR: U1.1 (A->B), U8.17 (I/O17)
/DONE: U8.20 (I/O20), U9.L11 (DONE)
/ENBBUF: U1.19 (CE), U8.22 (I/O22)
/ERROR-: P1.15, U9.D13
/INIT-: P1.16, U9.E12
/LED1: R4.2, U9.M3 (DOUT-SGKC4)
/LED2: R5.2, U9.F13 (INIT)
/MA0: U5.12 (A0), U9.A11
/MA1: U5.11 (A1), U9.B2 (PGCK1/A16)
/MA2: U5.10 (A2), U9.D3 (SGCK1)
/MA3: U5.9 (A3), U9.C2 (P/A14)
/MA4: U5.8 (A4), U9.E1
/MA5: U5.7 (A5), U9.C13 (LDC)
/MA6: U5.6 (A6), U9.F2
/MA7: U5.5 (A7), U9.B3 (P/A17)
/MA8: U5.27 (A8), U9.G1 (P/A8)
/MA9: U5.26 (A9), U9.A4
/MA10: U5.23 (A10), U9.C9
/MA11: U5.25 (A11), U9.D2 (P/A13)
/MA12: U5.4 (A12), U9.F3 (P/A10)
/MA13: U5.28 (A13), U9.C1 (P/A12)
/MA14: U5.3 (A14), U9.D1 (P/A11)
/MA15: U5.31 (A15), U9.F1 (P/A9)
/MA16: U5.2 (A16), U9.C8
/MATCHL: U2.19 (P=R), U8.2 (IN2)
/MD0: U5.13 (Q0), U9.C6
/MD1: U5.14 (Q1), U9.A5
/MD2: U5.15 (Q2), U9.B6
/MD3: U5.17 (Q3), U9.A6
/MD4: U5.18 (Q4), U9.A7
/MD5: U5.19 (Q5), U9.A8
/MD6: U5.20 (Q6), U9.A9
/MD7: U5.21 (Q7), U9.B8
/OE-: U5.24 (OE), U9.B9
/PC-A0: BUS1.62 (BA00), U3.3 (A1), U9.M6
/PC-A1: BUS1.61 (BA01), U3.2 (A0), U9.N4
/PC-A2: BUS1.60 (BA02), U3.4 (A2), U9.M5 (P/D1)
/PC-A3: BUS1.59 (BA03), U3.5 (A3), U9.K2 (P/CS1/A2)
/PC-A4: BUS1.58 (BA04), U2.17 (P7), U9.H3
/PC-A5: BUS1.57 (BA05), U2.2 (P0), U9.J2 (P/A4)
/PC-A6: BUS1.56 (BA06), U2.15 (P6), U9.J1
/PC-A7: BUS1.55 (BA07), U2.13 (P5), U9.H2 (P/A6)
/PC-A8: BUS1.54 (BA08), U2.4 (P1), U9.H1 (P/A7)
/PC-A9: BUS1.53 (BA09), U2.6 (P2), U9.N7 (P/D3)
/PC-A10: BUS1.52 (BA10), U2.11 (P4), U9.L8
/PC-A11: BUS1.51 (BA11), U2.8 (P3)
/PC-AEN: BUS1.42 (AEN), U2.1 (G), U9.N10 (P/CS0)
/PC-DB0: BUS1.40 (DB0), U1.2 (A0)
/PC-DB1: BUS1.39 (DB1), U1.3 (A1)
/PC-DB2: BUS1.38 (DB2), U1.4 (A2)
/PC-DB3: BUS1.37 (DB3), U1.5 (A3)
/PC-DB4: BUS1.36 (DB4), U1.6 (A4)
/PC-DB5: BUS1.35 (DB5), U1.7 (A5)
/PC-DB6: BUS1.34 (DB6), U1.8 (A6)
/PC-DB7: BUS1.33 (DB7), U1.9 (A7)
/PC-IOR: BUS1.14 (IOR), U3.7 (A5)
/PC-IOW: BUS1.13 (IOW), U3.6 (A4)
/PC-RD: U3.13 (Y5), U8.14 (IN14), U9.M8 (P/D4)
/PC-RST: BUS1.2 (RESET), U3.8 (A6), U3.9 (A7)
/PC-WR: U3.14 (Y4), U8.7 (I/O7), U9.N6 (P/RS)
/PE+: P1.12, U9.L13
/PROG-: U8.19 (I/O19), U9.M12 (PROG)
/REF4: JP1.14, RR1.3, U2.18 (R7)
/REF5: JP1.16, RR1.2, U2.3 (R0)
/REF6: JP1.10, RR1.5, U2.16 (R6)
/REF7: JP1.6, RR1.7, U2.14 (R5)
/REF8: JP1.12, RR1.4, U2.5 (R1)
/REF9: JP1.8, RR1.6, U2.7 (R2)
/REF10: JP1.2, RR1.9, U2.12 (R4)
/REF11: JP1.4, RR1.8, U2.9 (R3)
/RSTL: U3.12 (Y6), U8.11 (IN11)
/SEL_LPT: U8.18 (I/O18), U9.L2 (P/A0/WS)
/SLCT+: P1.13, U9.N13 (PGCK3)
/SLCTIN-: P1.17, U9.F11
/STROBE: P1.1, U9.A12 (SGCK2)
/WR-: U5.29 (WR), U9.A13 (HDC)
/WR_REG: U8.13 (CLK2), U8.15 (I/O15)
GND: BUS1.1 (GND), BUS1.31 (GND), C1.2, C2.2, C3.2, C4.2, C5.2, C6.2, D1.1 (K), D2.1 (K), JP1.1, JP1.3, JP1.5, JP1.7, JP1.9, JP1.11, JP1.13, JP1.15, P1.18, P1.19, P1.20, P1.21, P1.22, P1.23, P1.24, P1.25, U1.10 (GND), U2.10 (GND), U3.1 (G1), U3.10 (GND), U3.19 (G2), U5.16 (GND), U8.1 (CLK1), U8.12 (GND), U9.B7 (GND), U9.C4 (GND), U9.C10 (GND), U9.G2 (GND), U9.G11 (GND), U9.K3 (GND), U9.K11 (GND), U9.L7 (GND)
unnamed: C3.1, R1.1, R2.2, X1.2
unnamed: D1.2 (A), R4.1
unnamed: D2.2 (A), R5.1
unnamed: U3.18 (Y0), U8.3 (I/O3)
unnamed: U3.17 (Y1), U8.4 (I/O4)
unnamed: U3.16 (Y2), U8.5 (I/O5)
unnamed: U3.15 (Y3), U8.6 (I/O6)
unnamed: R3.1, U5.30 (CS2)
unnamed: C2.1, R1.2, U9.L1 (P/A3), X1.1
VCC: BUS1.3 (VCC), BUS1.29 (VCC), C1.1, C4.1, C5.1, C6.1, R3.2, RR1.1 (COM), U1.20 (VCC), U2.20 (VCC), U3.20 (VCC), U5.32 (VCC), U8.23 (IN23), U8.24 (VCC), U9.B11 (M1), U9.B12 (M2), U9.C3 (VCC), U9.C11 (M0), U9.D11 (VCC), U9.G12 (VCC), U9.L3 (VCC), U9.L10 (VCC), U9.M7 (VCC)

Notes on the sheet:
Main
