copperheadhq/copperhead/manual-tests/real-designs/examples/kit-dev-coldfire-xilinx_5213/drawn/board.kicad_sch

## KiCad design manual-tests/real-designs/examples/kit-dev-coldfire-xilinx_5213/drawn/board.kicad_sch (2026-08-26)

Schematic: board.kicad_sch

Parts:
ABRT_SW101: SW_PUSH; SW_PUSH_SMALL
ALLPST101: CONN_1; PinHeader_1x01_P2.54mm_Vertical
BDM_PORT101: CONN_13X2; PinHeader_2x13_P2.54mm_Vertical
C101, C103, C104, C109, C110, C111, C112, C113, C114, C115, C116, C117, C118, C201, C202, C203, C204, C205, C206, C207, C208, C209, C210, C211, C213, C214, C216, C217, C218, C219, C220, C221, C301, C302, C303, C304, C305, C306, C307, C308, C309, C310, C311: 100nF; C_0805_2012Metric
C102, C105: 1nF; C_0805_2012Metric
C106, C107: 10pF; C_0805_2012Metric
C108: 10uF; SM1206POL
C119: 100uF; SM1206POL
C212: 10uF; CP_Radial_D8.0mm_P5.00mm
C215: 220uF; CP_Radial_D8.0mm_P5.00mm
CAN_EN201: CONN_2X2; PinHeader_2x02_P2.54mm_Vertical
CAN_TERM201: JUMPER; PinHeader_1x02_P2.54mm_Vertical
CLKOUT101: CONN_1; PinHeader_1x01_P2.54mm_Vertical
COM_SEL201, COM_SEL202, COM_SEL203: CONN_3; PinHeader_1x03_P2.54mm_Vertical
CT101: JUMPER; PinHeader_1x02_P2.54mm_Vertical
D101, D102: BAT54; D_SOT-23_ANK
D201: 1N4004; D_DO-15_P12.70mm_Horizontal
D301, D302: LED; LED_1206_3216Metric
F201: FUSE; FSUPCMS
FB101: BEAD; R_1206_3216Metric_Pad1.30x1.75mm_HandSolder
GND101: CONN_1; PinHeader_1x01_P2.54mm_Vertical
J201: JACK_2P; JACK_ALIM
JP101: JUMPER_TRIPLE; PinHeader_2x03_P2.54mm_Vertical
JP201: JUMPER; PinHeader_1x02_P2.54mm_Vertical
L101, L102: 10uH; R_1206_3216Metric_Pad1.30x1.75mm_HandSolder
LED201, LED202, LED203, LED204, LED205: LED; LED_1206_3216Metric
LEDABRT101: LED_RED; LED_1206_3216Metric
LED_RST101: LED_RED; LED_1206_3216Metric
LV101: DS1818; TO-92
MCU_PORT201: CONN_30X2; PinHeader_2x30_P2.54mm_Vertical
P301: CONN_6; PinHeader_1x06_P2.54mm_Vertical
P302: CONN_2X2; PinHeader_2x02_P2.54mm_Vertical
P303: CONN_20X2; PinHeader_2x20_P2.54mm_Vertical
PULUPEN201: CONN_4X2; PinHeader_2x04_P2.54mm_Vertical
Q101: 3906; SOT23EBC
R101, R102, R106, R107, R108, R109, R110, R111, R112, R211, R212, R213, R214: 4,7K; R_0805_2012Metric
R103, R116, R202, R203, R204, R206, R207: 270; R_0805_2012Metric
R104, R210, R303, R304: 1K; R_0805_2012Metric
R105: 20K; R_0805_2012Metric
R113: 0; R_0805_2012Metric
R114: 22; R_0805_2012Metric
R115: 4.7K; R_0805_2012Metric
R117, R118, R119, R120, R121, R122, R123, R124, R201, R205, R208, R215: 10K; R_0805_2012Metric
R125: 1M; R_0805_2012Metric
R209: 62; R_0805_2012Metric
R301: 4K7; R_0805_2012Metric
R302: 3,3; R_Axial_DIN0207_L6.3mm_D2.5mm_P10.16mm_Horizontal
RCAN201, RCAN202: R; R_0805_2012Metric
RS201: CONN_1; PinHeader_1x01_P2.54mm_Vertical
RST_SW101: SW_PUSH; SW_PUSH_SMALL
SW201, SW202: SW_PUSH; SW_PUSH_SMALL
SW_ONOFF201: SWITCH_INV; SW_SPDT
TA-101: CONN_1; PinHeader_1x01_P2.54mm_Vertical
TB201: CONN_2; Altech_AK300_1x02_P5.00mm_45-Degree
U101: 74AHC1G14; SOT353
U102: MCF5213-LQFP100; LQFP-100_14x14mm_P0.5mm
U201: 74HC125; SOIC-14_3.9x8.7mm_P1.27mm
U202, U203, U204: MAX202; SOIC-16_3.9x9.9mm_P1.27mm
U205: PCA82C251; SOIC-8_3.9x4.9mm_P1.27mm
U301: XCR3256-TQ144; TQFP-144_20x20mm_P0.5mm
UARTCAN201, UARTCAN202, UARTCAN203: DB9; DSUB-9_Female_Horizontal_P2.77x2.84mm_EdgePinOffset7.70mm_H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
UART_EN201, UART_EN202, UART_EN203: CONN_4X2; PinHeader_2x04_P2.54mm_Vertical
VDDA101: JUMPER; PinHeader_1x02_P2.54mm_Vertical
VR201: LT1129_QPACK; TO-263-5_TabPin3
VREF201: CONN_1; PinHeader_1x01_P2.54mm_Vertical
VX_EN201: JUMPER; PinHeader_1x02_P2.54mm_Vertical
Y101: 8MHz; Crystal_HC18-U_Horizontal

Connections:
+3.3V: ABRT_SW101.2, BDM_PORT101.9, BDM_PORT101.25 (P24), C101.2, C110.1, C111.1, C112.1, C113.1, C114.1, C115.1, C116.1, C117.1, C118.1, C119.1, C202.1, C203.1, C204.1, C208.1, C209.1, C215.1, C216.1, C217.1, C219.1, C301.1, C302.1, C303.1, C304.1, C305.1, C306.1, C307.1, C308.1, C309.1, C310.1, C311.1, L101.1, LEDABRT101.2 (A), LV101.2 (In), MCU_PORT201.59, P301.1, Q101.1 (E), R101.1, R102.1, R106.1, R107.1, R108.1, R109.1, R110.1, R111.1, R112.2, R118.2, R119.2, R120.2, R121.2, R122.2, R123.2, R124.2, R201.1, R207.2, R211.1, R212.1, R213.1, R214.1, R301.1, R302.1, RCAN202.1, U101.5 (VCC), U102.1 (VCC), U102.2 (VCC), U102.14 (VCC), U102.22 (VCC), U102.23 (VCC), U102.34 (VCC), U102.41 (VCC), U102.55 (VSTBY), U102.57 (VCC), U102.68 (VCC), U102.81 (VCC), U102.93 (VCC), U201.14 (VCC), U202.16 (VCC), U203.16 (VCC), U204.16 (VCC), U205.3 (VCC), U301.24 (VCC), U301.50 (VCC), U301.51 (VCC), U301.58 (VCC), U301.73 (VCC), U301.76 (VCC), U301.95 (VCC), U301.115 (VCC), U301.123 (VCC), U301.130 (VCC), U301.144 (VCC), VDDA101.1, VR201.1 (OUT), VR201.2 (SENSE), VX_EN201.1
/ALLPST: ALLPST101.1, U102.86 (ALLPST)
/AN0: MCU_PORT201.10, U102.43 (AN0/PAN0)
/AN1: MCU_PORT201.12, U102.44 (AN1/PAN1)
/AN2: MCU_PORT201.14, U102.45 (AN2/PAN2)
/AN3: MCU_PORT201.16, U102.46 (AN3/PAN3)
/AN4: MCU_PORT201.18, U102.54 (AN4/PAN4)
/AN5: MCU_PORT201.20, U102.53 (AN5/PAN5)
/AN6: MCU_PORT201.22, U102.52 (AN6/PAN6)
/AN7: MCU_PORT201.24, U102.51 (AN7/PAN7)
/BKPT-: BDM_PORT101.2, R107.2, U102.76 (~BKPT/TMS)
/CANRX: CAN_EN201.4, MCU_PORT201.28, PULUPEN201.7, U102.11 (SDA/CANRX/PAS1/URXD2)
/CANTX: CAN_EN201.1, MCU_PORT201.26, PULUPEN201.5, U102.10 (SCL/CANTX/PAS0/UTXD2)
/CLKIN/EXTAL: C107.1, R125.2, U102.73 (CLKIN/EXTAL), Y101.1
/CLKMOD0: JP101.6, R101.2, U102.40 (CLKMOD0)
/CLKMOD1: JP101.4, R102.2, U102.39 (CLKMOD1)
/DDAT0: BDM_PORT101.19, U102.77 (DDATA0/PDD4)
/DDAT1: BDM_PORT101.18, U102.78 (DDATA1/PDD5)
/DDAT2: BDM_PORT101.17, U102.83 (DDATA2/PDD6)
/DDAT3: BDM_PORT101.16, U102.84 (DDATA3/PDD7)
/DSCLK: BDM_PORT101.4, R108.2, U102.85 (DSCLK/~TRST)
/DSI: BDM_PORT101.8, R109.2, U102.79 (DSI/TDI)
/DSO: BDM_PORT101.10, R110.2, U102.80 (DSO/TDO)
/DSPI_DOUT: MCU_PORT201.17, U102.17 (QSPI_DOUT/EZPQ/CANTX/RXD0/PQS0), U301.47 (M12)
/DTIN0: MCU_PORT201.34, U102.36 (DTIN0/DTOUT0/PWM0/PTC0), U201.2 (D)
/DTIN1: MCU_PORT201.36, U102.37 (DTIN1/DTOUT1/PWM2/PTC1), U201.5 (D)
/DTIN2: MCU_PORT201.38, U102.31 (DTIN2/DTOUT2/PWM4/PTC2), U201.12 (D)
/DTIN3: MCU_PORT201.40, U102.32 (DTIN3/DTOUT3/PWM6/PTC3), U201.9 (D)
/GPT0: MCU_PORT201.49, U102.58 (GPT0/PWM1/PTA0)
/GPT1: MCU_PORT201.50, U102.59 (GPT1/PWM3/PTA1)
/GPT2: MCU_PORT201.51, U102.61 (GPT2PWM5//PTA2)
/GPT3: MCU_PORT201.52, U102.62 (GPT3/PWM7/PTA3)
/IRQ-1: MCU_PORT201.2, R118.1, U102.87 (~IRQ1/PNQ1/SYNCA/PWM1), U301.42 (O2)
/IRQ-2: MCU_PORT201.8, R119.1, U102.88 (~IRQ2/PNQ2), U301.43 (O1)
/IRQ-3: MCU_PORT201.31, R120.1, U102.89 (~IRQ3/PNQ3), U301.44 (O0)
/IRQ-4: MCU_PORT201.33, R121.1, SW201.1, U102.90 (~IRQ4/PNQ4)
/IRQ-5: MCU_PORT201.35, R122.1, SW202.1, U102.91 (~IRQ5/PNQ5)
/IRQ-6: MCU_PORT201.37, R123.1, U102.94 (~IRQ6/PNQ6)
/IRQ-7: D101.2 (A), MCU_PORT201.39, R124.1, U102.95 (~IRQ7/PNQ7)
/JTAG_EN: JP101.2, R111.2, U102.26 (JTAG_EN)
/PST0: BDM_PORT101.15, U102.65 (PST0/PDD0)
/PST1: BDM_PORT101.14, U102.66 (PST1/PDD1)
/PST2: BDM_PORT101.13, U102.69 (PST2/PDD2)
/PST3: BDM_PORT101.12, U102.70 (PST3/PDD3)
/PWM1: MCU_PORT201.13, U102.38 (PWM1/PTD0)
/PWM3: MCU_PORT201.15, U102.33 (PWM3/PTD1)
/PWM5: MCU_PORT201.30, U102.60 (PWM5/PTD2)
/PWM7: MCU_PORT201.32, U102.63 (PWM7/PTD3)
/QSPI_CLK: MCU_PORT201.21, PULUPEN201.1, U102.18 (QSPI_CLK/EZPCK/SCL/RTS1/PQS2), U301.48 (M11)
/QSPI_CS0: MCU_PORT201.23, PULUPEN201.3, U102.20 (QSPI_CS0/SDA/CTS1/PQS3)
/QSPI_CS1: MCU_PORT201.25, U102.19 (QSPI_CS1/PQS4), U301.54 (M1)
/QSPI_CS2: MCU_PORT201.27, U102.13 (QSPI_CS2/PQS5), U301.45 (M15)
/QSPI_CS3: MCU_PORT201.29, U102.12 (QSPI_CS3/SYNCA/SYNCB/PQS6)
/QSPI_DIN: MCU_PORT201.19, U102.16 (QSPI_DIN/EZPD/CANRX/RXD1/PQS1), U301.46 (M13)
/RCON-: MCU_PORT201.53, R112.1, U102.21 (RCON/EZPCS)
/RSTI-: BDM_PORT101.7, D102.2 (A), MCU_PORT201.6, R106.2, U102.96 (RSTI)
/RSTO-: MCU_PORT201.4, R115.1, U102.97 (RSTO)
/TCLK: BDM_PORT101.24 (P20), CLKOUT101.1, CT101.2, R114.2, R117.1
/UCTS0: MCU_PORT201.44, U102.6 (~UCTS0/CANRX/PUA3), UART_EN201.8
/UCTS1: MCU_PORT201.11, P302.1, U102.98 (~UCTS1/SYNCA/URXD2/PUB3), U301.49 (M4), UART_EN202.8
/UCTS2: MCU_PORT201.48, U102.27 (~UCTS2/PUC3), UART_EN203.8
/URTS0: MCU_PORT201.42, U102.9 (~URTS0/CANTX/PUA2), UART_EN201.6
/URTS1: MCU_PORT201.9, P302.3, U102.4 (~URTS1/SYNCB/UTXD2/PUB2), U301.53 (M2), UART_EN202.6
/URTS2: MCU_PORT201.46, U102.30 (~URTS2/PUC2), UART_EN203.6
/URXD0: MCU_PORT201.43, U102.7 (URXD0/PUA1), UART_EN201.4
/URXD1: MCU_PORT201.7, U102.100 (URXD1/PUB1), UART_EN202.4
/URXD2: MCU_PORT201.47, U102.28 (URXD2/PUC1), UART_EN203.4
/UTXD0: MCU_PORT201.41, U102.8 (UTXD0/PUA0), UART_EN201.2
/UTXD1: MCU_PORT201.5, U102.99 (UTXD1/PUB0), UART_EN202.2
/UTXD2: MCU_PORT201.45, U102.29 (UTXD2/PUC0), UART_EN203.2
/VCCA: C108.1, C109.1, L102.2, MCU_PORT201.55, MCU_PORT201.57, U102.49 (VRH), U102.50 (VCCA)
/VDDPLL: C102.1, C103.1, L101.2, U102.74 (VCCPLL)
/XTAL: C106.1, R125.1, U102.72 (XTAL), U301.128 (CLK0/IN0), Y101.2
/inout_user/CAN_H: CAN_TERM201.1, COM_SEL203.1, RCAN201.2, U205.7 (CAN+)
/inout_user/CAN_L: COM_SEL201.1, R209.1, RCAN202.2, U205.6 (CAN-)
/inout_user/CTS0: U202.8 (R2IN), UARTCAN201.7
/inout_user/CTS1: U203.8 (R2IN), UARTCAN202.7
/inout_user/CTS2/CANH: COM_SEL203.2 (PM), UARTCAN203.7
/inout_user/RTS0: U202.7 (T2OUT), UARTCAN201.8
/inout_user/RTS1: U203.7 (T2OUT), UARTCAN202.8
/inout_user/RTS2: U204.14 (T1OUT), UARTCAN203.8
/inout_user/RXD0: U202.13 (R1IN), UARTCAN201.3
/inout_user/RXD1: U203.13 (R1IN), UARTCAN202.3
/inout_user/RXD2: COM_SEL202.2 (PM), UARTCAN203.3
/inout_user/RxD_CAN: CAN_EN201.2, U205.4 (RxD)
/inout_user/TXD0: U202.14 (T1OUT), UARTCAN201.2
/inout_user/TXD1: U203.14 (T1OUT), UARTCAN202.2
/inout_user/TXD2/CANL: COM_SEL201.2 (PM), UARTCAN203.2
/inout_user/TxD_CAN: CAN_EN201.3, U205.1 (TxD)
/xilinx/+3,3V_OUT: P303.38, R302.2
/xilinx/LED_TEST1: R303.1, U301.28 (N15)
/xilinx/LED_TEST2: R304.1, U301.27 (N14)
/xilinx/TCK: P301.5, R301.2, U301.89 (E0/TCK)
/xilinx/TDI: P301.4, U301.4 (J0/TDI)
/xilinx/TDO: P301.6, U301.104 (A2/TDO)
/xilinx/TMS: P301.3, U301.20 (N0/TMS)
/xilinx/XIL_D0: P303.1, U301.12 (L2)
/xilinx/XIL_D1: P303.3, U301.11 (J15)
/xilinx/XIL_D2: P303.5, U301.7 (J4)
/xilinx/XIL_D3: P303.7, U301.8 (J11)
/xilinx/XIL_D4: P303.9, U301.2 (I0)
/xilinx/XIL_D5: P303.11, U301.143 (I4)
/xilinx/XIL_D6: P303.13, U301.140 (I14)
/xilinx/XIL_D7: P303.15, U301.138 (K2)
/xilinx/XIL_D8: P303.17, U301.136 (K11)
/xilinx/XIL_D9: P303.19, U301.131 (K15)
/xilinx/XIL_D10: P303.21, U301.122 (D15)
/xilinx/XIL_D11: P303.23, U301.119 (D11)
/xilinx/XIL_D12: P303.25, U301.114 (D0)
/xilinx/XIL_D13: P303.27, U301.111 (B12)
/xilinx/XIL_D14: P303.29, U301.109 (B4)
/xilinx/XIL_D15: P303.31, U301.108 (B1)
/xilinx/XIL_D16: P303.33, U301.100 (A12)
/xilinx/XIL_D17: P303.35, U301.101 (A11)
/xilinx/XIL_D18: P303.37, U301.97 (C1)
/xilinx/XIL_D19: P303.39, U301.96 (C2)
/xilinx/XIL_D20: P303.4, U301.6 (J3)
/xilinx/XIL_D21: P303.6, U301.10 (J14)
/xilinx/XIL_D22: P303.8, U301.5 (J2)
/xilinx/XIL_D23: P303.10, U301.1 (I1)
/xilinx/XIL_D24: P303.12, U301.142 (I12)
/xilinx/XIL_D25: P303.14, U301.139 (I15)
/xilinx/XIL_D26: P303.16, U301.137 (K4)
/xilinx/XIL_D27: P303.18, U301.134 (K12)
/xilinx/XIL_D28: P303.20, U301.132 (K14)
/xilinx/XIL_D29: P303.22, U301.117 (D2)
/xilinx/XIL_D30: P303.24, U301.118 (D4)
/xilinx/XIL_D31: P303.26, U301.116 (D1)
/xilinx/XIL_D32: P303.28, U301.98 (C0)
/xilinx/XIL_D33: P303.30, U301.112 (B14)
/xilinx/XIL_D34: P303.32, U301.113 (B15)
/xilinx/XIL_D35: P303.34, U301.107 (B0)
/xilinx/XIL_D36: P303.36, U301.99 (A13)
GND: BDM_PORT101.3, BDM_PORT101.5, BDM_PORT101.11, BDM_PORT101.20, BDM_PORT101.23, C101.1, C102.2, C103.2, C104.2, C105.2, C106.2, C107.2, C110.2, C111.2, C112.2, C113.2, C114.2, C115.2, C116.2, C117.2, C118.2, C119.2, C201.1, C202.2, C203.2, C207.2, C208.2, C212.2, C213.2, C214.2, C215.2, C216.2, C219.2, C221.2, C301.2, C302.2, C303.2, C304.2, C305.2, C306.2, C307.2, C308.2, C309.2, C310.2, C311.2, COM_SEL202.1, D201.2 (A), D301.1 (K), D302.1 (K), FB101.1, GND101.1, J201.1, J201.2, JP101.1, JP101.3, JP101.5, JP201.1, LED201.1 (K), LED202.1 (K), LED203.1 (K), LED204.1 (K), LED205.1 (K), LED_RST101.1 (K), LV101.3 (Gbd), MCU_PORT201.3, MCU_PORT201.54, MCU_PORT201.60, P301.2, P303.2, P303.40, R105.2, R113.2, R117.2, R205.1, R208.1, R210.2, R215.1, RCAN201.1, RST_SW101.2, SW201.2, SW202.2, TB201.2 (PM), U101.3 (GND), U102.3 (GND), U102.15 (GND), U102.24 (GND), U102.25 (GND), U102.35 (GND), U102.42 (GND), U102.56 (GND), U102.67 (GND), U102.71 (GNDPLL), U102.75 (GND), U102.82 (GND), U102.92 (GND), U201.7 (GND), U202.15 (GND), U203.15 (GND), U204.15 (GND), U205.2 (GND), U301.3 (GND), U301.13 (PORT_EN), U301.17 (GND), U301.33 (GND), U301.52 (GND), U301.57 (GND), U301.59 (GND), U301.64 (GND), U301.85 (GND), U301.105 (GND), U301.124 (GND), U301.125 (CLK3/IN3), U301.126 (CLK2/IN2), U301.127 (CLK1/IN1), U301.129 (GND), U301.135 (GND), UARTCAN201.5, UARTCAN202.5, UARTCAN203.5, VR201.3 (GND)
GNDA: C108.2, C109.2, FB101.2, MCU_PORT201.56, MCU_PORT201.58, U102.47 (VSSA), U102.48 (VRL)
unnamed: ABRT_SW101.1, R104.1
unnamed: BDM_PORT101.6, CT101.1
unnamed: BDM_PORT101.26 (P22), TA-101.1
unnamed: C104.1, R104.2, R105.1, U101.2
unnamed: CAN_TERM201.2, R209.2
unnamed: COM_SEL201.3, U204.7 (T2OUT)
unnamed: COM_SEL202.3, U204.8 (R2IN)
unnamed: COM_SEL203.3, U204.13 (R1IN)
unnamed: D101.1 (K), R103.2, U101.4
unnamed: C105.1, D102.1 (K), LV101.1 (Rst), RST_SW101.1
unnamed: C212.1, C213.1, D201.1 (K), F201.2, VR201.5 (IN)
unnamed: D301.2 (A), R303.2
unnamed: D302.2 (A), R304.2
unnamed: F201.1, SW_ONOFF201.2
unnamed: L102.1, VDDA101.2
unnamed: LED201.2 (A), R202.1
unnamed: LED202.2 (A), R203.1
unnamed: LED203.2 (A), R204.1
unnamed: LED204.2 (A), R206.1
unnamed: LED205.2 (A), R207.1
unnamed: LEDABRT101.1 (K), R103.1
unnamed: LED_RST101.2 (A), R116.2
unnamed: C201.2, MCU_PORT201.1, VX_EN201.2
unnamed: PULUPEN201.2, R211.2
unnamed: PULUPEN201.4, R212.2
unnamed: PULUPEN201.6, R213.2
unnamed: PULUPEN201.8, R214.2
unnamed: Q101.2 (B), R115.2
unnamed: Q101.3 (C), R116.1
unnamed: J201.3, SW_ONOFF201.3, TB201.1
unnamed: R114.1, U102.64 (TCLK/PSTCLK/CLKOUT)
unnamed: R113.1, U102.5 (TEST)
unnamed: JP201.2, R201.2, U201.1 (E), U201.4 (E), U201.10 (E), U201.13 (E)
unnamed: R202.2, U201.3 (O)
unnamed: R203.2, U201.6 (O)
unnamed: R206.2, U201.8 (O)
unnamed: R204.2, U201.11 (O)
unnamed: C205.1, U202.1 (C1+)
unnamed: C205.2, U202.3 (C1-)
unnamed: C206.1, U202.4 (C2+)
unnamed: C206.2, U202.5 (C2-)
unnamed: U202.12 (R1OUT), UART_EN201.3
unnamed: U202.9 (R2OUT), UART_EN201.7
unnamed: U202.11 (T1IN), UART_EN201.1
unnamed: R205.2, U202.10 (T2IN), UART_EN201.5
unnamed: C204.2, U202.2 (V+)
unnamed: C207.1, U202.6 (V-)
unnamed: C210.1, U203.1 (C1+)
unnamed: C210.2, U203.3 (C1-)
unnamed: C211.1, U203.4 (C2+)
unnamed: C211.2, U203.5 (C2-)
unnamed: U203.12 (R1OUT), UART_EN202.3
unnamed: U203.9 (R2OUT), UART_EN202.7
unnamed: U203.11 (T1IN), UART_EN202.1
unnamed: R208.2, U203.10 (T2IN), UART_EN202.5
unnamed: C209.2, U203.2 (V+)
unnamed: C214.1, U203.6 (V-)
unnamed: C218.1, U204.1 (C1+)
unnamed: C218.2, U204.3 (C1-)
unnamed: C220.1, U204.4 (C2+)
unnamed: C220.2, U204.5 (C2-)
unnamed: U204.12 (R1OUT), UART_EN203.7
unnamed: U204.9 (R2OUT), UART_EN203.3
unnamed: R215.2, U204.11 (T1IN), UART_EN203.5
unnamed: U204.10 (T2IN), UART_EN203.1
unnamed: C217.2, U204.2 (V+)
unnamed: C221.1, U204.6 (V-)
unnamed: R210.1, RS201.1, U205.8 (Rsl)
unnamed: U205.5 (Vref), VREF201.1
unnamed: P302.4, U301.31 (P4)
unnamed: P302.2, U301.32 (P11)
unnamed: UARTCAN201.1, UARTCAN201.4, UARTCAN201.6
unnamed: UARTCAN202.1, UARTCAN202.4, UARTCAN202.6
unnamed: UARTCAN203.1, UARTCAN203.4, UARTCAN203.6

Notes on the sheet:
inout_user
Main
xilinx
