copperheadhq/copperhead/manual-tests/real-designs/examples/multichannel/drawn/board.kicad_sch

## KiCad design manual-tests/real-designs/examples/multichannel/drawn/board.kicad_sch (2026-08-26)

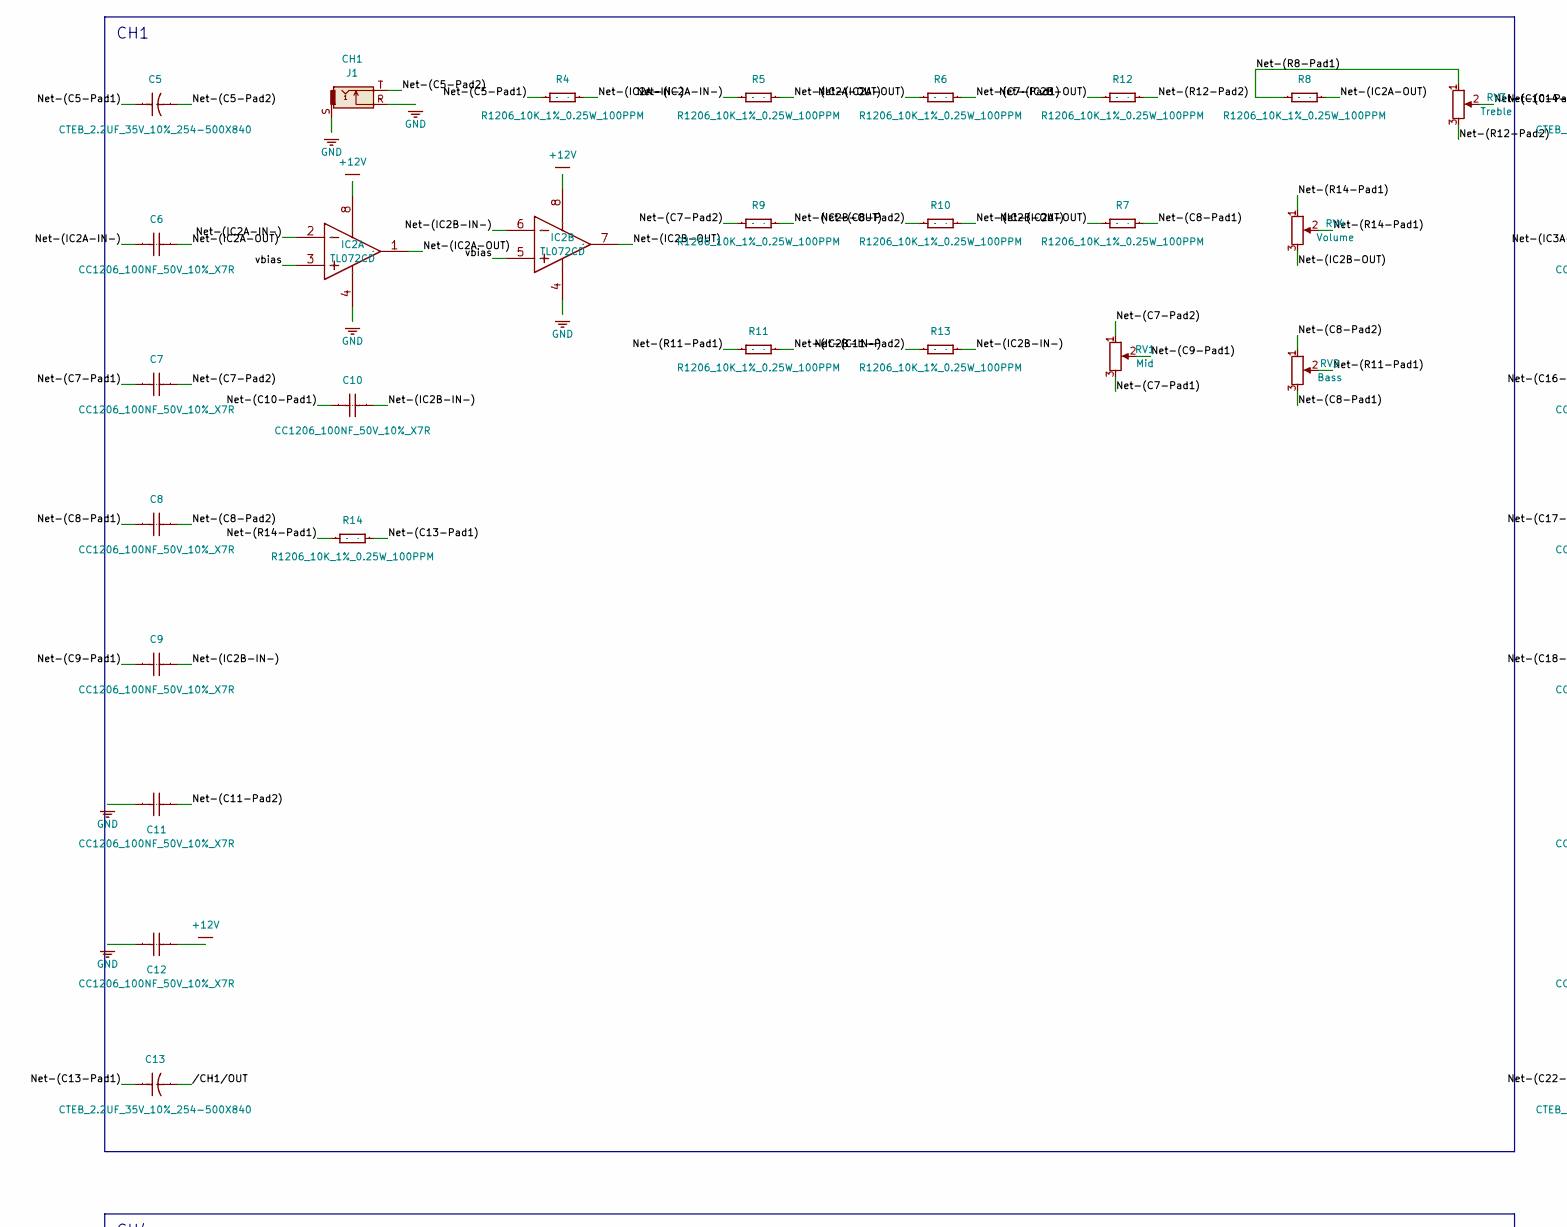
[picture p56: schematic board.kicad_sch, part in row 1, column 1]

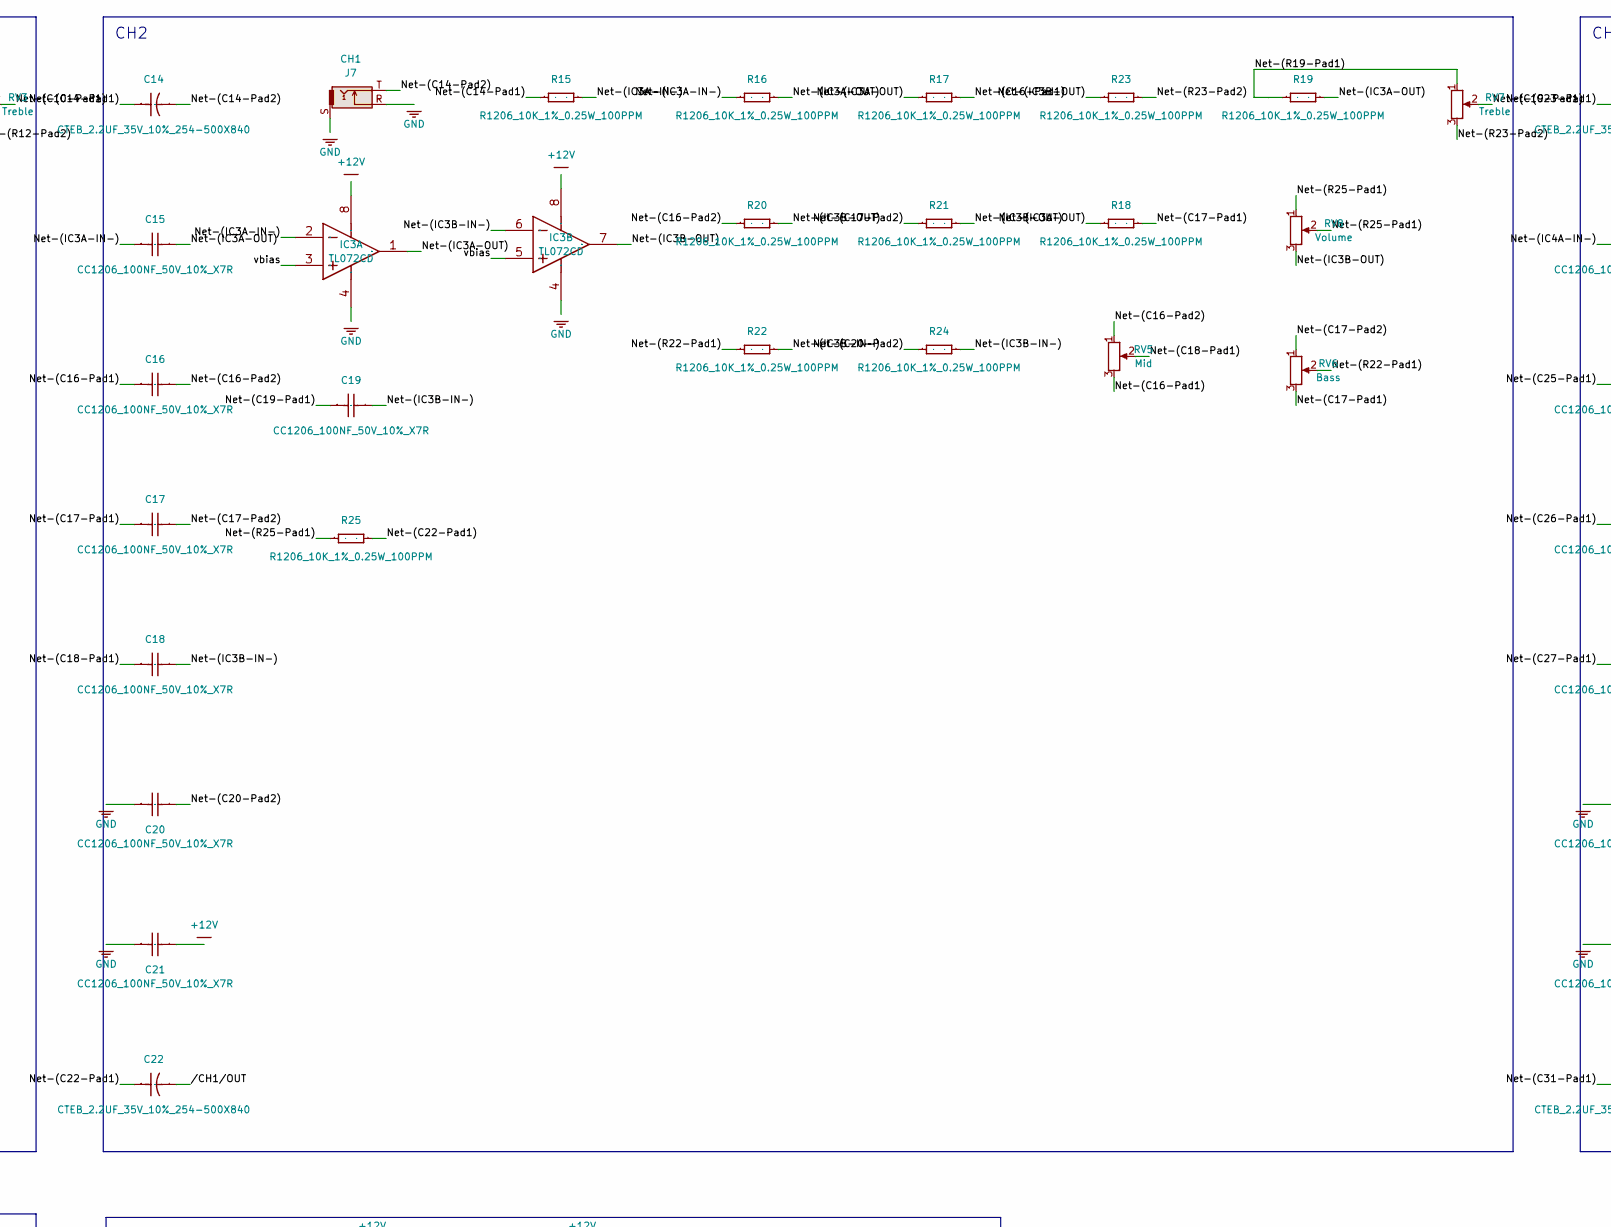
[picture p57: schematic board.kicad_sch, part in row 1, column 2]

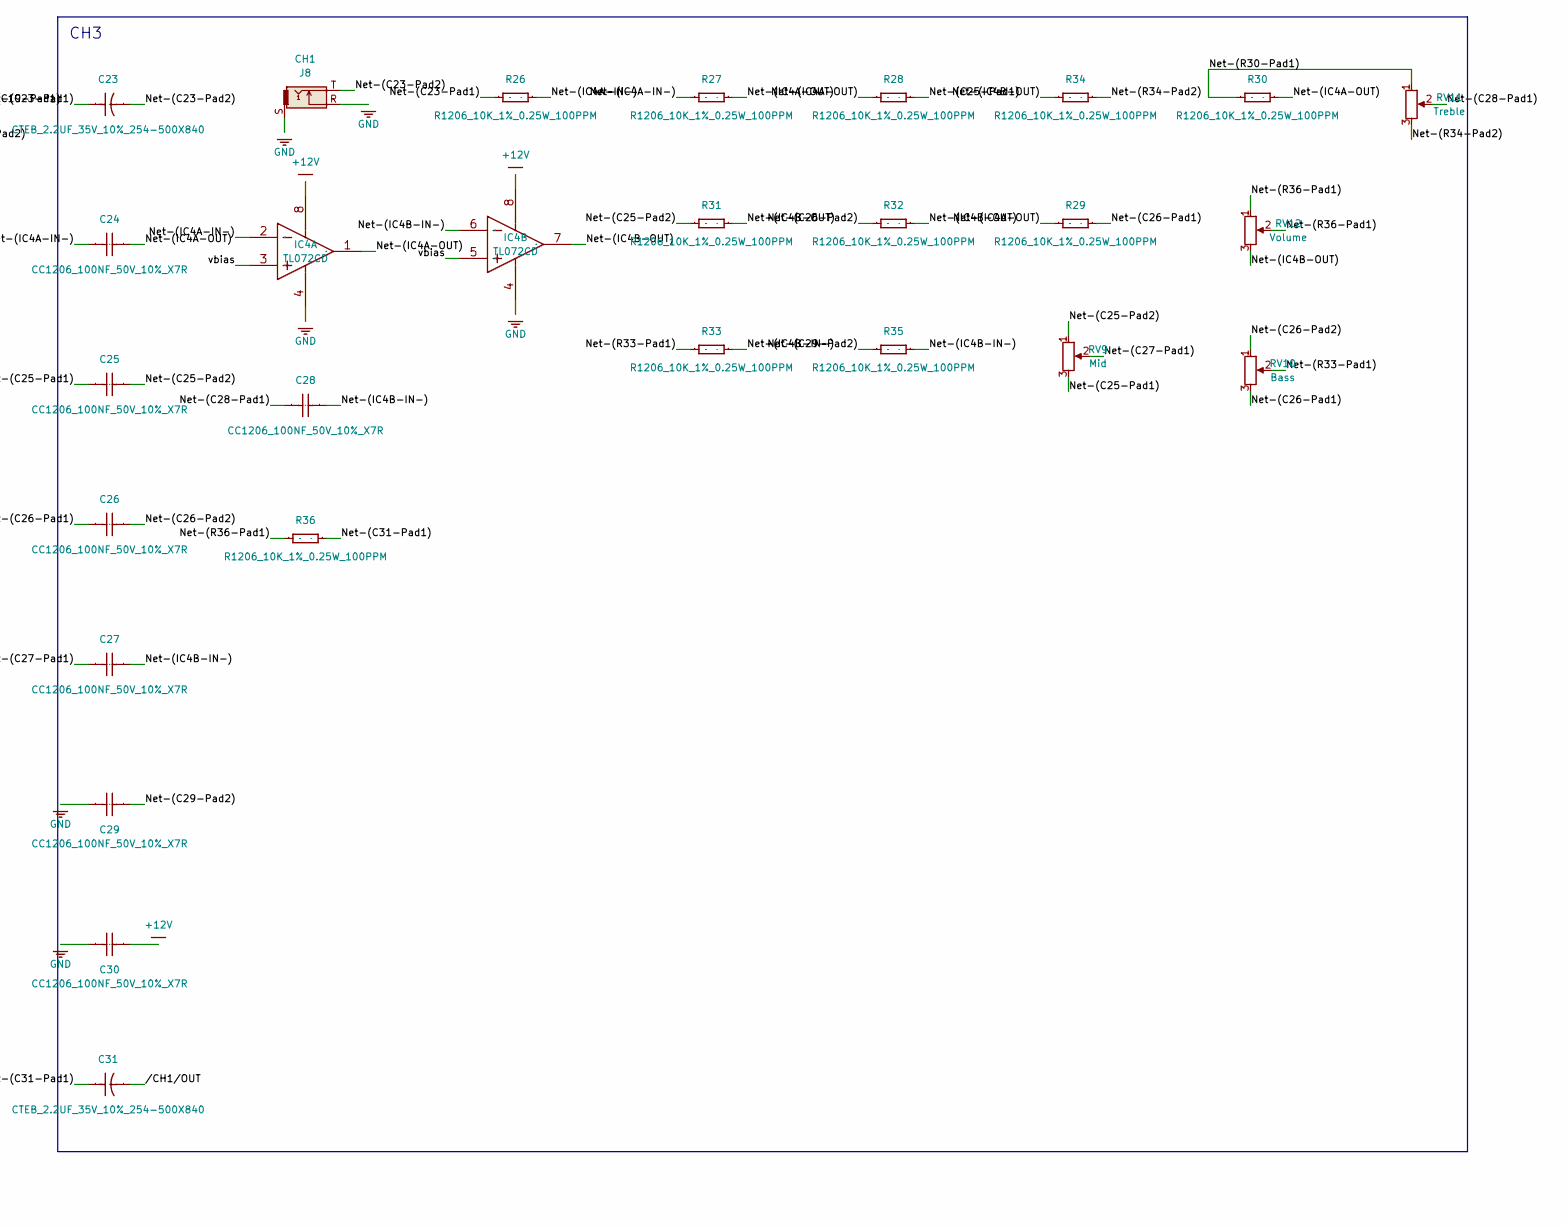
[picture p58: schematic board.kicad_sch, part in row 1, column 3]

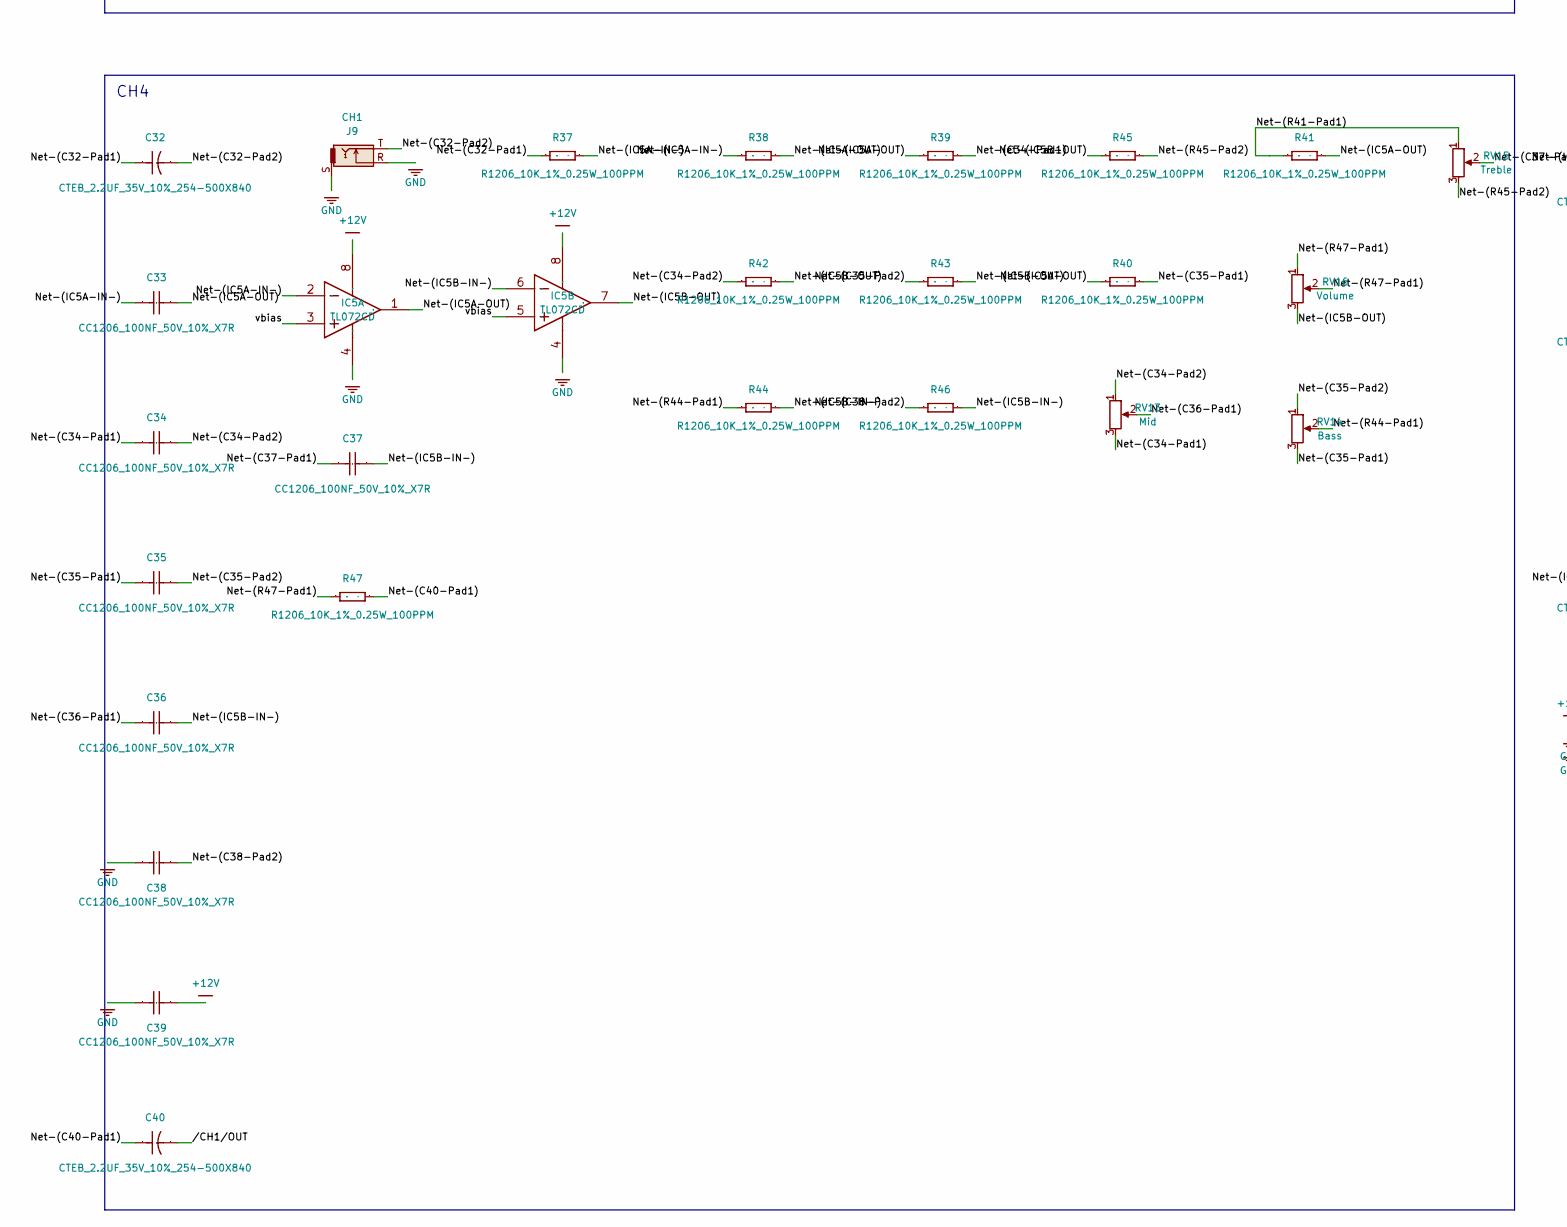
[picture p59: schematic board.kicad_sch, part in row 2, column 1]

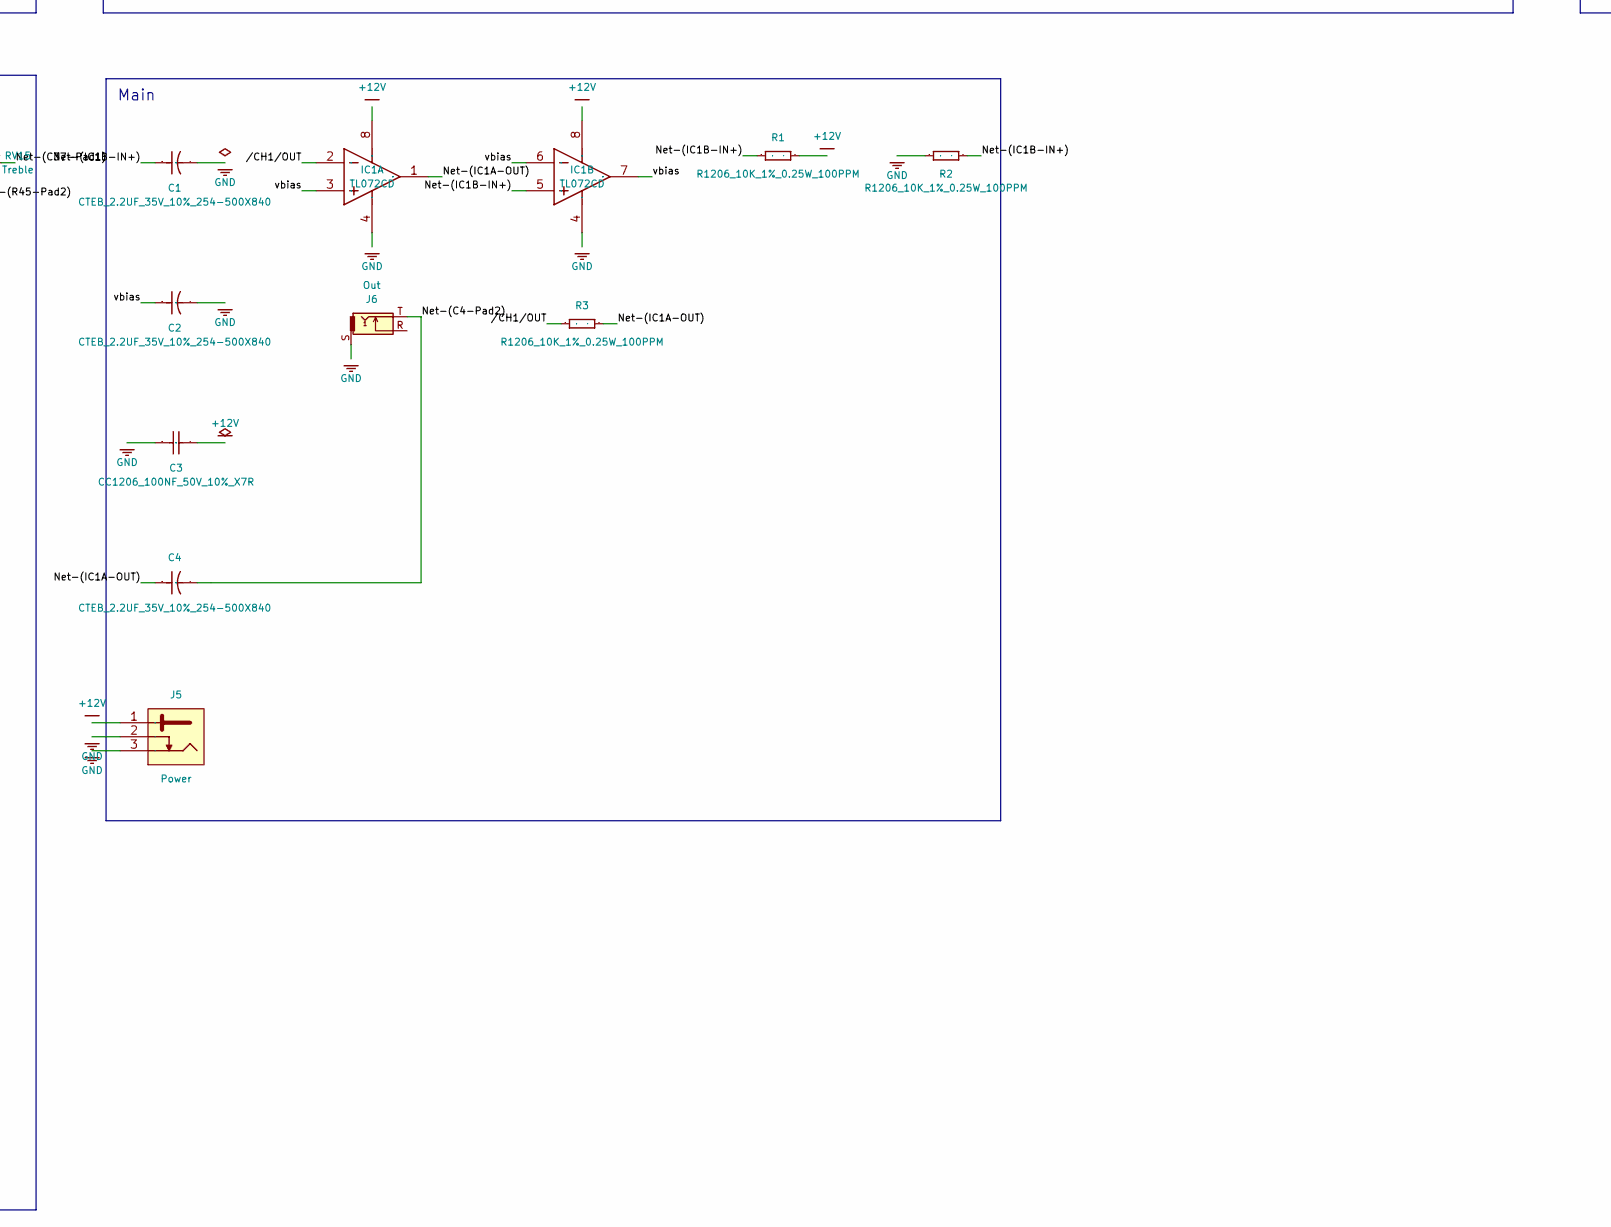
[picture p60: schematic board.kicad_sch, part in row 2, column 2]

Parts:
C1, C2, C4, C5, C13, C14, C22, C23, C31, C32, C40: CTEB_2.2UF_35V_10%_254-500X840; CAPPRB254-500X840
C3, C6, C7, C8, C9, C10, C11, C12, C15, C16, C17, C18, C19, C20, C21, C24, C25, C26, C27, C28, C29, C30, C33, C34, C35, C36, C37, C38, C39: CC1206_100NF_50V_10%_X7R; CAPC3216X140N
IC1, IC2, IC3, IC4, IC5: TL072CD; SOIC127P600X175-8N
J1, J7, J8, J9: CH1; Jack_6.35mm_Neutrik_NMJ6HCD2_Horizontal
J5: Power; CLIFF_FC68148(DC-10A)
J6: Out; Jack_6.35mm_Neutrik_NMJ6HCD2_Horizontal
R1, R2, R3, R4, R5, R6, R7, R8, R9, R10, R11, R12, R13, R14, R15, R16, R17, R18, R19, R20, R21, R22, R23, R24, R25, R26, R27, R28, R29, R30, R31, R32, R33, R34, R35, R36, R37, R38, R39, R40, R41, R42, R43, R44, R45, R46, R47: R1206_10K_1%_0.25W_100PPM; RESC3216X65N
RV1, RV5, RV9, RV13: Mid; Potentiometer_Alps_RK09K_Single_Vertical
RV2, RV6, RV10, RV14: Bass; Potentiometer_Alps_RK09K_Single_Vertical
RV3, RV7, RV11, RV15: Treble; Potentiometer_Alps_RK09K_Single_Vertical
RV4, RV8, RV12, RV16: Volume; Potentiometer_Alps_RK09K_Single_Vertical

Connections:
+12V: C3.2, C12.2, C21.2, C30.2, C39.2, IC1.8 (V+), IC2.8 (V+), IC3.8 (V+), IC4.8 (V+), IC5.8 (V+), J5.1, R1.2
/CH1/OUT: C13.2, C22.2, C31.2, C40.2, IC1.2 (IN-), R3.1
GND: C1.2, C2.2, C3.1, C11.1, C12.1, C20.1, C21.1, C29.1, C30.1, C38.1, C39.1, IC1.4 (V-), IC2.4 (V-), IC3.4 (V-), IC4.4 (V-), IC5.4 (V-), J1.R, J1.S, J5.2, J5.3, J6.S, J7.R, J7.S, J8.R, J8.S, J9.R, J9.S, R2.1
unnamed: C4.2, J6.T
unnamed: C5.1, R4.1
unnamed: C5.2, J1.T
unnamed: C7.1, R6.2, RV1.3
unnamed: C7.2, R9.1, RV1.1
unnamed: C8.1, R7.2, RV2.3
unnamed: C8.2, R10.1, RV2.1
unnamed: C9.1, RV1.2
unnamed: C10.1, RV3.2
unnamed: C11.2, R13.1
unnamed: C13.1, R14.2
unnamed: C14.1, R15.1
unnamed: C14.2, J7.T
unnamed: C16.1, R17.2, RV5.3
unnamed: C16.2, R20.1, RV5.1
unnamed: C17.1, R18.2, RV6.3
unnamed: C17.2, R21.1, RV6.1
unnamed: C18.1, RV5.2
unnamed: C19.1, RV7.2
unnamed: C20.2, R24.1
unnamed: C22.1, R25.2
unnamed: C23.1, R26.1
unnamed: C23.2, J8.T
unnamed: C25.1, R28.2, RV9.3
unnamed: C25.2, R31.1, RV9.1
unnamed: C26.1, R29.2, RV10.3
unnamed: C26.2, R32.1, RV10.1
unnamed: C27.1, RV9.2
unnamed: C28.1, RV11.2
unnamed: C29.2, R35.1
unnamed: C31.1, R36.2
unnamed: C32.1, R37.1
unnamed: C32.2, J9.T
unnamed: C34.1, R39.2, RV13.3
unnamed: C34.2, R42.1, RV13.1
unnamed: C35.1, R40.2, RV14.3
unnamed: C35.2, R43.1, RV14.1
unnamed: C36.1, RV13.2
unnamed: C37.1, RV15.2
unnamed: C38.2, R46.1
unnamed: C40.1, R47.2
unnamed: C4.1, IC1.1 (OUT), R3.2
unnamed: C1.1, IC1.5 (IN+), R1.1, R2.2
unnamed: C6.1, IC2.2 (IN-), R4.2, R5.1
unnamed: C6.2, IC2.1 (OUT), R5.2, R6.1, R7.1, R8.2
unnamed: C9.2, C10.2, IC2.6 (IN-), R11.2, R13.2
unnamed: IC2.7 (OUT), R9.2, R10.2, R12.1, RV4.3
unnamed: C15.1, IC3.2 (IN-), R15.2, R16.1
unnamed: C15.2, IC3.1 (OUT), R16.2, R17.1, R18.1, R19.2
unnamed: C18.2, C19.2, IC3.6 (IN-), R22.2, R24.2
unnamed: IC3.7 (OUT), R20.2, R21.2, R23.1, RV8.3
unnamed: C24.1, IC4.2 (IN-), R26.2, R27.1
unnamed: C24.2, IC4.1 (OUT), R27.2, R28.1, R29.1, R30.2
unnamed: C27.2, C28.2, IC4.6 (IN-), R33.2, R35.2
unnamed: IC4.7 (OUT), R31.2, R32.2, R34.1, RV12.3
unnamed: C33.1, IC5.2 (IN-), R37.2, R38.1
unnamed: C33.2, IC5.1 (OUT), R38.2, R39.1, R40.1, R41.2
unnamed: C36.2, C37.2, IC5.6 (IN-), R44.2, R46.2
unnamed: IC5.7 (OUT), R42.2, R43.2, R45.1, RV16.3
unnamed: R8.1, RV3.1
unnamed: R11.1, RV2.2
unnamed: R12.2, RV3.3
unnamed: R14.1, RV4.1, RV4.2
unnamed: R19.1, RV7.1
unnamed: R22.1, RV6.2
unnamed: R23.2, RV7.3
unnamed: R25.1, RV8.1, RV8.2
unnamed: R30.1, RV11.1
unnamed: R33.1, RV10.2
unnamed: R34.2, RV11.3
unnamed: R36.1, RV12.1, RV12.2
unnamed: R41.1, RV15.1
unnamed: R44.1, RV14.2
unnamed: R45.2, RV15.3
unnamed: R47.1, RV16.1, RV16.2
vbias: C2.1, IC1.3 (IN+), IC1.6 (IN-), IC1.7 (OUT), IC2.3 (IN+), IC2.5 (IN+), IC3.3 (IN+), IC3.5 (IN+), IC4.3 (IN+), IC4.5 (IN+), IC5.3 (IN+), IC5.5 (IN+)

Notes on the sheet:
CH1
CH2
CH3
CH4
Main
