copperheadhq/copperhead/manual-tests/real-designs/examples/royalblue54L_feather/drawn/board.kicad_sch

## KiCad design manual-tests/real-designs/examples/royalblue54L_feather/drawn/board.kicad_sch (2026-08-09)

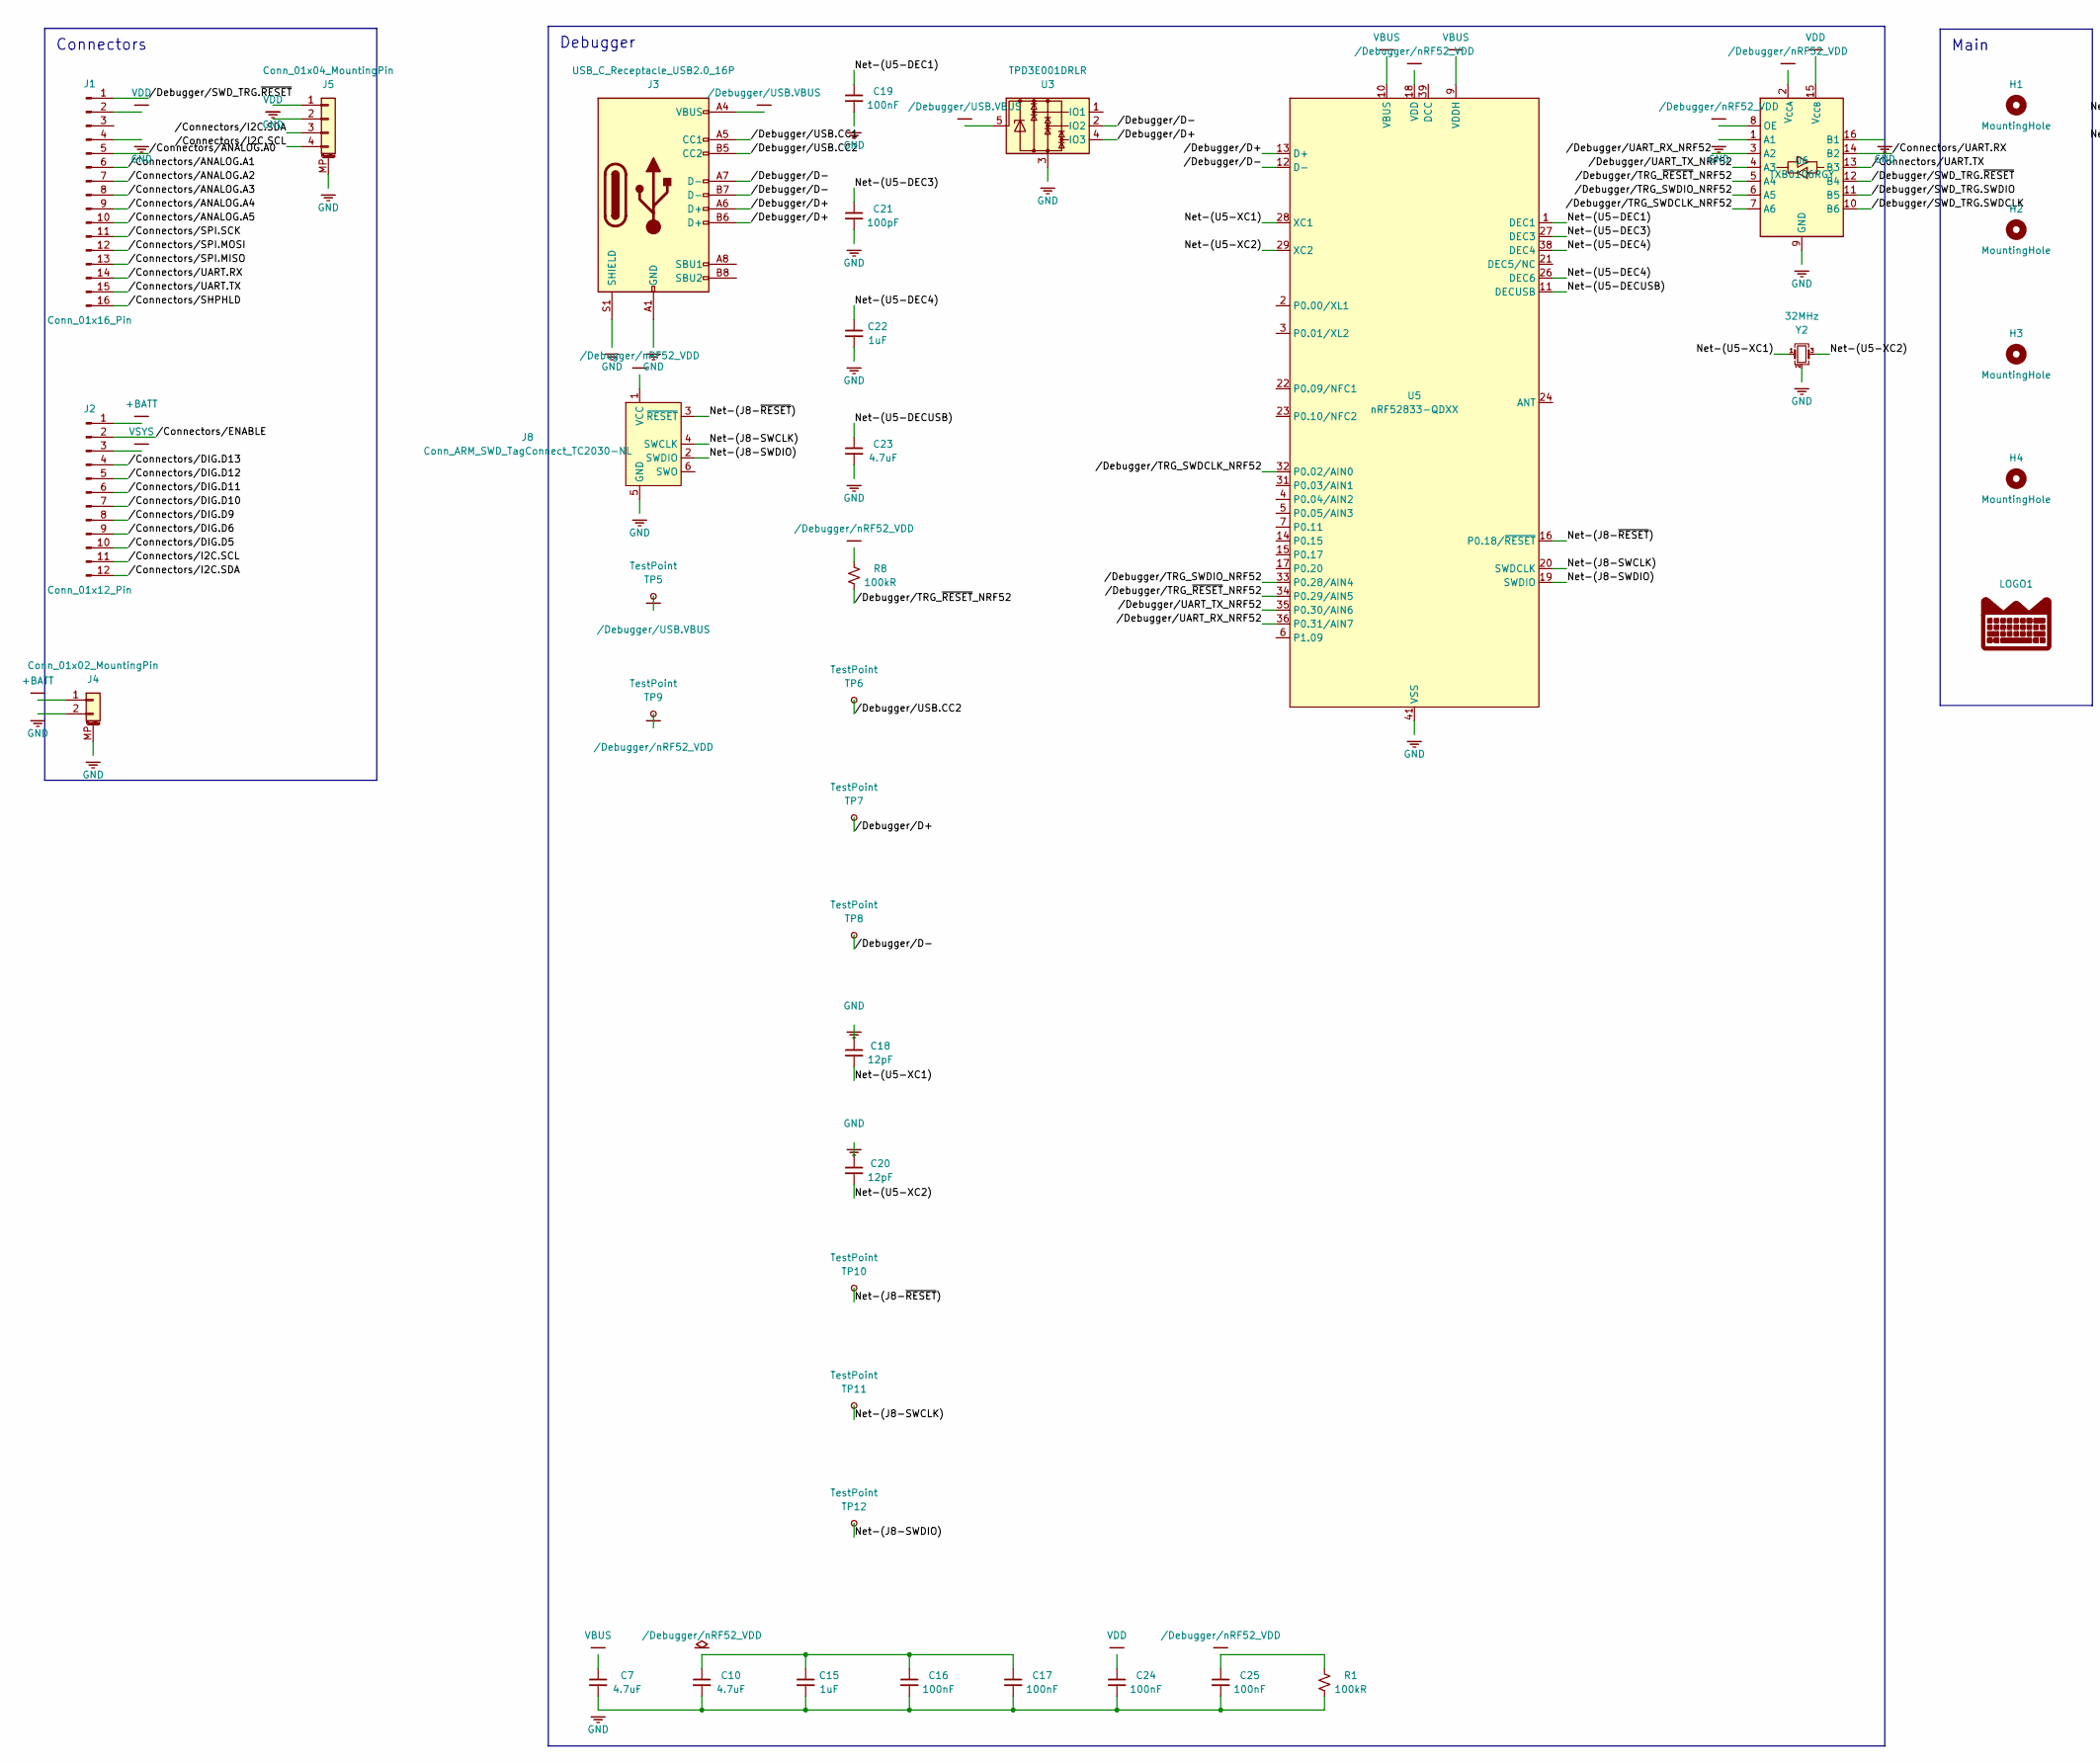
[picture p64: schematic board.kicad_sch, part in row 1, column 1]

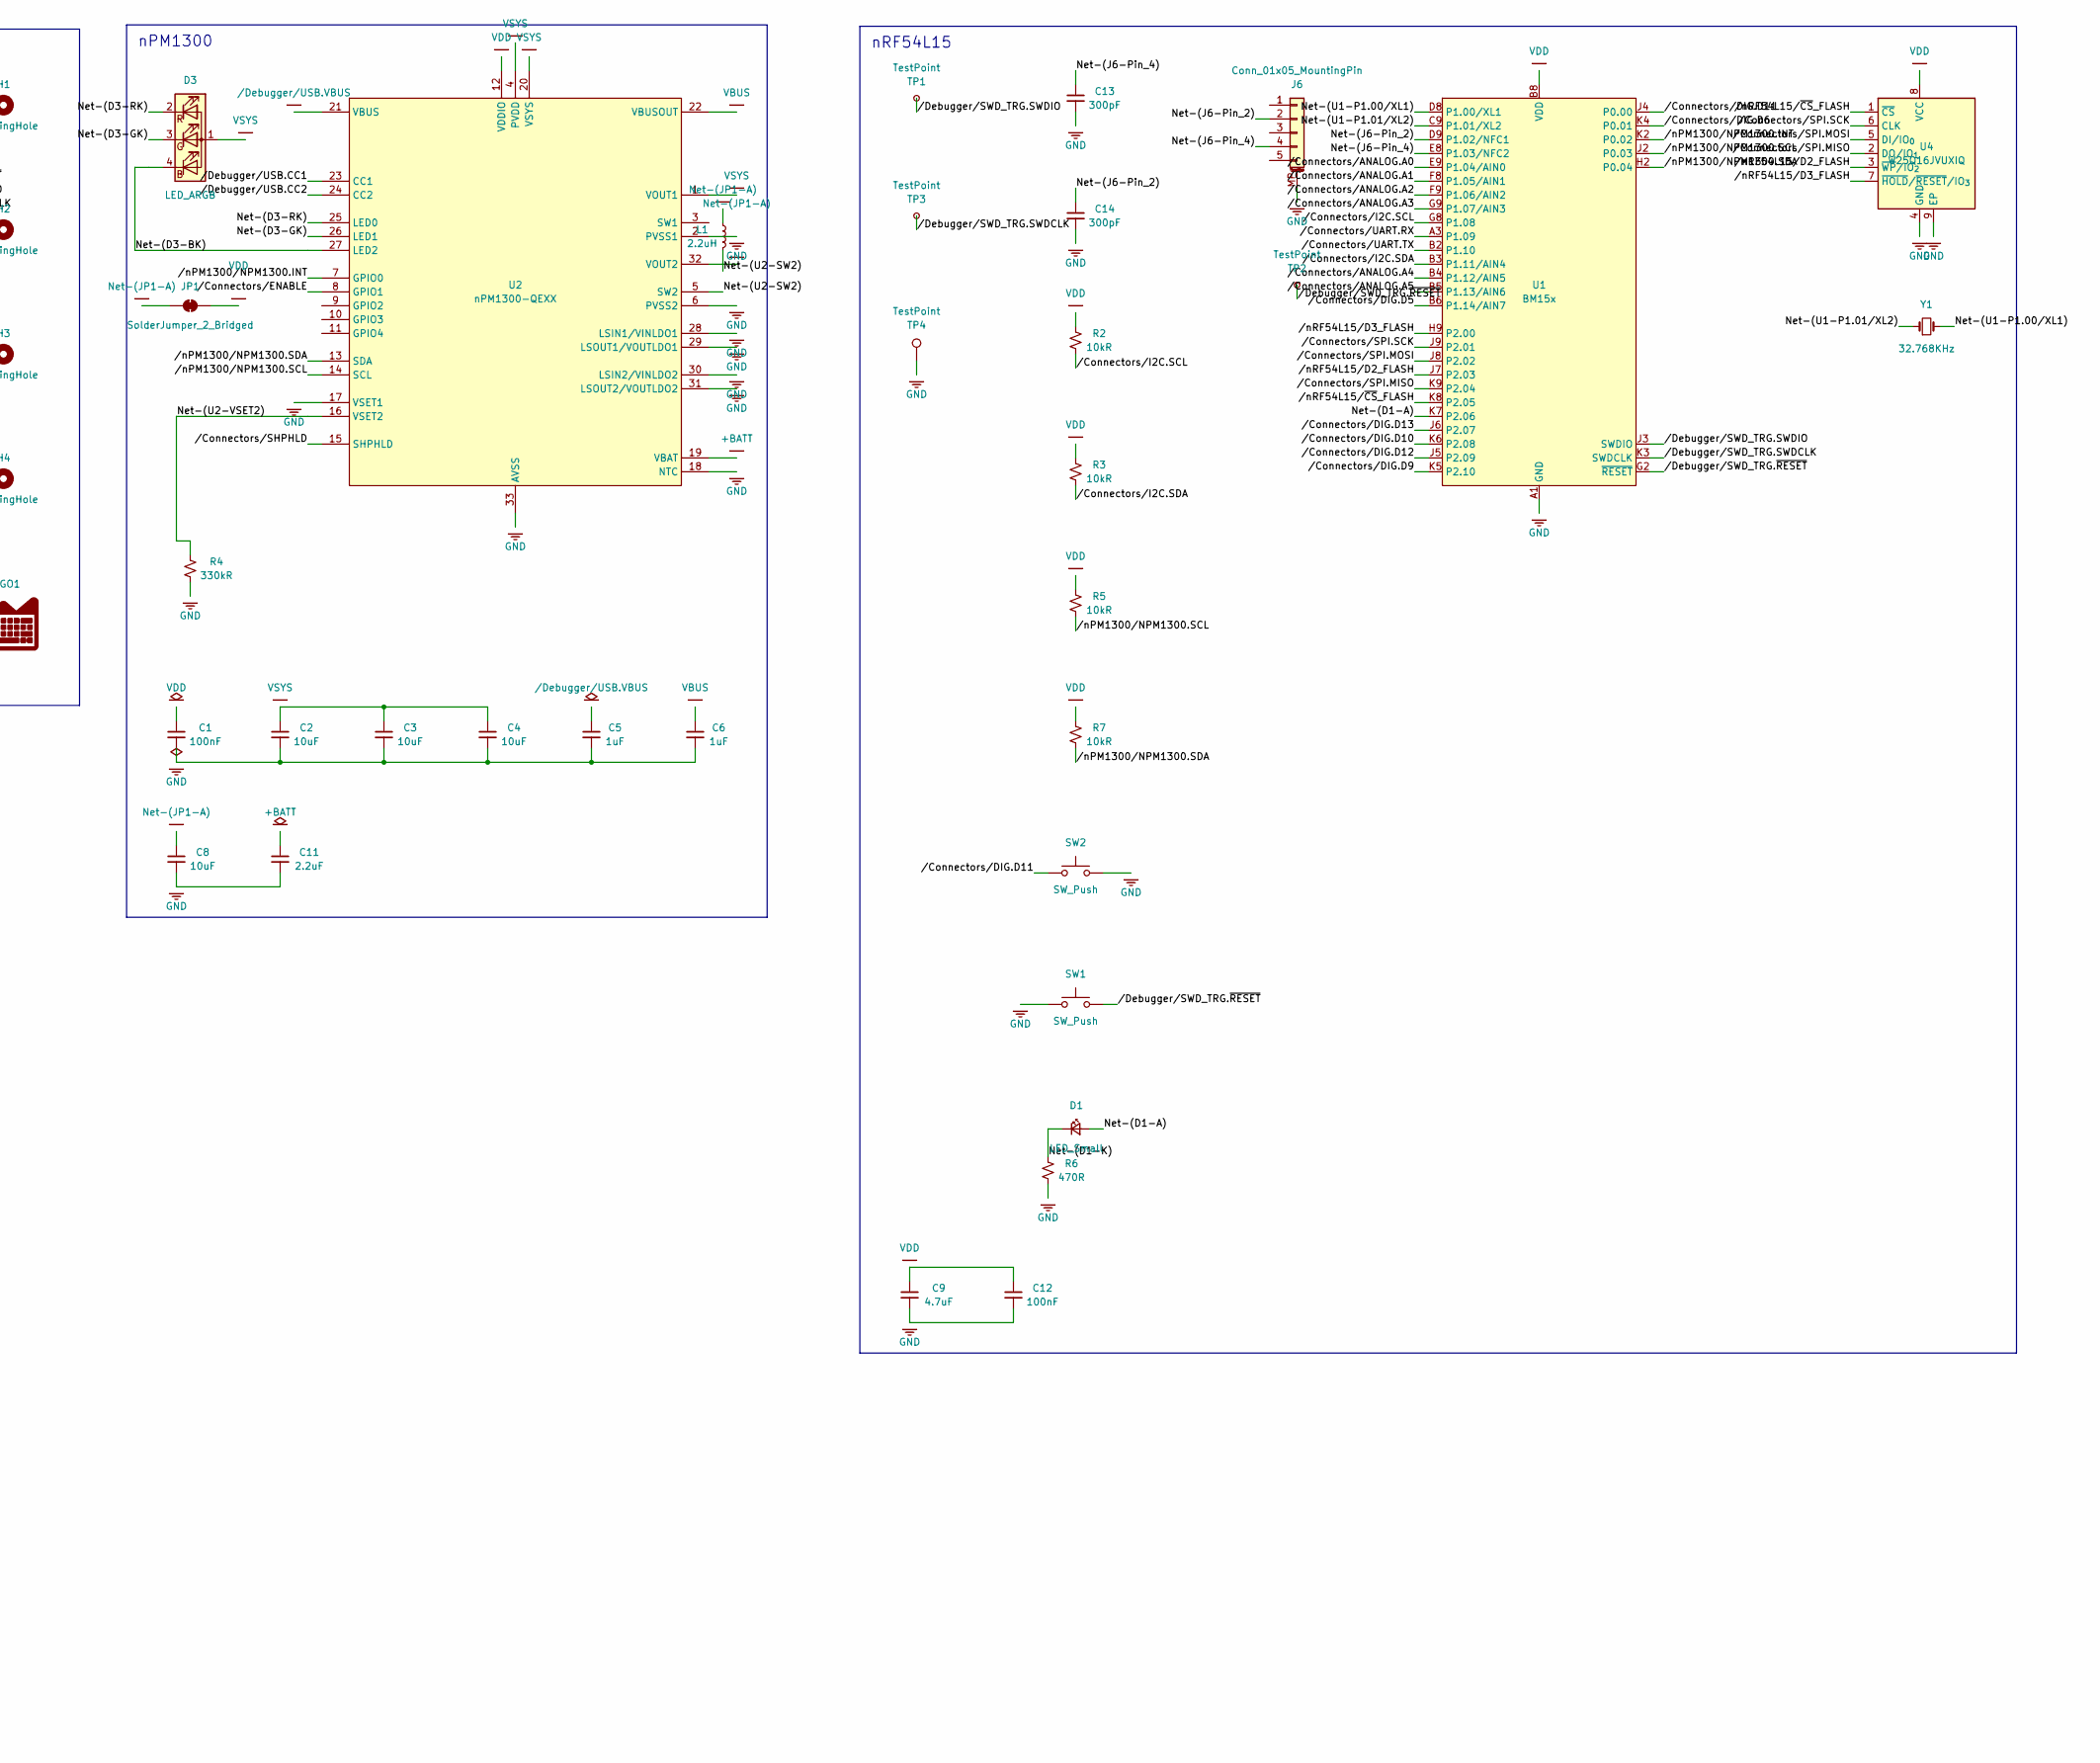
[picture p65: schematic board.kicad_sch, part in row 1, column 2]

Parts:
C1, C12, C16, C17, C19, C24, C25: 100nF; C_0402_1005Metric
C2, C3, C4, C8: 10uF; C_0603_1608Metric
C5, C6: 1uF; C_0603_1608Metric
C7, C9, C10, C23: 4.7uF; C_0402_1005Metric
C11: 2.2uF; C_0603_1608Metric
C13, C14: 300pF; C_0402_1005Metric
C15, C22: 1uF; C_0402_1005Metric
C18, C20: 12pF; C_0402_1005Metric
C21: 100pF; C_0402_1005Metric
D1: LED_Small; LED_0603_1608Metric
D3: LED_ARGB; LED_Wurth_150044M155260
H1, H2, H3, H4: MountingHole; MountingHole_2.5mm
J1: Conn_01x16_Pin; PinHeader_1x16_P2.54mm_Vertical
J2: Conn_01x12_Pin; PinHeader_1x12_P2.54mm_Vertical
J3: USB_C_Receptacle_USB2.0_16P; USB_C_Receptacle_HRO_TYPE-C-31-M-12
J4: Conn_01x02_MountingPin; JST_PH_S2B-PH-SM4-TB_1x02-1MP_P2.00mm_Horizontal
J5: Conn_01x04_MountingPin; JST_SH_SM04B-SRSS-TB_1x04-1MP_P1.00mm_Horizontal
J6: Conn_01x05_MountingPin; CONN-SMD_5P-P0.50_HCTL_HC-FPC-05-09-5RLTAG
J8: Conn_ARM_SWD_TagConnect_TC2030-NL; Tag-Connect_TC2030-IDC-NL_2x03_P1.27mm_Vertical
JP1: SolderJumper_2_Bridged; SolderJumper-2_P1.3mm_Bridged_RoundedPad1.0x1.5mm
L1: 2.2uH; L_0603_1608Metric
LOGO1: LordsBoardsLogo_Small_Silk
R1, R8: 100kR; R_0402_1005Metric
R2, R3, R5, R7: 10kR; R_0402_1005Metric
R4: 330kR; R_0402_1005Metric
R6: 470R; R_0402_1005Metric
SW1, SW2: SW_Push; SW_Push_1P1T_NO_Vertical_Wuerth_434133025816
TP1, TP2, TP3, TP4: TestPoint; TestPoint_Pad_D2.0mm
TP5, TP6, TP7, TP8, TP9, TP10, TP11, TP12: TestPoint; TestPoint_Pad_D1.5mm
U1: BM15x; BM15x-LGA-45_15.8x10mm
U2: nPM1300-QEXX; QFN-32-1EP_5x5mm_P0.5mm_EP3.6x3.6mm_ThermalVias
U3: TPD3E001DRLR; SOT-553
U4: W25Q16JVUXIQ; Winbond_USON-8-1EP_3x2mm_P0.5mm_EP0.2x1.6mm
U5: nRF52833-QDXX; QFN-40-1EP_5x5mm_P0.4mm_EP3.6x3.6mm_ThermalVias
U6: TXB0106RGY; Texas_RGY_R-PVQFN-N16_EP2.05x2.55mm
Y1: 32.768KHz; Crystal_SMD_3215-2Pin_3.2x1.5mm
Y2: 32MHz; Crystal_SMD_2016-4Pin_2.0x1.6mm

Connections:
+BATT: C11.1, J2.1, J4.1, U2.19 (VBAT)
/Connectors/ANALOG.A0: J1.5, U1.E9 (P1.04/AIN0)
/Connectors/ANALOG.A1: J1.6, U1.F8 (P1.05/AIN1)
/Connectors/ANALOG.A2: J1.7, U1.F9 (P1.06/AIN2)
/Connectors/ANALOG.A3: J1.8, U1.G9 (P1.07/AIN3)
/Connectors/ANALOG.A4: J1.9, U1.B4 (P1.12/AIN5)
/Connectors/ANALOG.A5: J1.10, U1.B5 (P1.13/AIN6)
/Connectors/DIG.D5: J2.10, U1.B6 (P1.14/AIN7)
/Connectors/DIG.D6: J2.9, U1.K4 (P0.01)
/Connectors/DIG.D9: J2.8, U1.K5 (P2.10)
/Connectors/DIG.D10: J2.7, U1.K6 (P2.08)
/Connectors/DIG.D11: J2.6, SW2.1, U1.J4 (P0.00)
/Connectors/DIG.D12: J2.5, U1.J5 (P2.09)
/Connectors/DIG.D13: J2.4, U1.J6 (P2.07)
/Connectors/ENABLE: J2.2, U2.8 (GPIO1)
/Connectors/I2C.SCL: J2.11, J5.4, R2.2, U1.G8 (P1.08)
/Connectors/I2C.SDA: J2.12, J5.3, R3.2, U1.B3 (P1.11/AIN4)
/Connectors/SHPHLD: J1.16, U2.15 (SHPHLD)
/Connectors/SPI.MISO: J1.13, U1.K9 (P2.04), U4.2 (DO/IO_{1})
/Connectors/SPI.MOSI: J1.12, U1.J8 (P2.02), U4.5 (DI/IO_{0})
/Connectors/SPI.SCK: J1.11, U1.J9 (P2.01), U4.6 (CLK)
/Connectors/UART.RX: J1.14, U1.A3 (P1.09), U6.14 (B2)
/Connectors/UART.TX: J1.15, U1.B2 (P1.10), U6.13 (B3)
/Debugger/D+: J3.A6 (D+), J3.B6 (D+), TP7.1, U3.4 (IO3), U5.13 (D+)
/Debugger/D-: J3.A7 (D-), J3.B7 (D-), TP8.1, U3.2 (IO2), U5.12 (D-)
/Debugger/SWD_TRG.SWDCLK: TP3.1, U1.K3 (SWDCLK), U6.10 (B6)
/Debugger/SWD_TRG.SWDIO: TP1.1, U1.J3 (SWDIO), U6.11 (B5)
/Debugger/SWD_TRG.~RESET: J1.1, SW1.2, TP2.1, U1.G2 (~RESET), U6.12 (B4)
/Debugger/TRG_SWDCLK_NRF52: U5.32 (P0.02/AIN0), U6.7 (A6)
/Debugger/TRG_SWDIO_NRF52: U5.33 (P0.28/AIN4), U6.6 (A5)
/Debugger/TRG_~RESET_NRF52: R8.2, U5.34 (P0.29/AIN5), U6.5 (A4)
/Debugger/UART_RX_NRF52: U5.36 (P0.31/AIN7), U6.3 (A2)
/Debugger/UART_TX_NRF52: U5.35 (P0.30/AIN6), U6.4 (A3)
/Debugger/USB.CC1: J3.A5 (CC1), U2.23 (CC1)
/Debugger/USB.CC2: J3.B5 (CC2), TP6.1, U2.24 (CC2)
/Debugger/USB.VBUS: C5.1, J3.A4 (VBUS), J3.A9 (VBUS), J3.B4 (VBUS), J3.B9 (VBUS), TP5.1, U2.21 (VBUS), U3.5
/Debugger/nRF52_VDD: C10.1, C15.1, C16.1, C17.1, C25.1, J8.1 (VCC), R1.1, R8.1, TP9.1, U5.8 (VDD), U5.18 (VDD), U5.30 (VDD), U5.40 (VDD), U6.2 (V_{CCA}), U6.8 (OE)
/nPM1300/NPM1300.INT: U1.K2 (P0.02), U2.7 (GPIO0)
/nPM1300/NPM1300.SCL: R5.2, U1.J2 (P0.03), U2.14 (SCL)
/nPM1300/NPM1300.SDA: R7.2, U1.H2 (P0.04), U2.13 (SDA)
/nRF54L15/D2_FLASH: U1.J7 (P2.03), U4.3 (~WP/IO_{2})
/nRF54L15/D3_FLASH: U1.H9 (P2.00), U4.7 (~HOLD/~RESET/IO_{3})
/nRF54L15/~CS_FLASH: U1.K8 (P2.05), U4.1 (~CS)
GND: C1.2, C2.2, C3.2, C4.2, C5.2, C6.2, C7.2, C8.2, C9.2, C10.2, C11.2, C12.2, C13.2, C14.2, C15.2, C16.2, C17.2, C18.1, C19.2, C20.1, C21.2, C22.2, C23.2, C24.2, C25.2, J1.4, J3.A1 (GND), J3.A12 (GND), J3.B1 (GND), J3.B12 (GND), J3.S1 (SHIELD), J4.2, J4.MP (MountPin), J5.1, J5.MP (MountPin), J6.MP (MountPin), J8.5 (GND), R1.2, R4.2, R6.2, SW1.1, SW2.2, TP4.1, U1.A1 (GND), U1.A9 (GND), U1.B1 (GND), U1.B7 (GND), U1.B9 (GND), U1.D1 (GND), U1.E1 (GND), U1.F1 (GND), U1.H8 (GND), U2.2 (PVSS1), U2.6 (PVSS2), U2.17 (VSET1), U2.18 (NTC), U2.28 (LSIN1/VINLDO1), U2.29 (LSOUT1/VOUTLDO1), U2.30 (LSIN2/VINLDO2), U2.31 (LSOUT2/VOUTLDO2), U2.33 (AVSS), U3.3, U4.4 (GND), U4.9 (EP), U5.25 (VSS_PA), U5.37 (VSS), U5.41 (VSS), U6.1 (A1), U6.9 (GND), U6.16 (B1), U6.17 (GND), Y2.2, Y2.4
unnamed: D1.2 (A), U1.K7 (P2.06)
unnamed: D1.1 (K), R6.1
unnamed: D3.4 (BK), U2.27 (LED2)
unnamed: D3.3 (GK), U2.26 (LED1)
unnamed: D3.2 (RK), U2.25 (LED0)
unnamed: C14.1, J6.2, U1.D9 (P1.02/NFC1)
unnamed: C13.1, J6.4, U1.E8 (P1.03/NFC2)
unnamed: J8.4 (SWCLK), TP11.1, U5.20 (SWDCLK)
unnamed: J8.2 (SWDIO), TP12.1, U5.19 (SWDIO)
unnamed: J8.3 (~RESET), TP10.1, U5.16 (P0.18/~RESET)
unnamed: C8.1, JP1.1 (A), L1.1, U2.32 (VOUT2)
unnamed: U1.D8 (P1.00/XL1), Y1.2
unnamed: U1.C9 (P1.01/XL2), Y1.1
unnamed: L1.2, U2.5 (SW2)
unnamed: R4.1, U2.16 (VSET2)
unnamed: C19.1, U5.1 (DEC1)
unnamed: C21.1, U5.27 (DEC3)
unnamed: C22.1, U5.26 (DEC6), U5.38 (DEC4)
unnamed: C23.1, U5.11 (DECUSB)
unnamed: C18.2, U5.28 (XC1), Y2.1
unnamed: C20.2, U5.29 (XC2), Y2.3
VBUS: C6.1, C7.1, U2.22 (VBUSOUT), U5.9 (VDDH), U5.10 (VBUS)
VDD: C1.1, C9.1, C12.1, C24.1, J1.2, J5.2, JP1.2 (B), R2.1, R3.1, R5.1, R7.1, U1.B8 (VDD), U1.C8 (VDD), U2.12 (VDDIO), U4.8 (VCC), U6.15 (V_{CCB})
VSYS: C2.1, C3.1, C4.1, D3.1 (A), J2.3, U2.1 (VOUT1), U2.4 (PVDD), U2.20 (VSYS)

Notes on the sheet:
Connectors
Debugger
Main
nPM1300
nRF54L15
