copperheadhq/copperhead/manual-tests/real-designs/examples/sonde xilinx/drawn/board.kicad_sch

## KiCad design manual-tests/real-designs/examples/sonde xilinx/drawn/board.kicad_sch (2026-08-26)

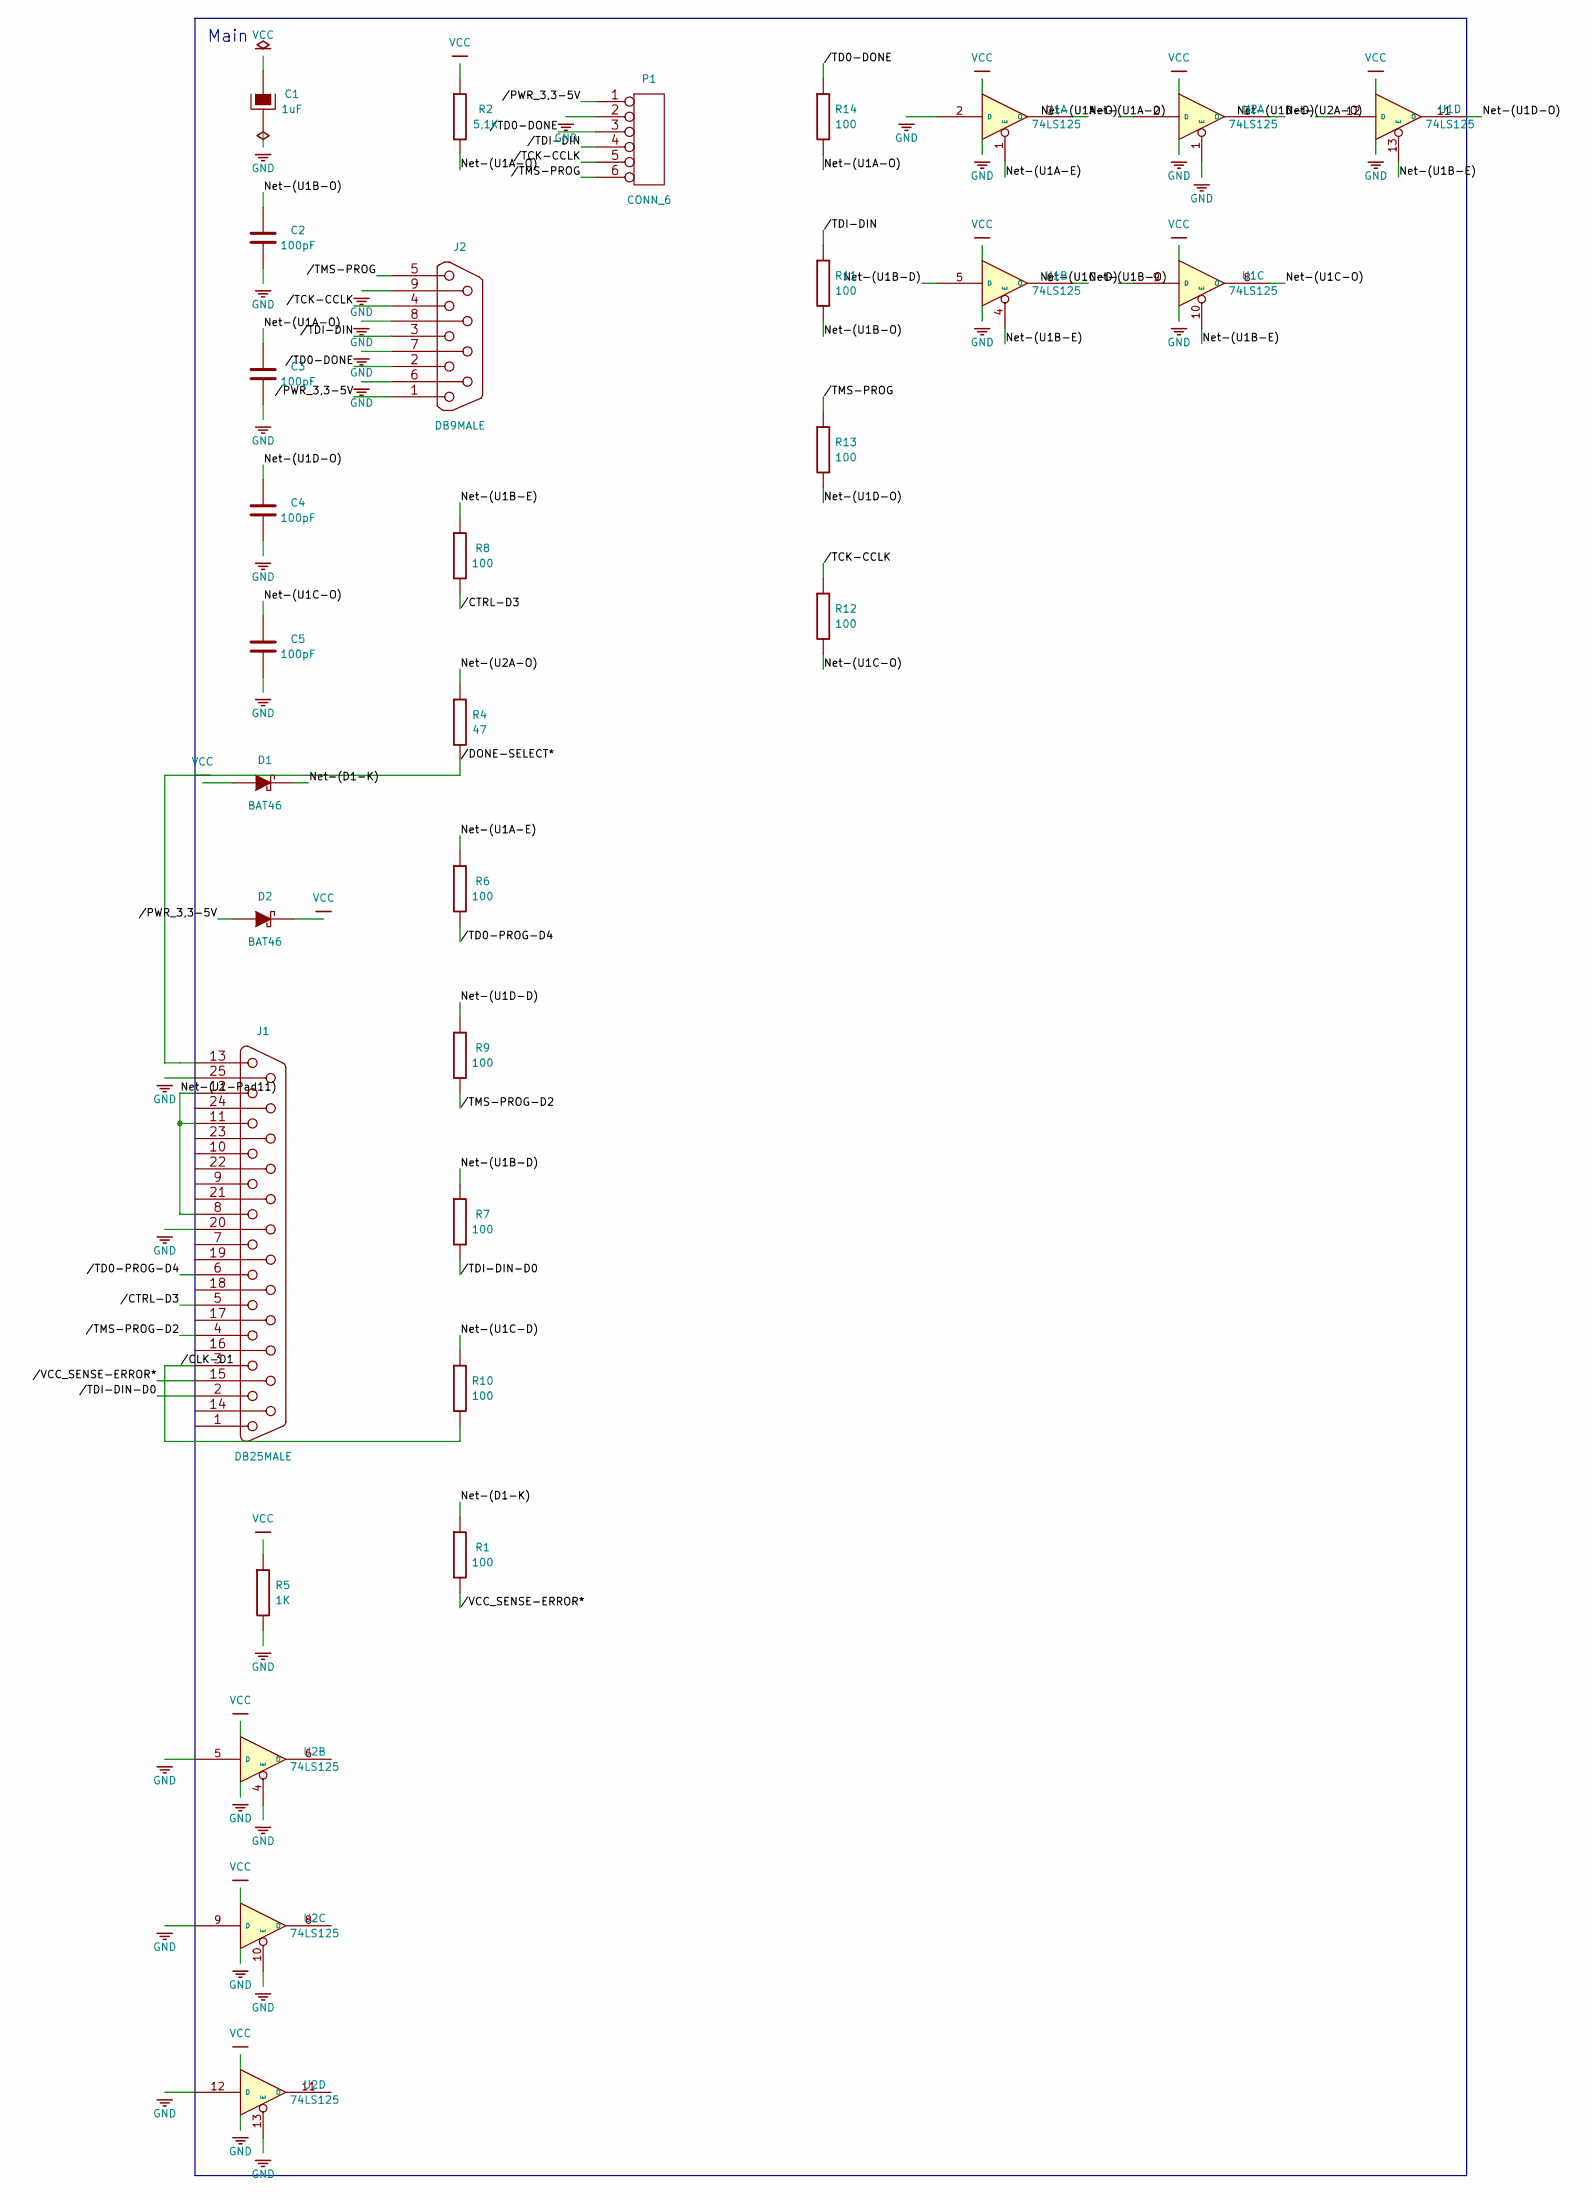
[picture p66: schematic board.kicad_sch]

Parts:
C1: 1uF; C_Axial_L5.1mm_D3.1mm_P12.50mm_Horizontal
C2, C3, C4, C5: 100pF; C_Disc_D5.1mm_W3.2mm_P5.00mm
D1, D2: BAT46; D_A-405_P7.62mm_Horizontal
J1: DB25MALE; DSUB-25_Male_EdgeMount_P2.77mm
J2: DB9MALE; DSUB-9_Male_EdgeMount_P2.77mm
P1: CONN_6; PinHeader_1x06_P2.54mm_Vertical
R1, R6, R7, R8, R9, R10, R11, R12, R13, R14: 100; R_Axial_DIN0207_L6.3mm_D2.5mm_P10.16mm_Horizontal
R2: 5,1K; R_Axial_DIN0207_L6.3mm_D2.5mm_P10.16mm_Horizontal
R4: 47; R_Axial_DIN0207_L6.3mm_D2.5mm_P10.16mm_Horizontal
R5: 1K; R_Axial_DIN0207_L6.3mm_D2.5mm_P10.16mm_Horizontal
U1, U2: 74LS125; DIP-14_W7.62mm_LongPads

Connections:
/CLK-D1: J1.3, R10.2
/CTRL-D3: J1.5, R8.2
/DONE-SELECT*: J1.13, R4.2
/PWR_3,3-5V: D2.1 (A), J2.1, P1.1
/TCK-CCLK: J2.4, P1.5, R12.1
/TD0-DONE: J2.2, P1.3, R14.1
/TD0-PROG-D4: J1.6, R6.2
/TDI-DIN: J2.3, P1.4, R11.1
/TDI-DIN-D0: J1.2, R7.2
/TMS-PROG: J2.5, P1.6, R13.1
/TMS-PROG-D2: J1.4, R9.2
/VCC_SENSE-ERROR*: J1.15, R1.2
GND: C1.2, C2.2, C3.2, C4.2, C5.2, J1.20, J1.25, J2.6, J2.7, J2.8, J2.9, P1.2, R5.2, U1.2 (D), U1.7 (GND), U2.1 (E), U2.4 (E), U2.5 (D), U2.7 (GND), U2.9 (D), U2.10 (E), U2.12 (D), U2.13 (E)
unnamed: D1.2 (K), R1.1
unnamed: J1.8, J1.11, J1.12
unnamed: R6.1, U1.1 (E)
unnamed: C3.1, R2.2, R14.2, U1.3 (O), U2.2 (D)
unnamed: R7.1, U1.5 (D)
unnamed: R8.1, U1.4 (E), U1.10 (E), U1.13 (E)
unnamed: C2.1, R11.2, U1.6 (O)
unnamed: R10.1, U1.9 (D)
unnamed: C5.1, R12.2, U1.8 (O)
unnamed: R9.1, U1.12 (D)
unnamed: C4.1, R13.2, U1.11 (O)
unnamed: R4.1, U2.3 (O)
VCC: C1.1, D1.1 (A), D2.2 (K), R2.1, R5.1, U1.14 (VCC), U2.14 (VCC)

Notes on the sheet:
Main
