copperheadhq/copperhead/manual-tests/real-designs/examples/tiny_tapeout/drawn/board.kicad_sch

## KiCad design manual-tests/real-designs/examples/tiny_tapeout/drawn/board.kicad_sch (2026-08-26)

Schematic: board.kicad_sch

Parts:
C1, C5, C9, C11, C15, C17, C25, C32, C37, C42, C57, C59, C61: 1uF; C_0603_1608Metric
C2, C4, C8, C12, C13, C14, C18, C19, C20, C22, C23, C24, C26, C27, C28, C31, C33, C34, C35, C36, C38, C39, C40, C41, C43, C56, C58, C60: 100nF; C_0402_1005Metric
C3: 6800pF; C_0603_1608Metric
C6, C7: 10uF; C_0805_2012Metric
C10: 22uF; C_0805_2012Metric
C16, C21: 10uF; C_0603_1608Metric
C29, C30: 6pF; C_0402_1005Metric
D1, D2, D3, D4: Yellow; LED_0603_1608Metric
F1: 350mA; Fuse_0805_2012Metric
FID1, FID2, FID3: Fiducial; Fiducial_1mm_Mask2mm
J1: Conn_01x06; PinHeader_1x06_P2.54mm_Vertical
J2: Conn_01x04; PinHeader_1x04_P2.54mm_Vertical
J3, J5, J6, J12, J13, J14: 613012243121; PinSocket_2x06_P2.54mm_PMODHost1A
J4: TT04_BREAKOUT_REVB; TT04_BREAKOUT_SMB
J7: Conn_01x02; PinHeader_1x02_P2.54mm_Vertical_SMD_Pin1Right
J8, J17: Conn_01x03; PinHeader_1x03_P2.54mm_Vertical
J9: Conn_01x24; PinHeader_1x24_P2.54mm_Vertical
J10: Conn_01x02; PinHeader_1x02_P2.54mm_Vertical
J11: Conn_01x06; PinHeader_1x06_P2.54mm_Vertical_SMD_Pin1Right
J15: USB4500-03-0-A_REVA; GCT_USB4500-03-0-A_REVA
J16, J18: 2x20_P2.54mm_Pinheader; TT_BREAKOUT_PINHEADER_PLACEHOLDER_WITHPAD
JP1, JP2, JP3, JP4, JP5, JP6, JP7, JP8: SolderJumper_2_Bridged; SolderJumper-2_Bridged_Throughole1
MT1, MT2, MT3, MT4: MountingHole_Pad; MountingHole_3.2mm_M3_Pad
NT1: NetTie_2; NetTie-2_SMD_Pad0.5mm
R1, R2, R3, R4, R5, R6, R10, R11, R13, R14, R37: 1k; R_0402_1005Metric
R7: 47k; R_0603_1608Metric
R8, R9, R12, R30, R31, R32, R33, R34, R35, R36, R38, R39, R40, R42, R43, R44, R45, R46, R47, R48: 10k; R_0402_1005Metric
R15: 1.2K; R_0402_1005Metric
R16: 1M; R_0603_1608Metric
R17, R19: 510; R_0402_1005Metric
R18: 0R; R_0402_1005Metric
R20, R21: 5.1k; R_0402_1005Metric
R22, R23, R24, R25, R26, R27, R28, R29: 68R; R_0402_1005Metric
R41: 47R; R_0402_1005Metric
SW1, SW2, SW3: 434121025816
SW4: 418121270808
TP1: TestPoint; TestPoint_Pad_D1.5mm
U1: 157112V12700; WL_S7DS-157112V12700
U2: TLV1117LV33; SOT-223-3_TabPin2
U3: AP2112K-1.8; SOT-23-5
U4: 74CBTLV3257; TSSOP-16_4.4x5mm_P0.65mm
U5, U7: W25Q32JVSS; SOIC-8_5.23x5.23mm_P1.27mm
U6: RP2040; QFN-56-1EP_7x7mm_P0.4mm_EP3.2x3.2mm
X1: 20MHz; Oscillator_SMD_ECS_2520MV-xxx-xx-4Pin_2.5x2.0mm
Y1: 12.0MHz; Crystal_SMD_3225-4Pin_3.2x2.5mm

Connections:
+1V8: C11.1, C13.1, C20.2, C21.2, C22.2, C24.2, C25.2, J4.A7 (VCCD), J4.B14 (VCCD2), J4.B16 (VCCD2), J4.B33 (VCCD1), J4.B35 (VCCD1), J9.2, R18.1, U3.5 (VOUT)
+3V3: C1.1, C4.1, C5.2, C7.1, C8.1, C9.2, C10.1, C12.1, C14.1, C15.2, C16.2, C17.2, C18.1, C19.2, C23.2, C26.2, C27.1, C28.2, C31.2, C33.1, C34.1, C35.1, C36.1, C37.1, C38.1, C39.1, C43.2, C56.1, C57.2, C58.1, C59.2, C60.1, C61.2, J3.6 (VCC), J3.12 (VCC), J4.A19 (VDDA), J4.B1 (VDDA2), J4.B3 (VDDA2), J4.B15 (VDDIO), J4.B17 (VDDIO), J4.B37 (VDDA1), J4.B39 (VDDA1), J5.6 (VCC), J5.12 (VCC), J6.6 (VCC), J6.12 (VCC), J9.3, J9.21, J11.1, J12.6 (VCC), J12.12 (VCC), J13.6 (VCC), J13.12 (VCC), J14.6 (VCC), J14.12 (VCC), R1.1, R2.1, R3.1, R4.1, R5.1, R6.1, R8.1, R9.1, R10.1, R11.1, R17.1, R19.1, R32.1, R33.1, R34.1, R35.1, R36.1, R38.1, R39.1, R40.1, R42.1, R43.1, R44.1, R45.1, R46.1, R47.1, R48.1, SW1.2, U2.2 (VO), U3.1 (VIN), U3.3 (EN), U4.16 (VCC), U5.8 (VCC), U6.1 (IOVDD), U6.10 (IOVDD), U6.22 (IOVDD), U6.33 (IOVDD), U6.42 (IOVDD), U6.43 (ADC_AVDD), U6.44 (VREG_IN), U6.48 (USB_VDD), U6.49 (IOVDD), U7.8 (VCC), X1.4 (VDD)
+5V: C6.1, F1.2, J1.2, J9.23, R15.1, U2.3 (VI)
/CC1: J15.A5 (CC1), R21.1
/CC2: J15.B5 (CC2), R20.1
/RP2040/DVDD: C32.2, C40.1, C41.1, U6.23 (DVDD), U6.45 (VREG_VOUT), U6.50 (DVDD)
/RP2040/QSPI_CLK: J11.3, R34.2, U5.6 (CLK), U6.52 (QSPI_SCLK)
/RP2040/QSPI_SD0: J11.4, R39.2, U5.5 (DI(IO0)), U6.53 (QSPI_SD0)
/RP2040/QSPI_SD1: J11.5, R40.2, U5.2 (DO(IO1)), U6.55 (QSPI_SD1)
/RP2040/QSPI_SD2: R35.2, U5.3 (IO2), U6.54 (QSPI_SD2)
/RP2040/QSPI_SD3: R38.2, U5.7 (IO3), U6.51 (QSPI_SD3)
/RP2040/RUN: J10.2, R36.2, U6.26 (RUN)
/RP2040/SWCLK: J7.2, U6.24 (SWCLK)
/RP2040/SWDIO: J7.1, U6.25 (SWD)
/~CRVRST: C42.2, J4.A12 (RST), R42.2, TP1.1
Caravel_CSB: J4.A14 (CARAVEL_CSB), R43.2, U7.1 (~CS)
Caravel_D0: J4.A16 (CARAVEL_D0), R46.2, U7.5 (DI(IO0))
Caravel_D1: J4.A17 (CARAVEL_D1), R47.2, U7.2 (DO(IO1))
Caravel_SCK: J4.A13 (CARAVEL_SCK), R48.2, U7.6 (CLK)
GND: C2.2, C3.2, C4.2, C5.1, C6.2, C7.2, C8.2, C9.1, C10.2, C11.2, C12.2, C13.2, C14.2, C15.1, C16.1, C17.1, C18.2, C19.1, C20.1, C21.1, C22.1, C23.1, C24.1, C25.1, C26.1, C27.2, C28.1, C29.2, C30.2, C31.1, C32.1, C33.2, C34.2, C35.2, C36.2, C37.2, C38.2, C39.2, C40.2, C41.2, C42.1, C43.1, C56.2, C57.1, C58.2, C59.1, C60.2, C61.1, D1.1 (K), D2.1 (K), D3.1 (K), J1.1, J3.5 (GND), J3.11 (GND), J4.A2 (GND), J4.A9 (GND), J4.A10 (GND), J4.A15 (GND), J4.A20 (GND), J4.A25 (GND), J4.A29 (GND), J4.A30 (GND), J4.A40 (GND), J4.B2 (GND), J4.B4 (GND), J4.B12 (GND), J4.B13 (GND), J4.B18 (GND), J4.B19 (GND), J4.B20 (GND), J4.B24 (GND), J4.B25 (GND), J4.B31 (GND), J4.B34 (GND), J4.B36 (GND), J4.B38 (GND), J4.B40 (GND), J5.5 (GND), J5.11 (GND), J6.5 (GND), J6.11 (GND), J9.1, J9.4, J9.8, J9.15, J9.19, J9.22, J9.24, J10.1, J11.6, J12.5 (GND), J12.11 (GND), J13.5 (GND), J13.11 (GND), J14.5 (GND), J14.11 (GND), J15.A1_B12 (GND), J15.B1_A12 (GND), MT1.1, MT2.1, MT3.1, MT4.1, R7.2, R14.2, R16.2, R20.2, R21.2, R30.2, R31.2, SW2.1, U1.3 (CC), U1.8 (CC), U2.1 (GND), U3.2 (GND), U4.8 (GND), U4.15 (~OE), U5.4 (GND), U6.19 (TESTEN), U6.57 (GND), U7.4 (GND), X1.2 (GND), Y1.2, Y1.4
HK_CSB: J4.A23 (CSB/mio[3]), J9.7, NT1.1, R33.2, U6.3 (GPIO1)
HK_SCK: J4.A26 (SCK/mio[4]), J9.6, U6.4 (GPIO2)
HK_SDI: J4.A24 (SDI/mio[2]), J9.9, U4.5
HK_SDO: J4.A21 (SDO/mio[1]), J9.10, U4.14
MUX_SEL: NT1.2, U4.1 (S)
unnamed: C1.2, R7.1, R12.2, SW1.1
unnamed: C3.1, J15.S1 (SHIELD), J15.S2 (SHIELD), J15.S3 (SHIELD), J15.S4 (SHIELD), R16.1
unnamed: C30.1, R37.1, Y1.3
unnamed: D1.2 (A), R15.2
unnamed: D2.2 (A), R17.2
unnamed: D3.2 (A), R18.2
unnamed: D4.2 (A), R19.2
unnamed: JP1.2 (B), R22.1
unnamed: JP2.2 (B), R23.1
unnamed: JP3.2 (B), R24.1
unnamed: JP4.2 (B), R25.1
unnamed: JP5.2 (B), R26.1
unnamed: JP6.2 (B), R27.1
unnamed: JP7.2 (B), R28.1
unnamed: JP8.2 (B), R29.1
unnamed: R1.2, SW4.8
unnamed: R2.2, SW4.7
unnamed: R3.2, SW4.6
unnamed: R4.2, SW4.5
unnamed: R5.2, SW4.4
unnamed: R6.2, SW4.3
unnamed: R10.2, SW4.2
unnamed: R11.2, SW4.1
unnamed: R8.2, R13.1, SW2.2
unnamed: R14.1, SW3.1
unnamed: R22.2, U1.7 (A)
unnamed: R23.2, U1.6 (B)
unnamed: R24.2, U1.4 (C)
unnamed: R25.2, U1.2 (D)
unnamed: R29.2, U1.5 (DP)
unnamed: R26.2, U1.1 (E)
unnamed: R27.2, U1.9 (F)
unnamed: R28.2, U1.10 (G)
unnamed: C29.1, U6.20 (XIN), Y1.1
unnamed: R37.2, U6.21 (XOUT)
unnamed: R44.2, U7.3 (IO2)
unnamed: R45.2, U7.7 (IO3)
RPIO29: J9.20, U6.41 (GPIO29_ADC3)
RP_proj_clk: R41.1, U6.2 (GPIO0)
SDI/out0: U4.7, U6.5 (GPIO3)
SDO/out1: U4.12, U6.6 (GPIO4)
VBUS: F1.1, J15.A4_B9 (VBUS), J15.B4_A9 (VBUS)
boot_mode: J11.2, R9.2, SW3.2, U5.1 (~CS), U6.56 (QSPI_SS)
cinc/out3: U4.9, U6.11 (GPIO8)
ctrl_ena: J4.A1 (mio[32]/ctrl_ena), J9.17, R31.1, U6.8 (GPIO6)
ctrl_sel_inc: J4.A3 (mio[34]/ctrl_sel_inc), J9.14, R30.1, U4.11
gpio: D4.1 (K), J4.A18 (GPIO)
in0: J2.1, J3.1 (IO1), J4.A32 (ui_in[0]/mio[8]), J13.1 (IO1), SW4.16, U6.12 (GPIO9)
in1: J2.2, J3.2 (IO2), J4.A33 (ui_in[1]/mio[9]), J13.4 (IO4), SW4.15, U6.13 (GPIO10)
in2: J2.3, J3.3 (IO3), J4.A34 (ui_in[2]/mio[10]), J12.3 (IO3), J13.2 (IO2), SW4.14, U6.14 (GPIO11)
in3: J2.4, J3.4 (IO4), J4.A35 (ui_in[3]/mio[11]), J14.9 (IO7), SW4.13, U6.15 (GPIO12)
in4: J3.7 (IO5), J4.A36 (ui_in[4]/mio[12]), J13.7 (IO5), SW4.12, U6.28 (GPIO17)
in5: J3.8 (IO6), J4.A37 (ui_in[5]/mio[13]), J13.10 (IO8), J14.7 (IO5), SW4.11, U6.29 (GPIO18)
in6: J3.9 (IO7), J4.A38 (ui_in[6]/mio[14]), J13.8 (IO6), SW4.10, U6.30 (GPIO19)
in7: J3.10 (IO8), J4.A39 (ui_in[7]/mio[15]), SW4.9, U6.31 (GPIO20)
mio33: J4.A4 (mio[33]), J9.18
mio35: J4.A6 (mio[35]), J9.16
mio37: J4.A5 (mio[37]), J9.13
mprj_io0: J4.A22 (JTAG/mio[0]), J9.11
out0: J1.3, J4.B32 (uo_out[0]/mio[16]), J6.1 (IO1), JP1.1 (A), U4.6
out1: J1.4, J4.B29 (uo_out[1]/mio[17]), J6.2 (IO2), JP2.1 (A), U4.13
out2: J1.5, J4.B30 (uo_out[2]/mio[18]), J6.3 (IO3), JP3.1 (A), U4.3
out3: J1.6, J4.B27 (mio[19]/uo_out[3]), J6.4 (IO4), J12.2 (IO2), J13.3 (IO3), JP4.1 (A), U4.10
out4: J4.B28 (mio[20]/uo_out[4]), J6.7 (IO5), J12.1 (IO1), J14.8 (IO6), JP5.1 (A), U6.16 (GPIO13)
out5: J4.B23 (mio[21]/uo_out[5]), J6.8 (IO6), J12.4 (IO4), JP6.1 (A), U6.17 (GPIO14)
out6: J4.B26 (mio[22]/uo_out[6]), J6.9 (IO7), J14.10 (IO8), JP7.1 (A), U6.18 (GPIO15)
out7: J4.B21 (mio[23]/uo_out[7]), J6.10 (IO8), J12.8 (IO6), J13.9 (IO7), JP8.1 (A), U6.27 (GPIO16)
project_clk: J4.A28 (clk/mio[6]), J17.3, R12.1, R41.2
uio0: J4.B22 (mio[24]/uio[0]), J5.1 (IO1), J8.1, J12.7 (IO5), U6.32 (GPIO21)
uio1: J4.B11 (mio[25]/uio[1]), J5.2 (IO2), J8.2, J12.10 (IO8), U6.34 (GPIO22)
uio2: J4.B9 (mio[26]/uio[2]), J5.3 (IO3), J8.3, J12.9 (IO7), U6.35 (GPIO23)
uio3: J4.B10 (mio[27]/uio[3]), J5.4 (IO4), J14.3 (IO3), J17.1, U6.36 (GPIO24)
uio4: J4.B7 (mio[28]/uio[4]), J5.7 (IO5), J14.1 (IO1), U6.37 (GPIO25)
uio5: J4.B8 (mio[29]/uio[5]), J5.8 (IO6), J14.4 (IO4), U6.38 (GPIO26_ADC0)
uio6: J4.B5 (mio[30]/uio[6]), J5.9 (IO7), J14.2 (IO2), U6.39 (GPIO27_ADC1)
uio7: J4.B6 (mio[31]/uio[7]), J5.10 (IO8), U6.40 (GPIO28_ADC2)
usb_d+: J15.A6 (DP1), J15.B6 (DP2), U6.47 (USB_DP)
usb_d-: J15.A7 (DN1), J15.B7 (DN2), U6.46 (USB_DM)
usrclk2: J4.A27 (usrclk2/mio[5]), J9.5
xclk: J4.A11 (XCLK), X1.3 (OUT)
~crst/out2: U4.4, U6.9 (GPIO7)
~ctrl_sel_rst: J4.A8 (mio[36]/~ctrl_sel_rst), J9.12, R32.2, U4.2
~project_rst: C2.1, J4.A31 (~rst/mio[7]), J17.2, R13.2, U6.7 (GPIO5)

Notes on the sheet:
Main
RP2040
